u-blox/blueprints_sho_altium/Designs/B225_NINA-B112_carrier_small/BOM/B225 NINA-B112 CS_B_MFG_BOM.xlsx

Description | Designator | Footprint | Quantity | Manufacturer | Manufacturer P/N | Manufacturer Part Number
Chip Capacitor, 0.1 uF, +/- 5%, 16 V, 0402 (1005 Metric) | C1, C2 | CAPC1005X56X25ML10T15 | 2
Diode, ESD9B, 3.3V, ST5G, SOD-923 | D1, D2 | SOD-923 | 2 | ON Semiconductor | ESD9B3.3ST5G
LED, RGB Diffused SMT, PLCC4 4 Pin | D3 | 4-PLCC | 1 | Cree, Inc. | CLMVB-FKA-CFHEHLCBB7a363
Chip Inductor, 56 nH, +/-5%, 390 mA, -55 to 125 degC, 0603 (1608 Metric), RoHS, Tape and Reel | L1, L2 | INDC1608X100X30LL20T10 | 2 | Murata
1.5M screw mounting hole, plated | MH1, MH2 | MH_M1.5 | 2
THT Angled Pin Header WR-PHD, Pitch 2.54 mm, Single Row, 8 pins | P1 | 61300811021 | 1 | Wurth Elektronik |  | 61300811021
CON PADS FOR CBL PLUG-OF-NAILS 6-PIN NO LEGS | P2 | TC2030-IDC-NL | 1 | TAG Connect | TC2030-IDC-NL
Resistor, 499ohm, 1%, 1/16W, 0402 | R1 | RES 0402 HD | 1 | Rohm Semiconductor | MCR01MRTF4990
Resistor, 220ohm, 5%, 1/16W, 0402. | R2, R3, R4, R5, R6, R7, R8, R9, R10, R11, R15, R16, R17 | RES 0402 HD | 13 | Panasonic Electronic Components, [NoParam] | ERJ-2GEJ221X, [NoParam]
Button, Momentary SPST-NO, 0.05A, 12V, 3mm x 2.5mm | SW1, SW2 | B3U-1000P | 2 | Omron Electronics Inc-EMC Div | B3U-1000P
u-blox NINA-B112 Bluetooth 5 LE module | U1 | NINA_LGA42R_1400X1000X380_PIFA | 1 | u-blox
