u-blox/blueprints_sho_altium/Designs/B233_NORA-B106_carrier_small/BOM/B233 NORA-B106 CS_A_MFG_BOM.xlsx

Description | Designator | Footprint | Quantity | Manufacturer | Manufacturer P/N | Manufacturer Part Number
CAP CER X5R 0402 | C1 | Cap 0402 | 1 | Samsung Electro-Mechanics | CL05A104KP5NNN
Testpoint, Round 1.0mm Dia | CTS_NET1, RTS_NET1 | TP10R | 2
Diode, ESD9B, 3.3V, ST5G, SOD-923 | D1, D2 | SOD-923 | 2 | ON Semiconductor | ESD9B3.3ST5G
LED, RGB Diffused SMT, PLCC4 4 Pin | D3 | 4-PLCC | 1 | Cree, Inc. | CLMVB-FKA-CFHEHLCBB7a363
Chip Inductor, 22 nH, +/-5%, 640 mA, -55 to 125 degC, 0603 (1608 Metric), RoHS, Tape and Reel | L1, L2 | INDC1608X100X30LL20T10 | 2 | Murata
2M screw mounting hole, plated | MH1, MH2 | MH_M2 | 2
CON PADS FOR CBL PLUG-OF-NAILS 6-PIN NO LEGS | P1 | TC2030-IDC-NL | 1 | TAG Connect | TC2030-IDC-NL
THT Angled Pin Header WR-PHD, Pitch 2.54 mm, Single Row, 8 pins | P2 | 61300811021 | 1 | Wurth Electronics |  | 61300811021
Resistor, 220ohm, 5%, 1/16W, 0402. | R1, R2, R3, R4, R5, R6, R7, R8, R9, R10, R11, R12, R13, R15, R16 | RES 0402 HD | 15 | Panasonic Electronic Components | ERJ-2GEJ221X
Resistor, 499ohm, 1%, 1/16W, 0402 | R14 | RES 0402 HD | 1 | Rohm Semiconductor | MCR01MRTF4990
Button, Momentary SPST-NO, 0.05A, 12V, 3mm x 2.5mm | SW1, SW2 | B3U-1000P | 2 | Omron Electronics Inc-EMC Div | B3U-1000P
u-blox NORA-B106 Bluetooth 5.2 LE module - dual core | U1 | NORA_LGA82R_1430X1040X180_ANT | 1 | u-blox | NORA-B106-00B
XTAL, 2Pin, 32.768kHz, 7pF 20ppm | X1 | XTAL_3215 | 1 | Epson | FC-135 32.7680KA-AG3
