u-blox/blueprints_sho_altium/Designs/B228_NINA-B306_carrier_mid/Documentation/B228 B.PDF

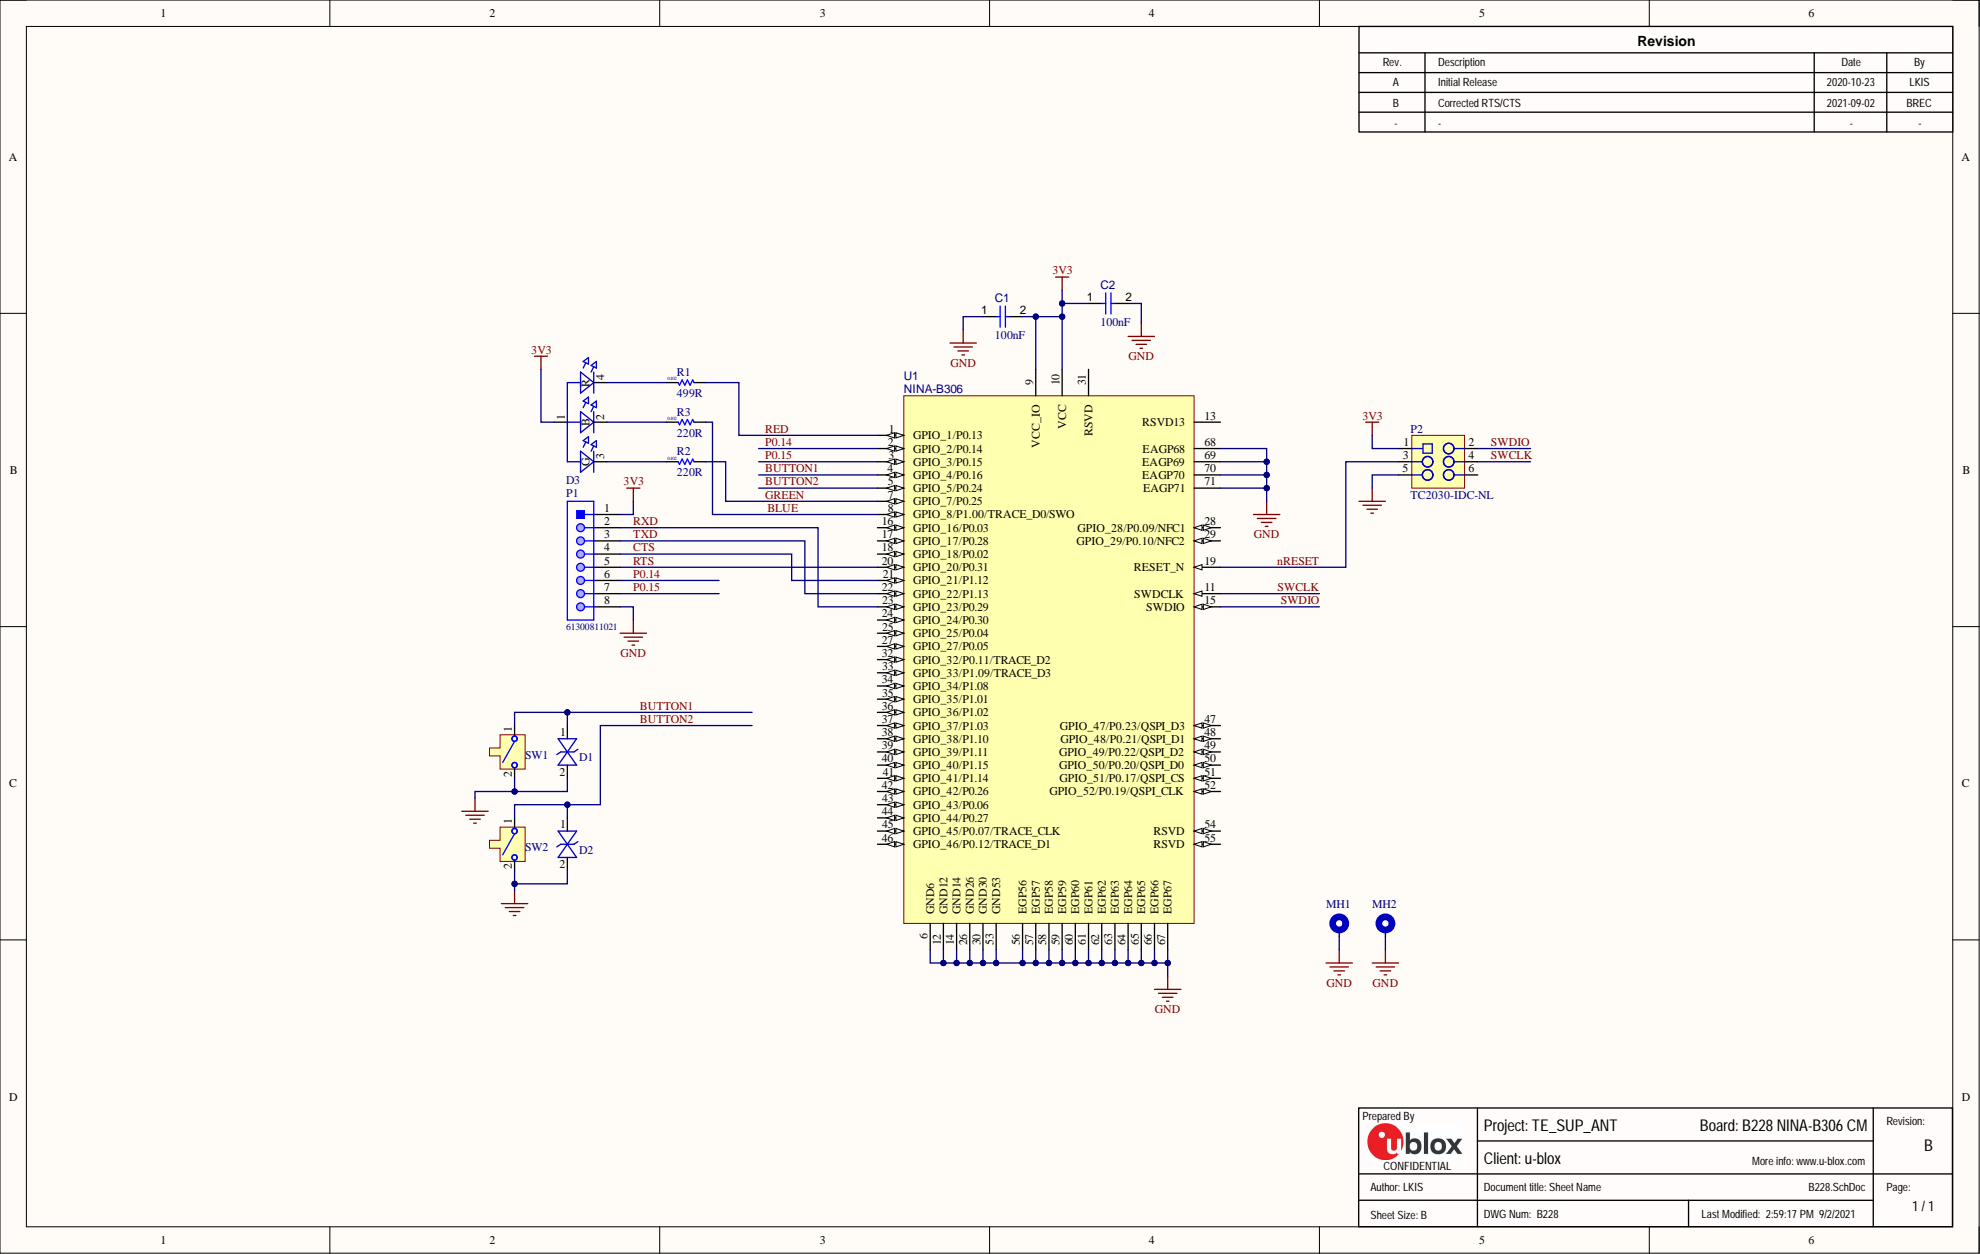
[picture p19: page 1]

Rev. | Description | Date | By
A | Initial Release | 2020-10-23 | LKIS

B | Corrected RTS/CTS | 2021-09-02 | BREC

P0.14 P0.15 BUTTON1 BUTTON2 GREEN | GPIO_2/P0.14 2 GPIO_4/P0.16 4 GPIO_3/P0.15 3 GPIO_5/P0.24 5 GPIO_7/P0.25 7

BLUE | GPIO_8/P1.00/TRACE_D0/SWO 8

3 | TXD | GPIO_17/P0.28 17
4 | CTS | GPIO_18/P0.02 18
5 | RTS | GPIO_20/P0.31 20
6 | P0.14 | GPIO_21/P1.12 21
7 | P0.15 | GPIO_23/P0.29 23 GPIO_22/P1.13 22

nRESET

GPIO_25/P0.04 25 GPIO_24/P0.30 24

More info: www.u-blox.com

Author: LKIS | Document title: Sheet Name B228.SchDoc | Page: 1 / 1

Sheet Size: B | DWG Num: B228 | Last Modified: 2:59:17 PM 9/2/2021

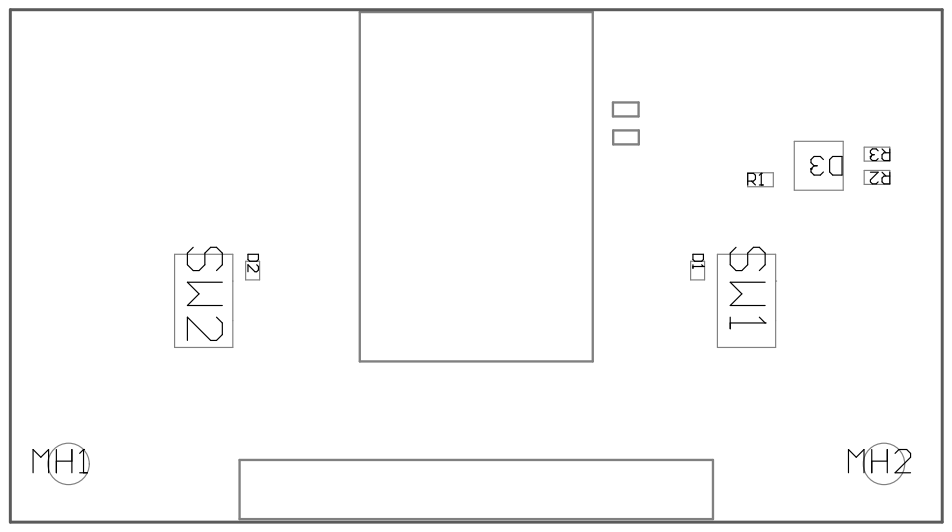
[picture p20: page 2]

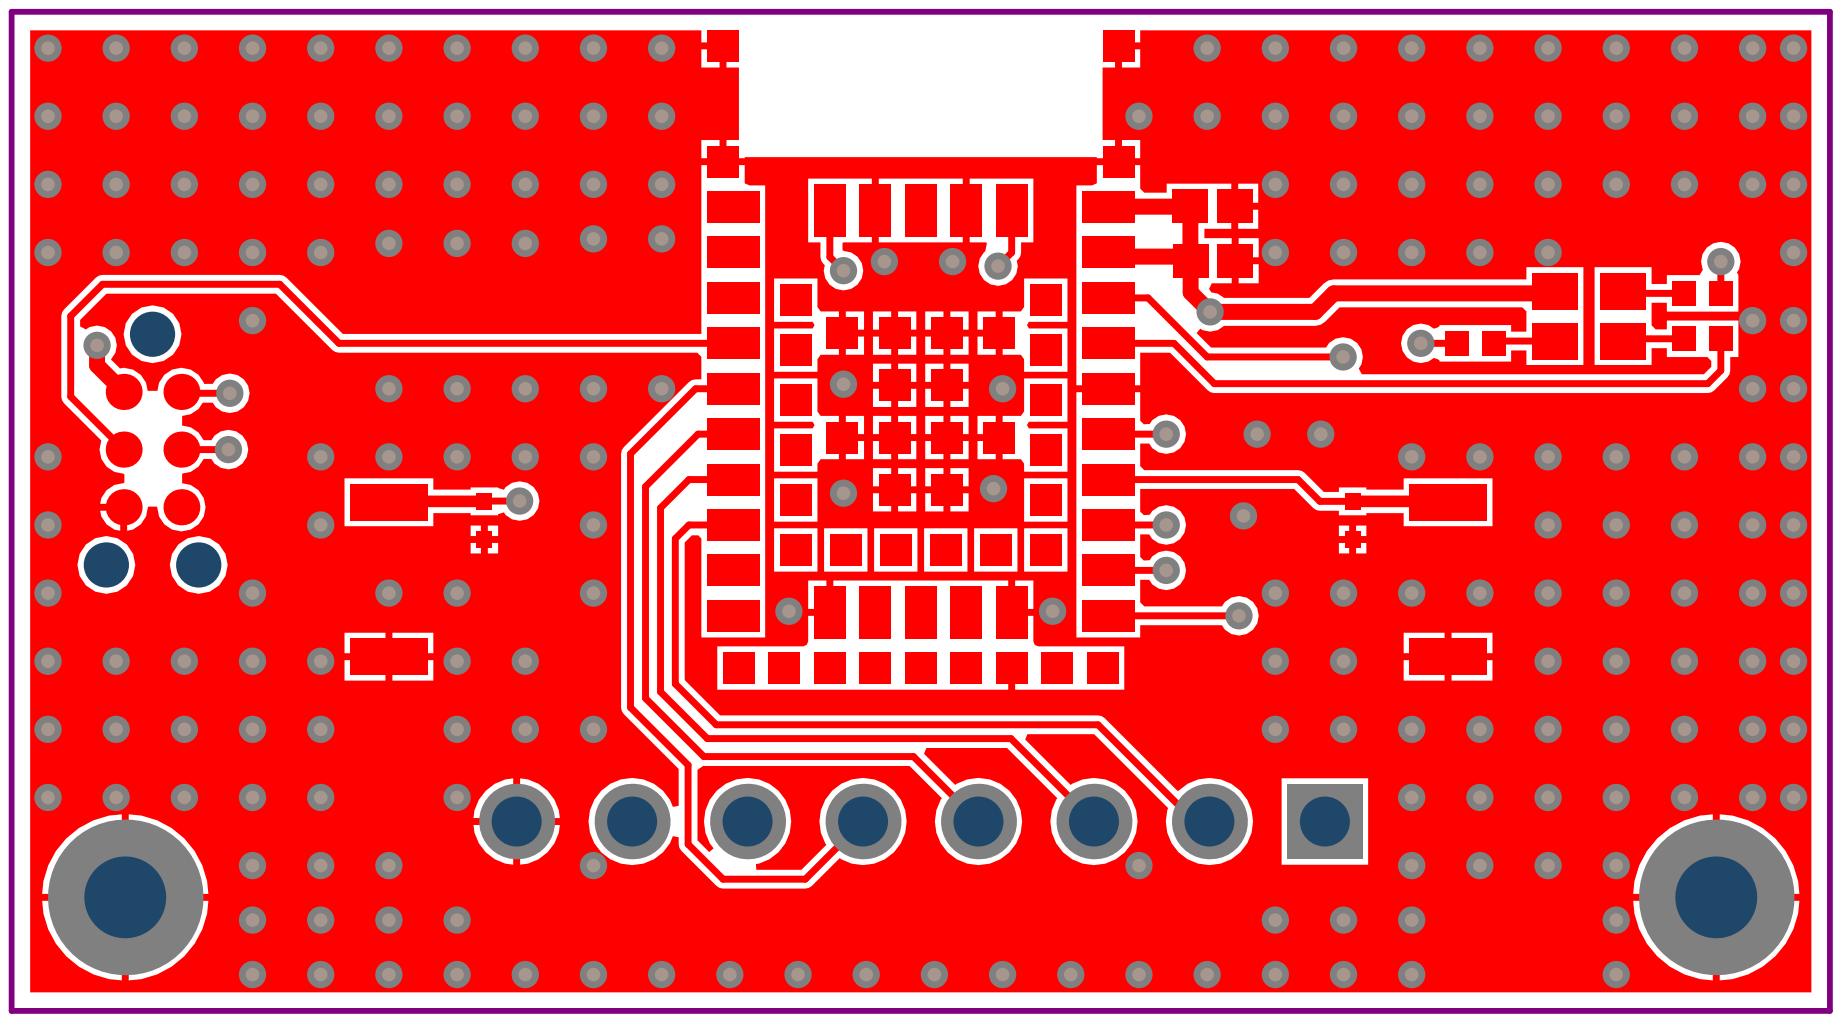
[picture p21: page 4]

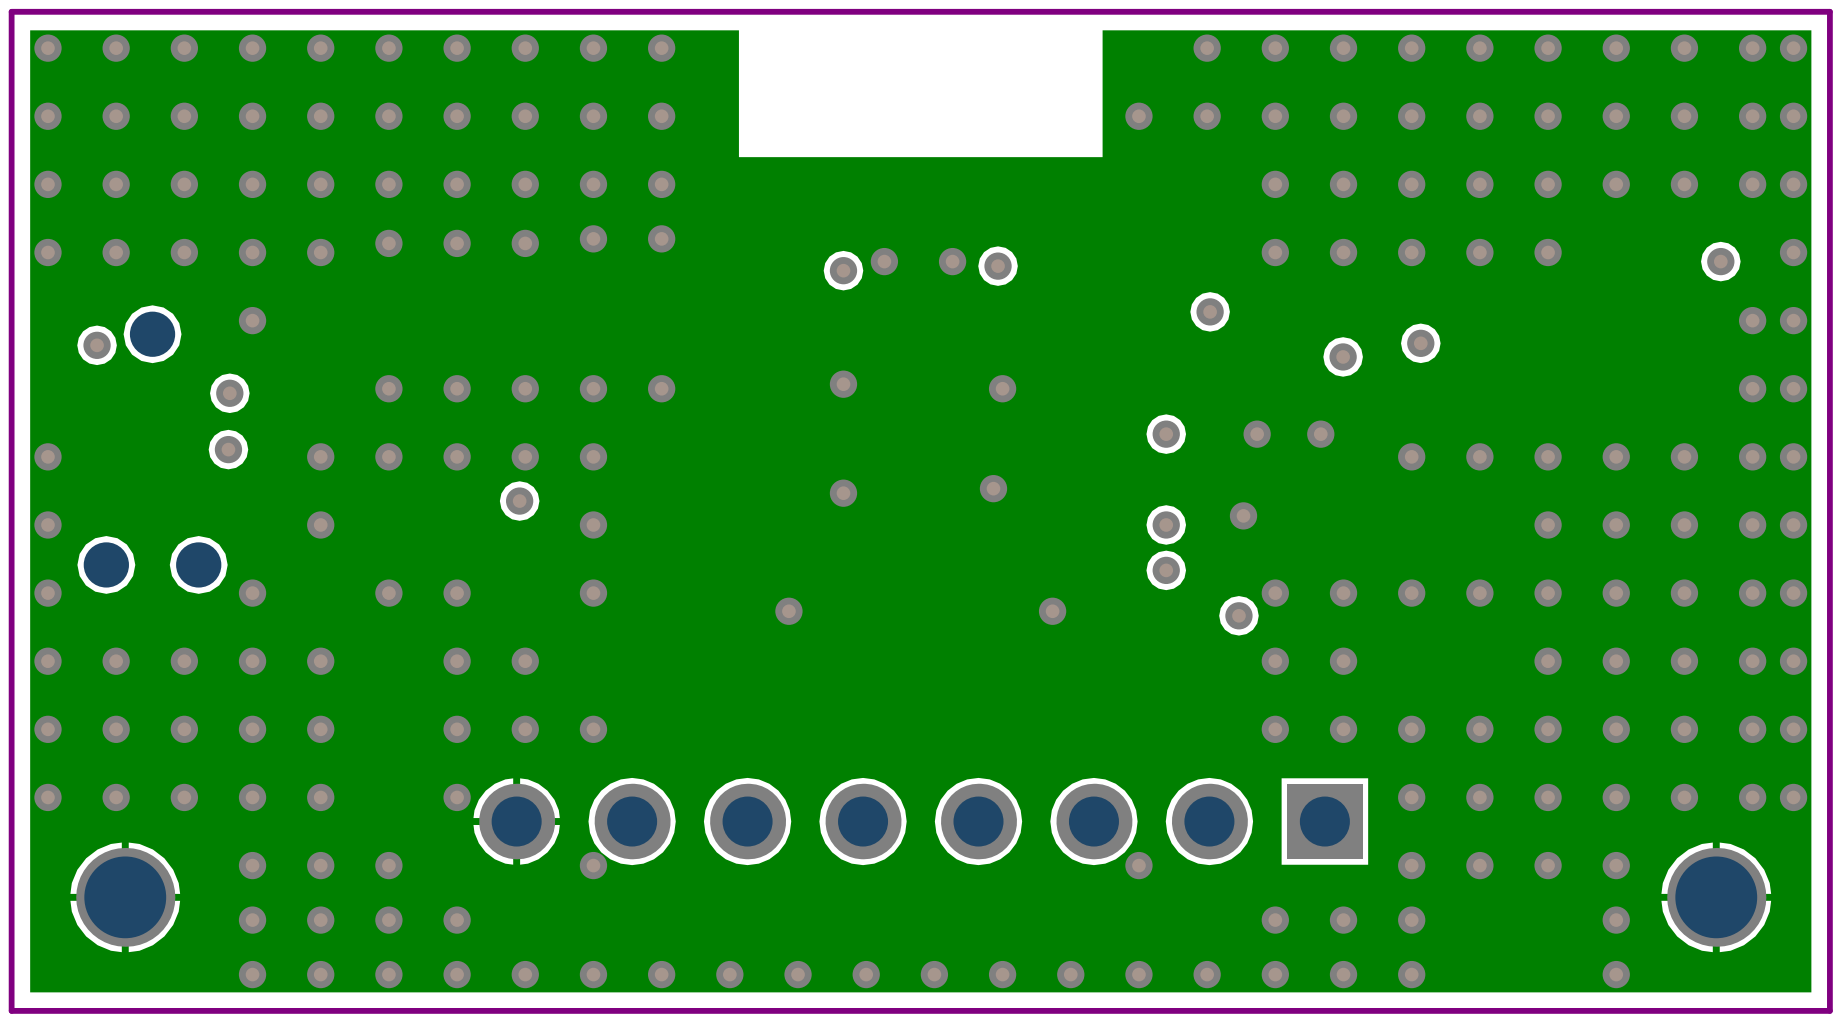
[picture p22: page 5]

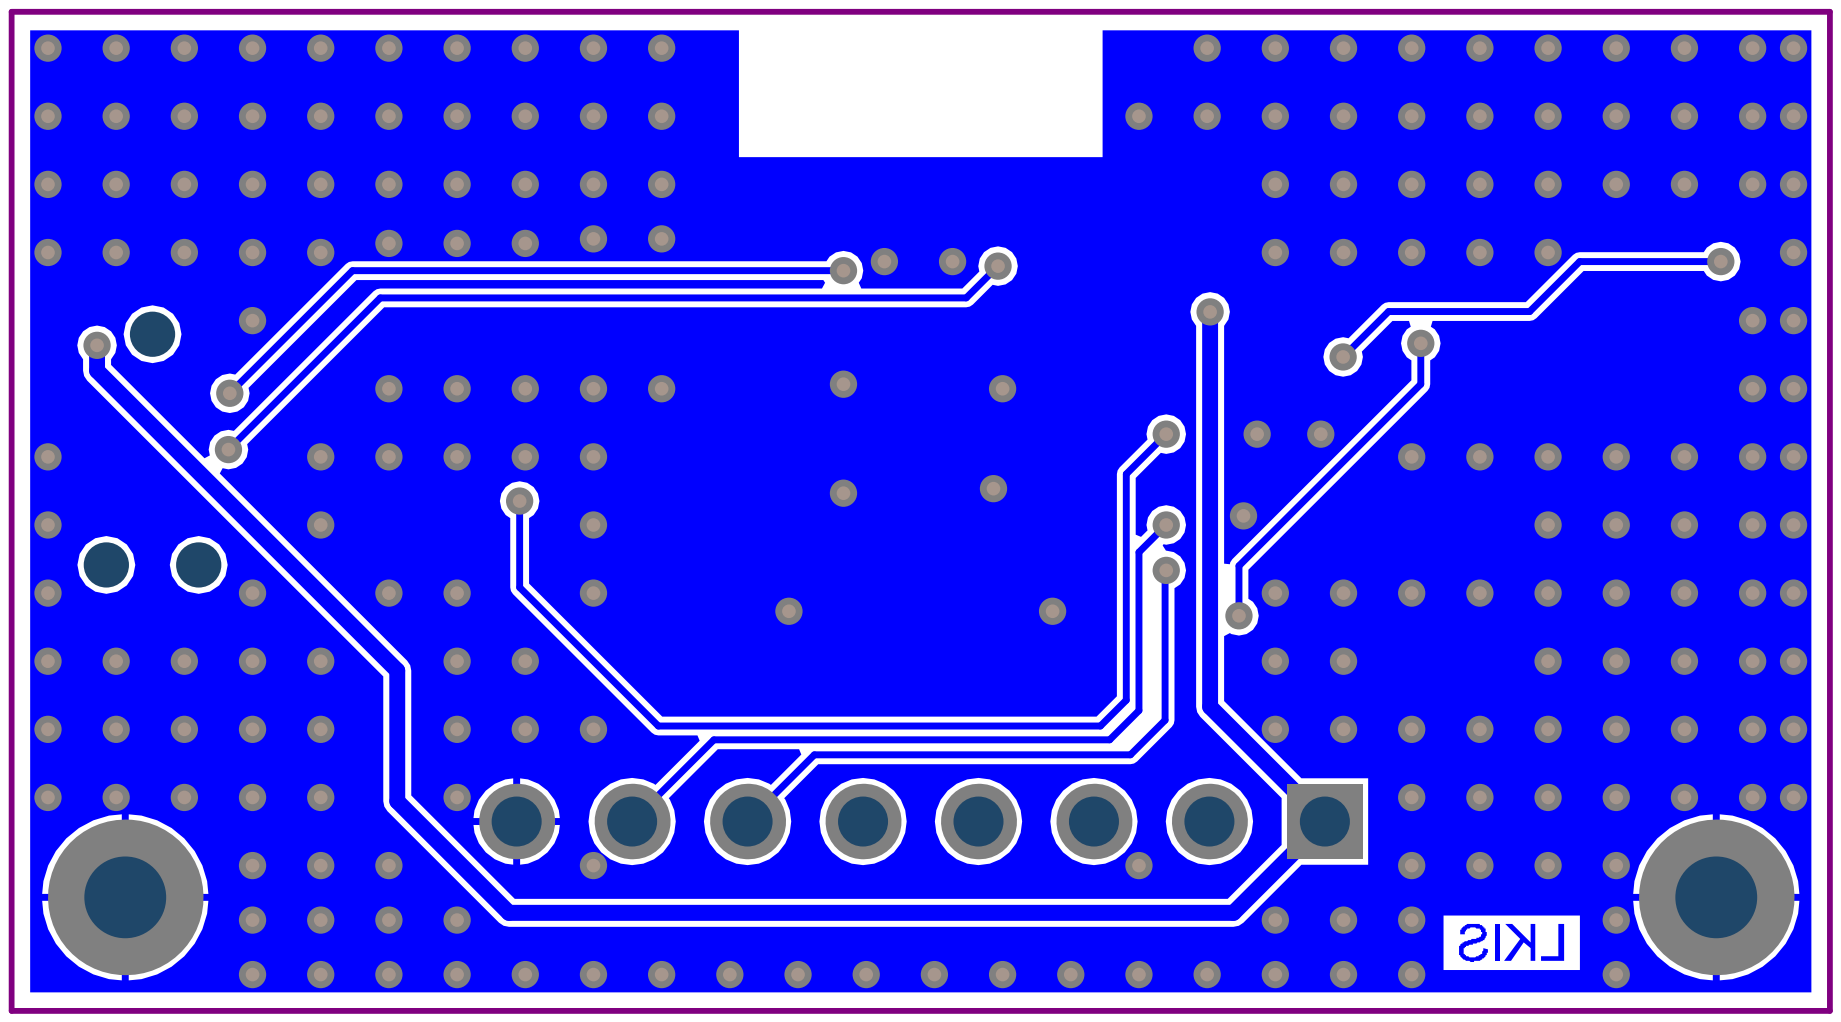
[picture p23: page 7]

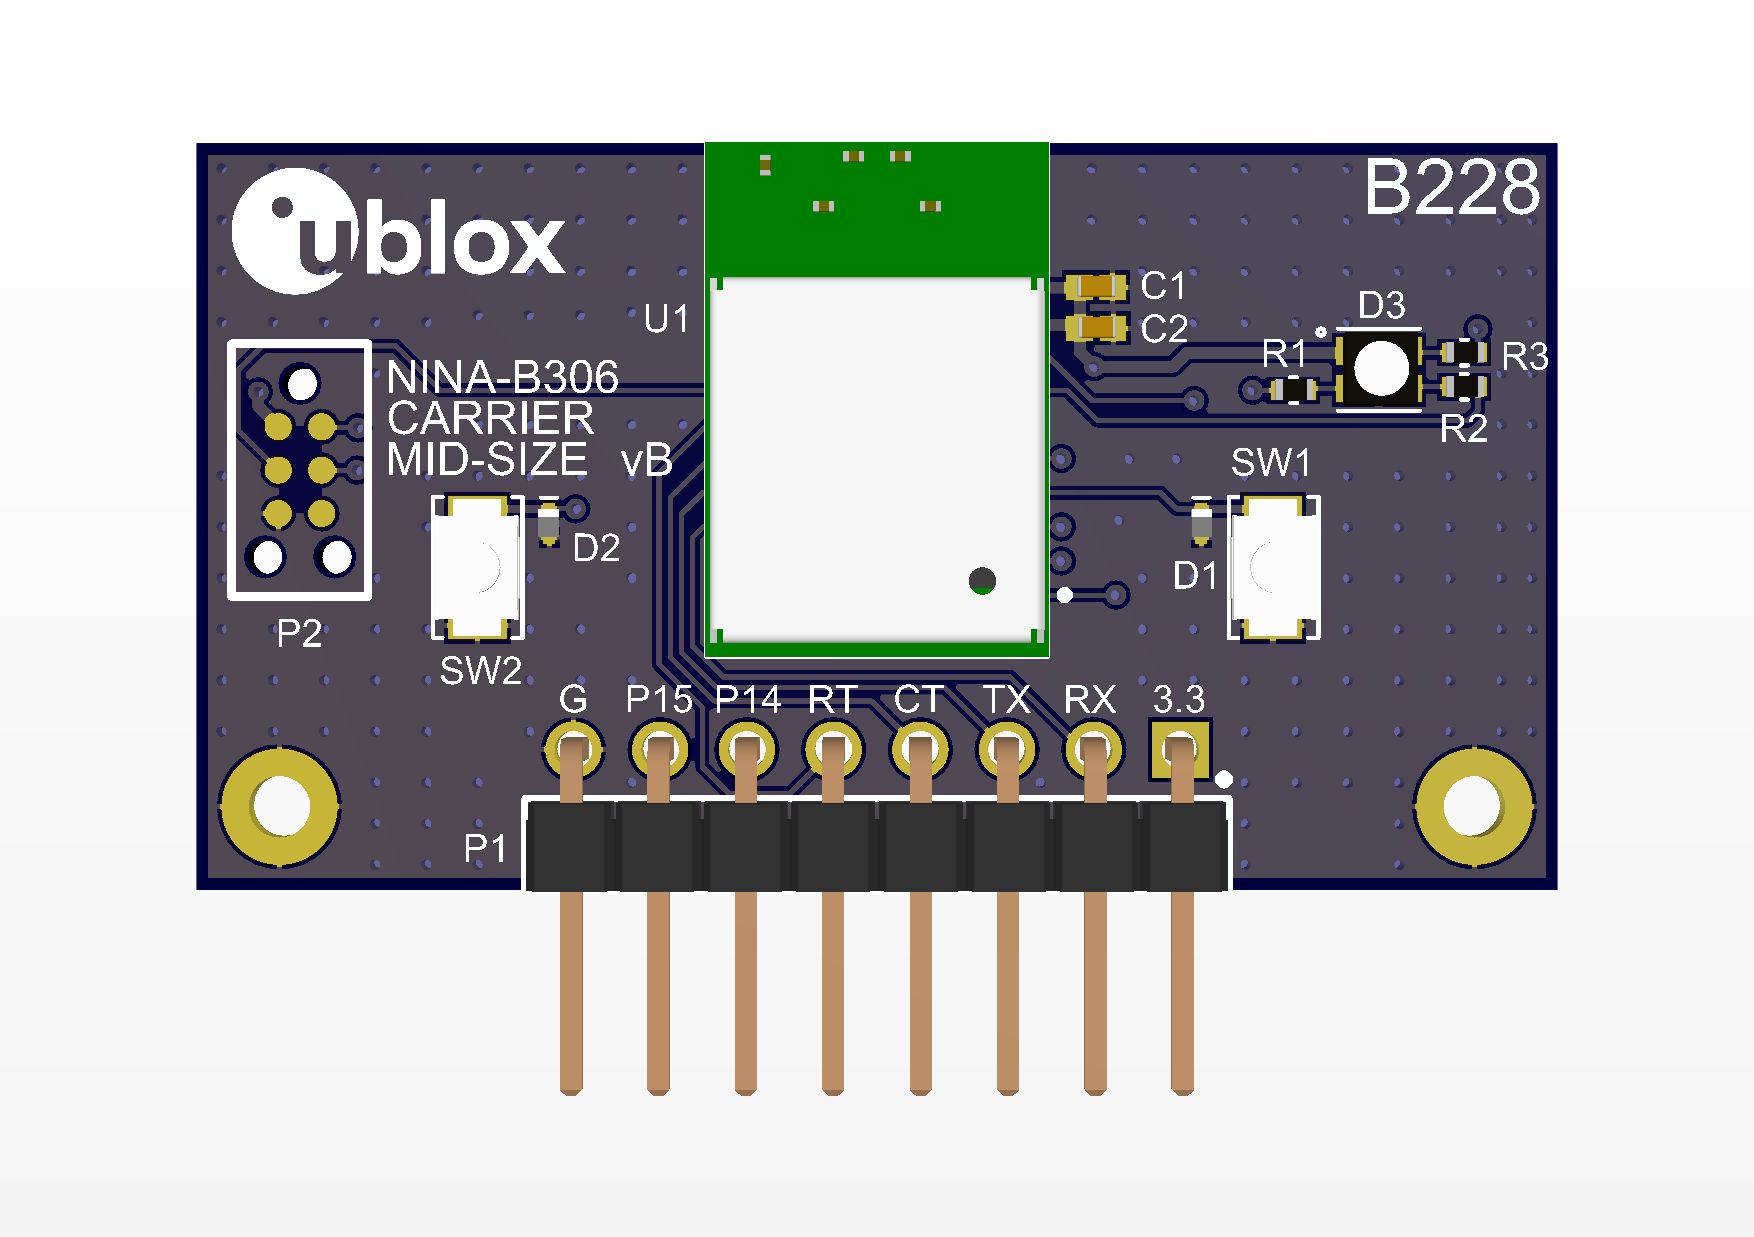
[picture p24: page 8]

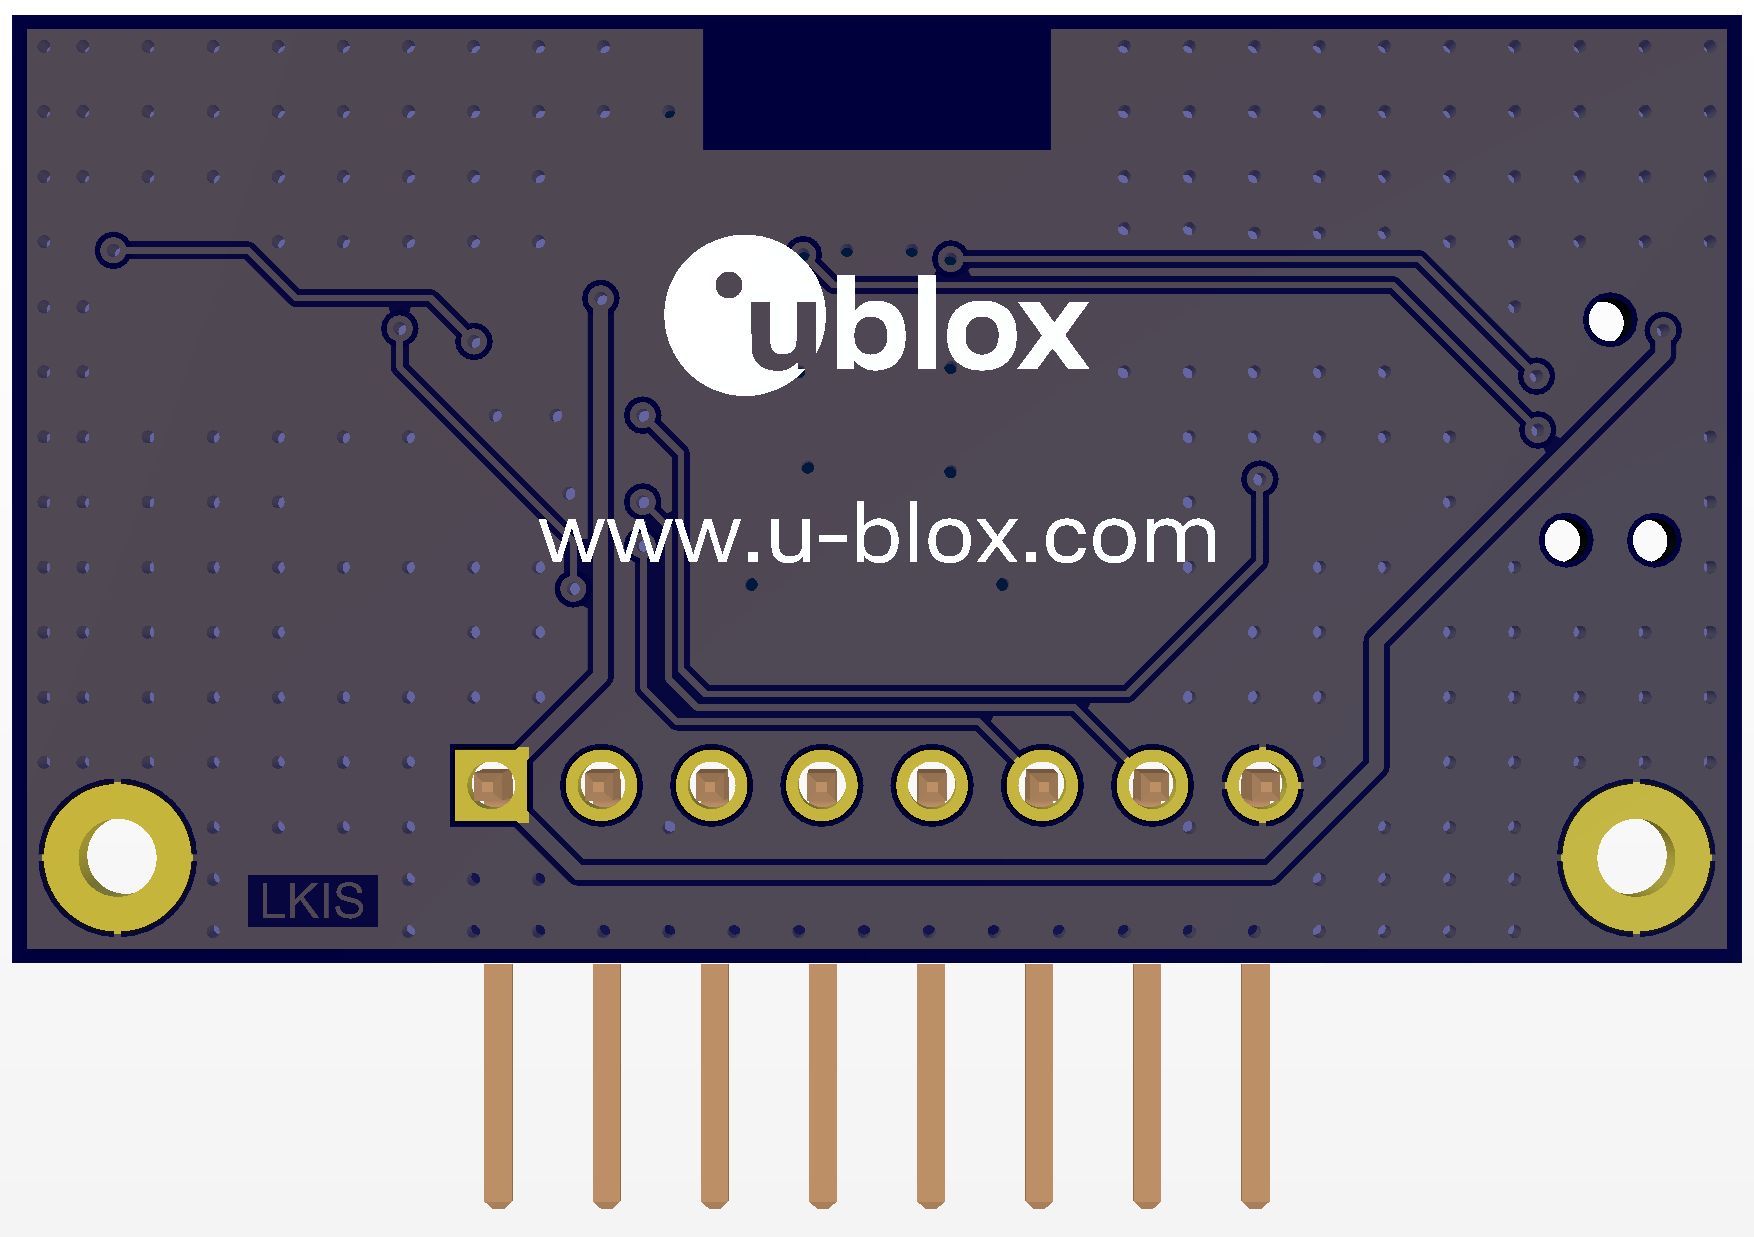
[picture p25: page 9]

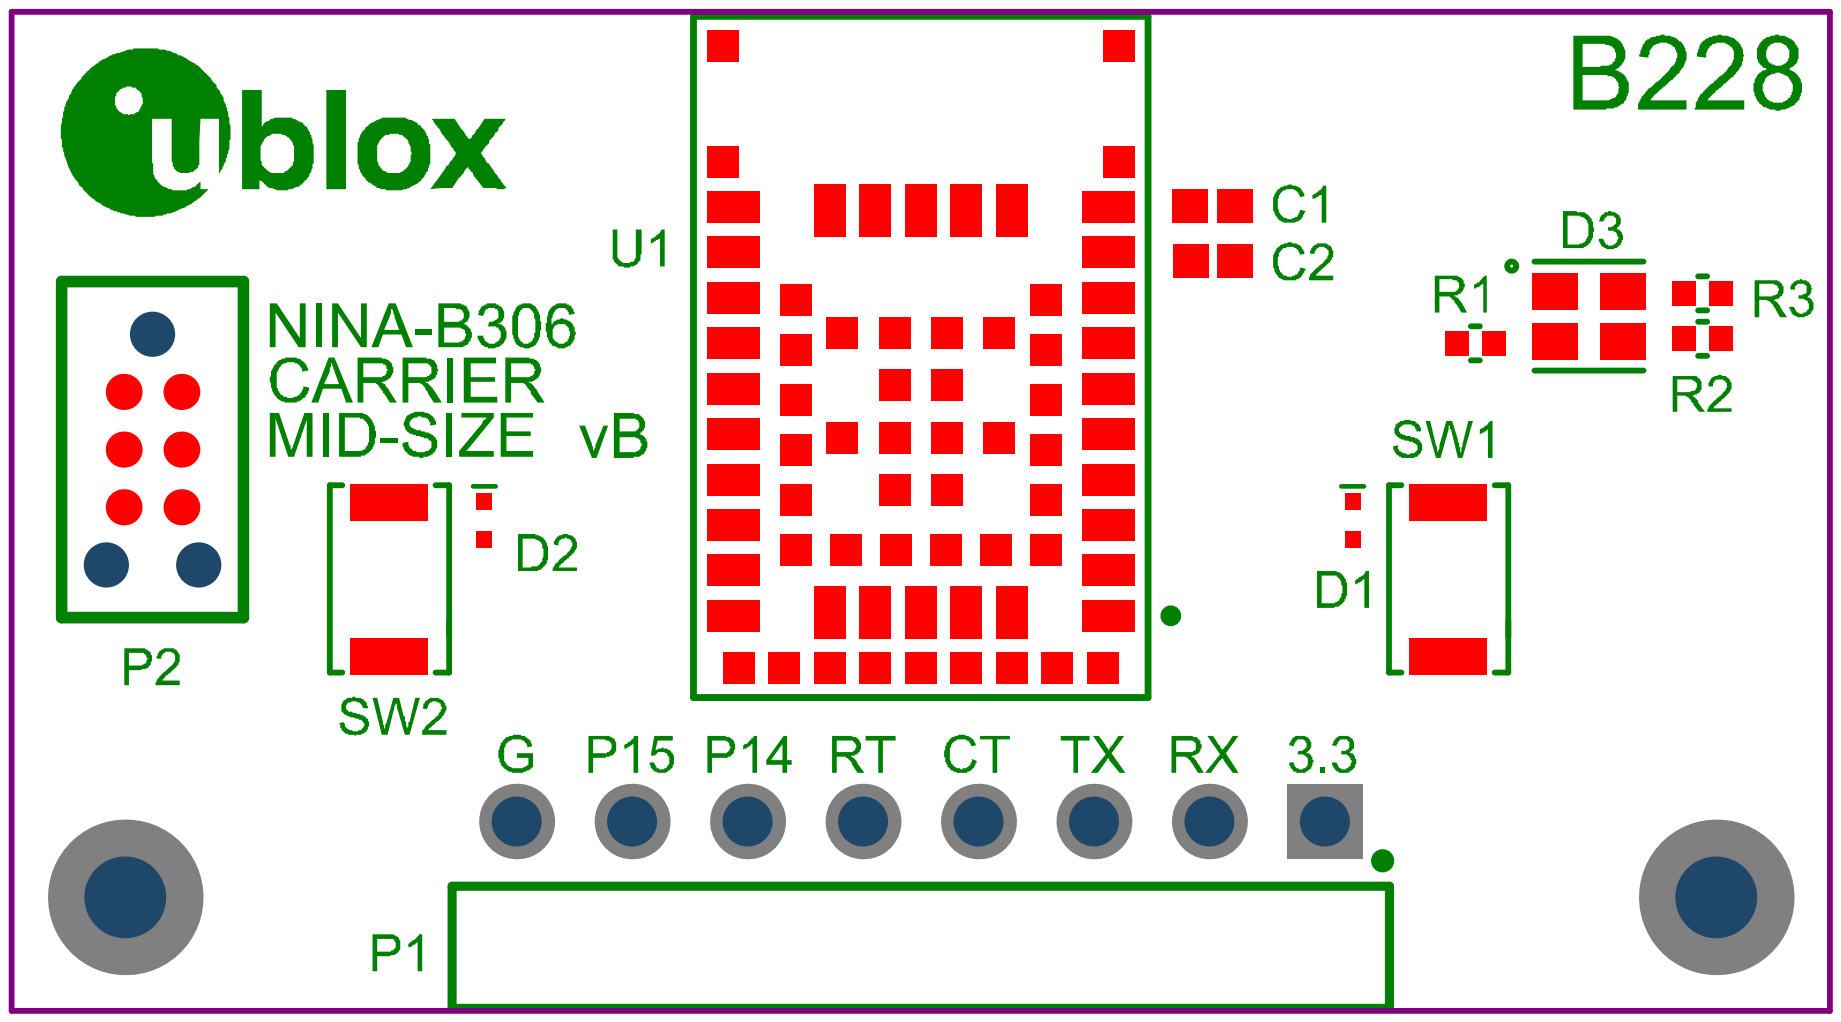
[picture p26: page 11]

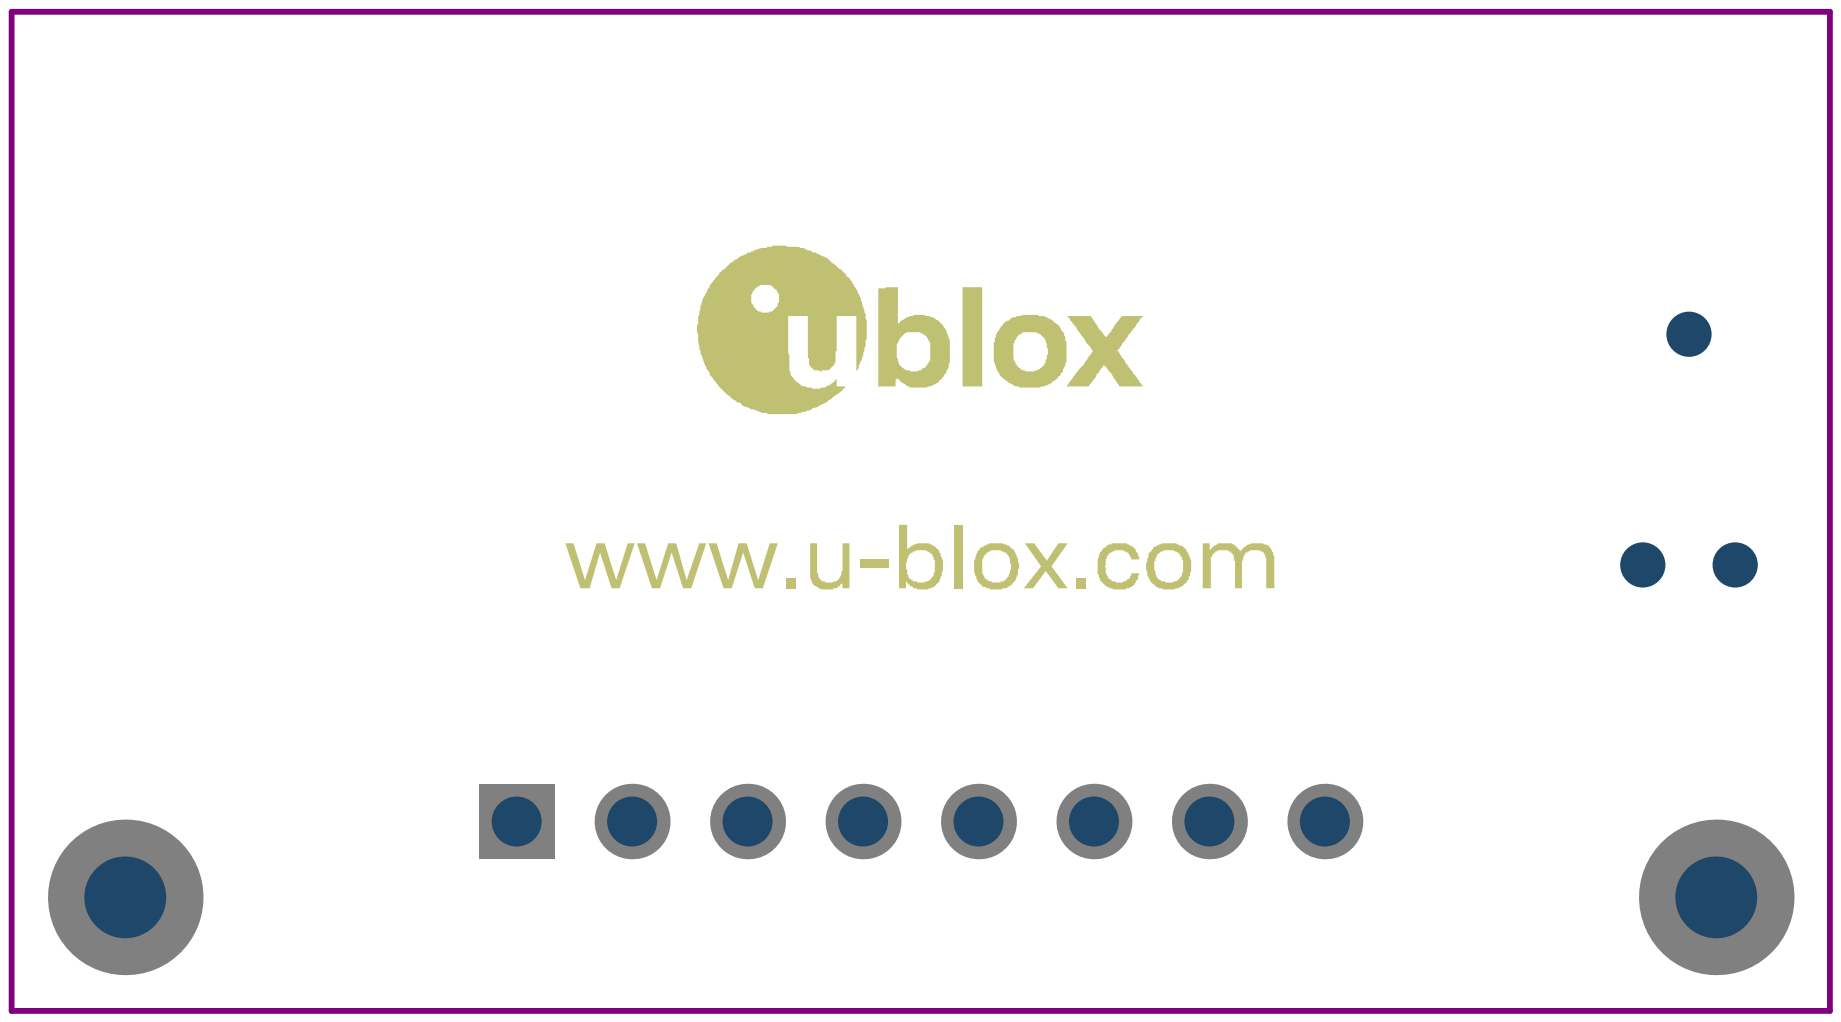
[picture p27: page 12]
