u-blox/blueprints_sho_altium/Designs/B232_NORA-B106_carrier_mid/Documentation/B232 A.PDF

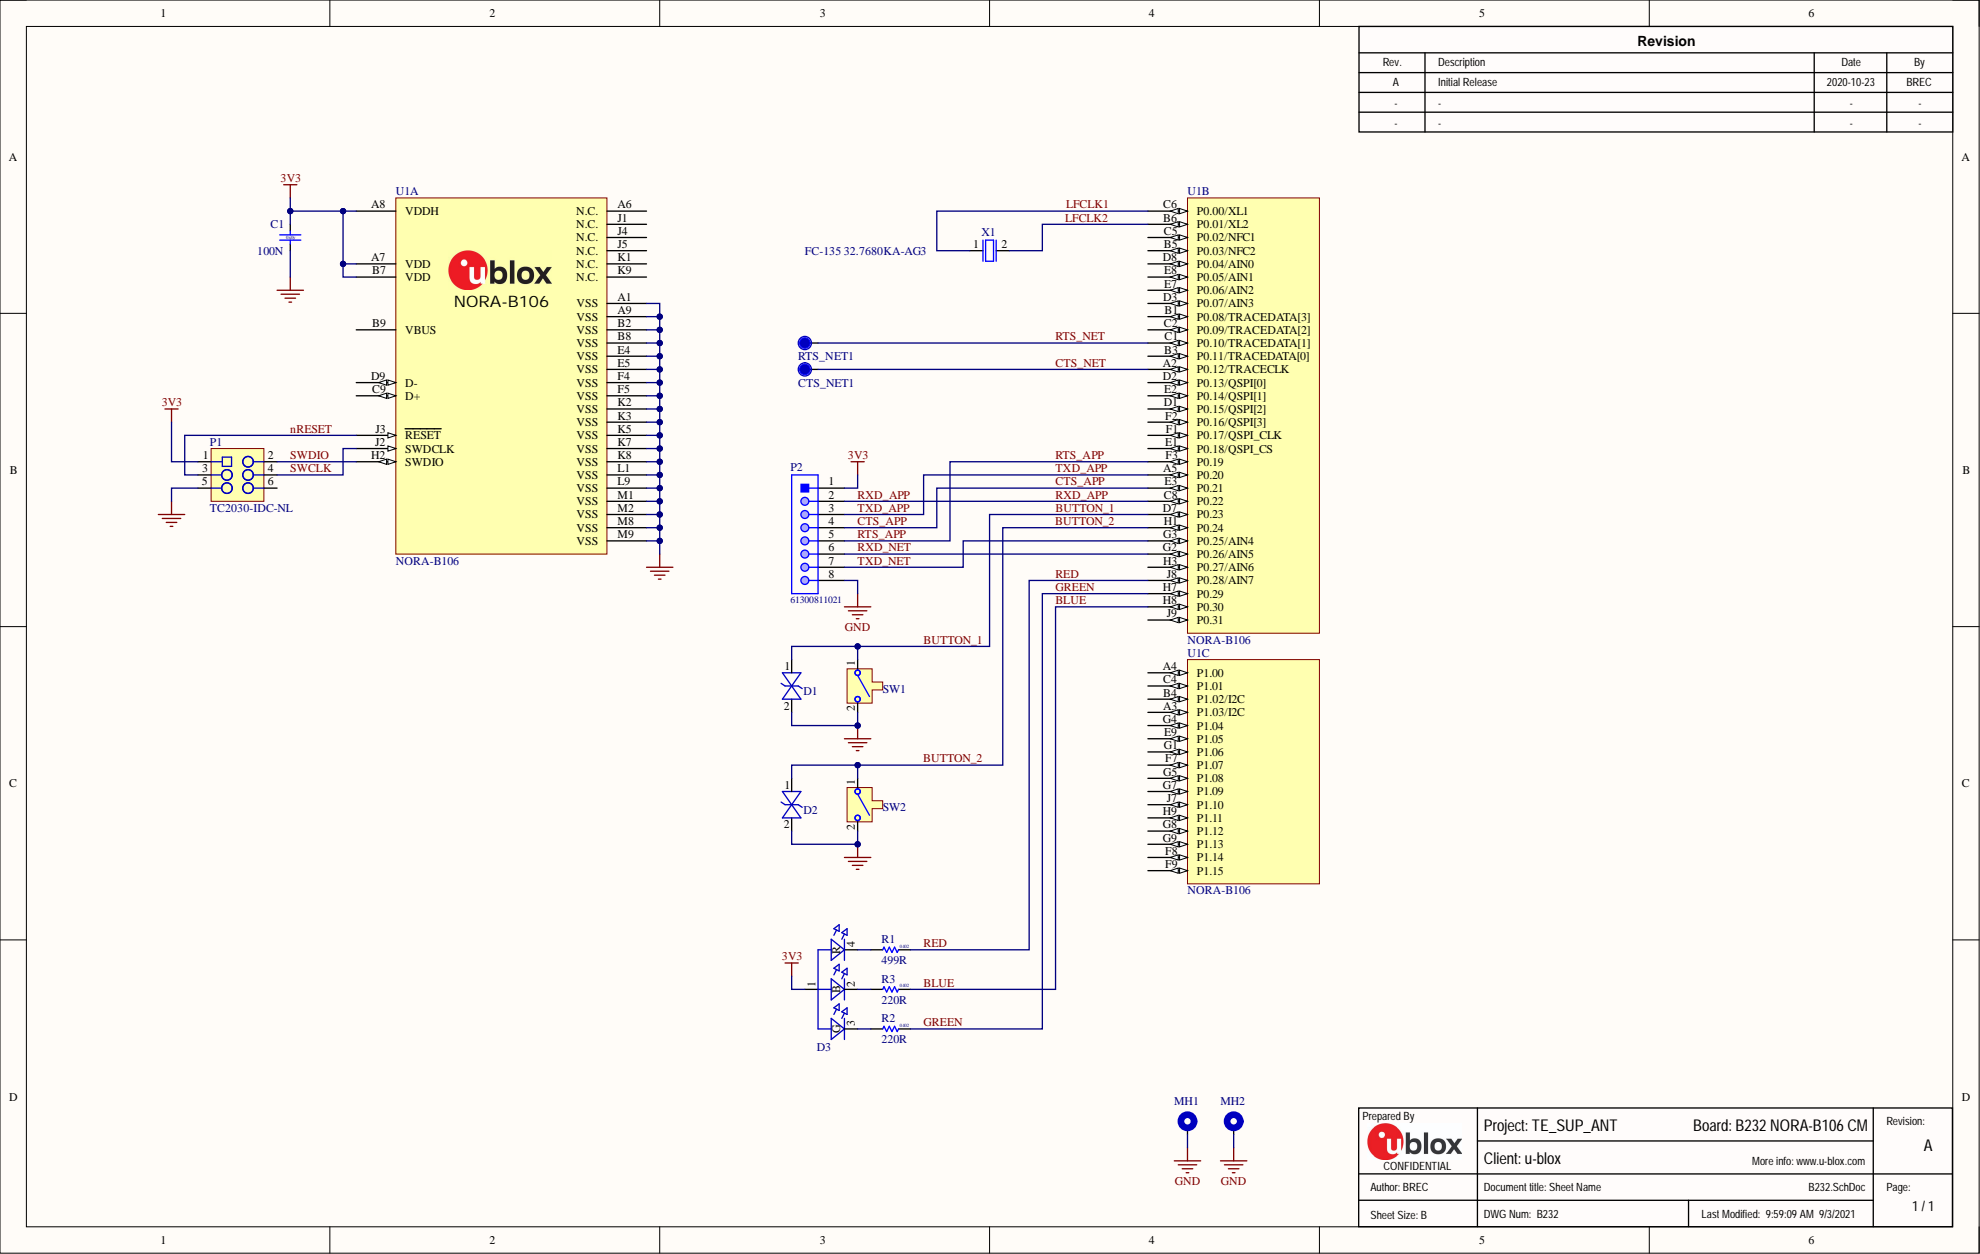
[picture p28: page 1]

Rev. | Description | Date | By
A | Initial Release | 2020-10-23 | BREC

2 | RXD_APP | P0.22 C8

CTS_APP | P0.21 E3

5 | | RTS_APP | | P0.25/AIN4 G3
6 | | RXD_NET | | P0.26/AIN5 G2
7 | | TXD_NET | | P0.27/AIN6 H3
8 | | | RED | P0.28/AIN7 J8

GREEN | | P0.29 H7
BLUE | | P0.30 H8

BUTTON_1 | | | P0.31 J9

BUTTON_2

More info: www.u-blox.com

Author: BREC | Document title: Sheet Name B232.SchDoc | Page: 1 / 1

Sheet Size: B | DWG Num: B232 | Last Modified: 9:59:09 AM 9/3/2021

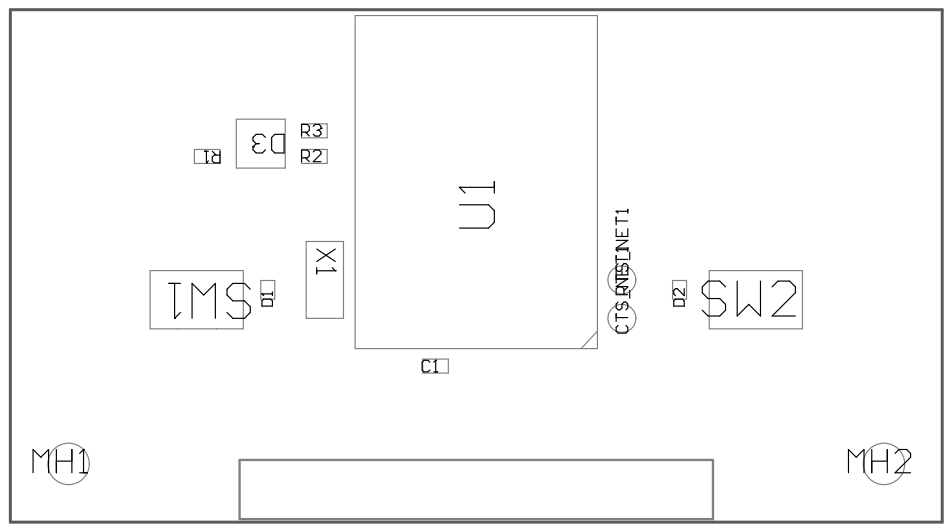
[picture p29: page 2]

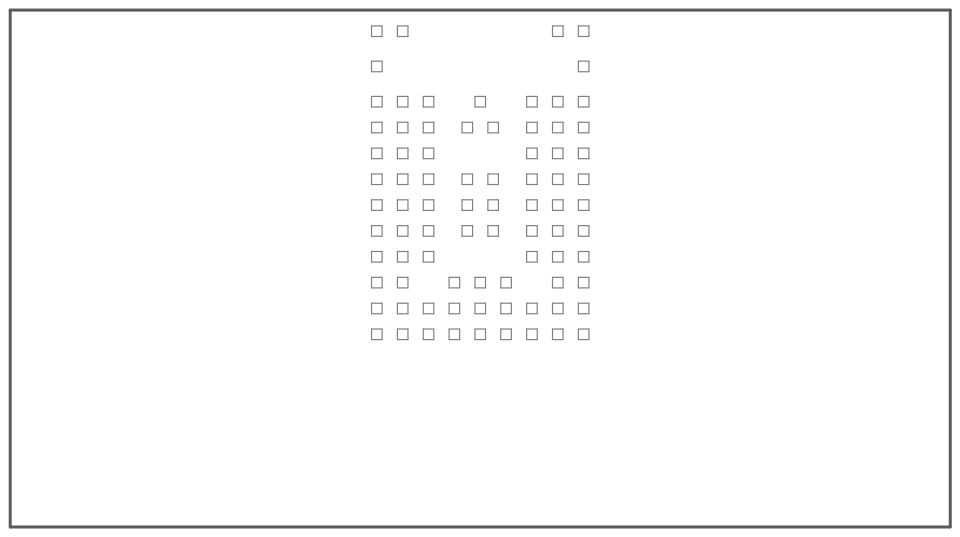
[picture p30: page 3]

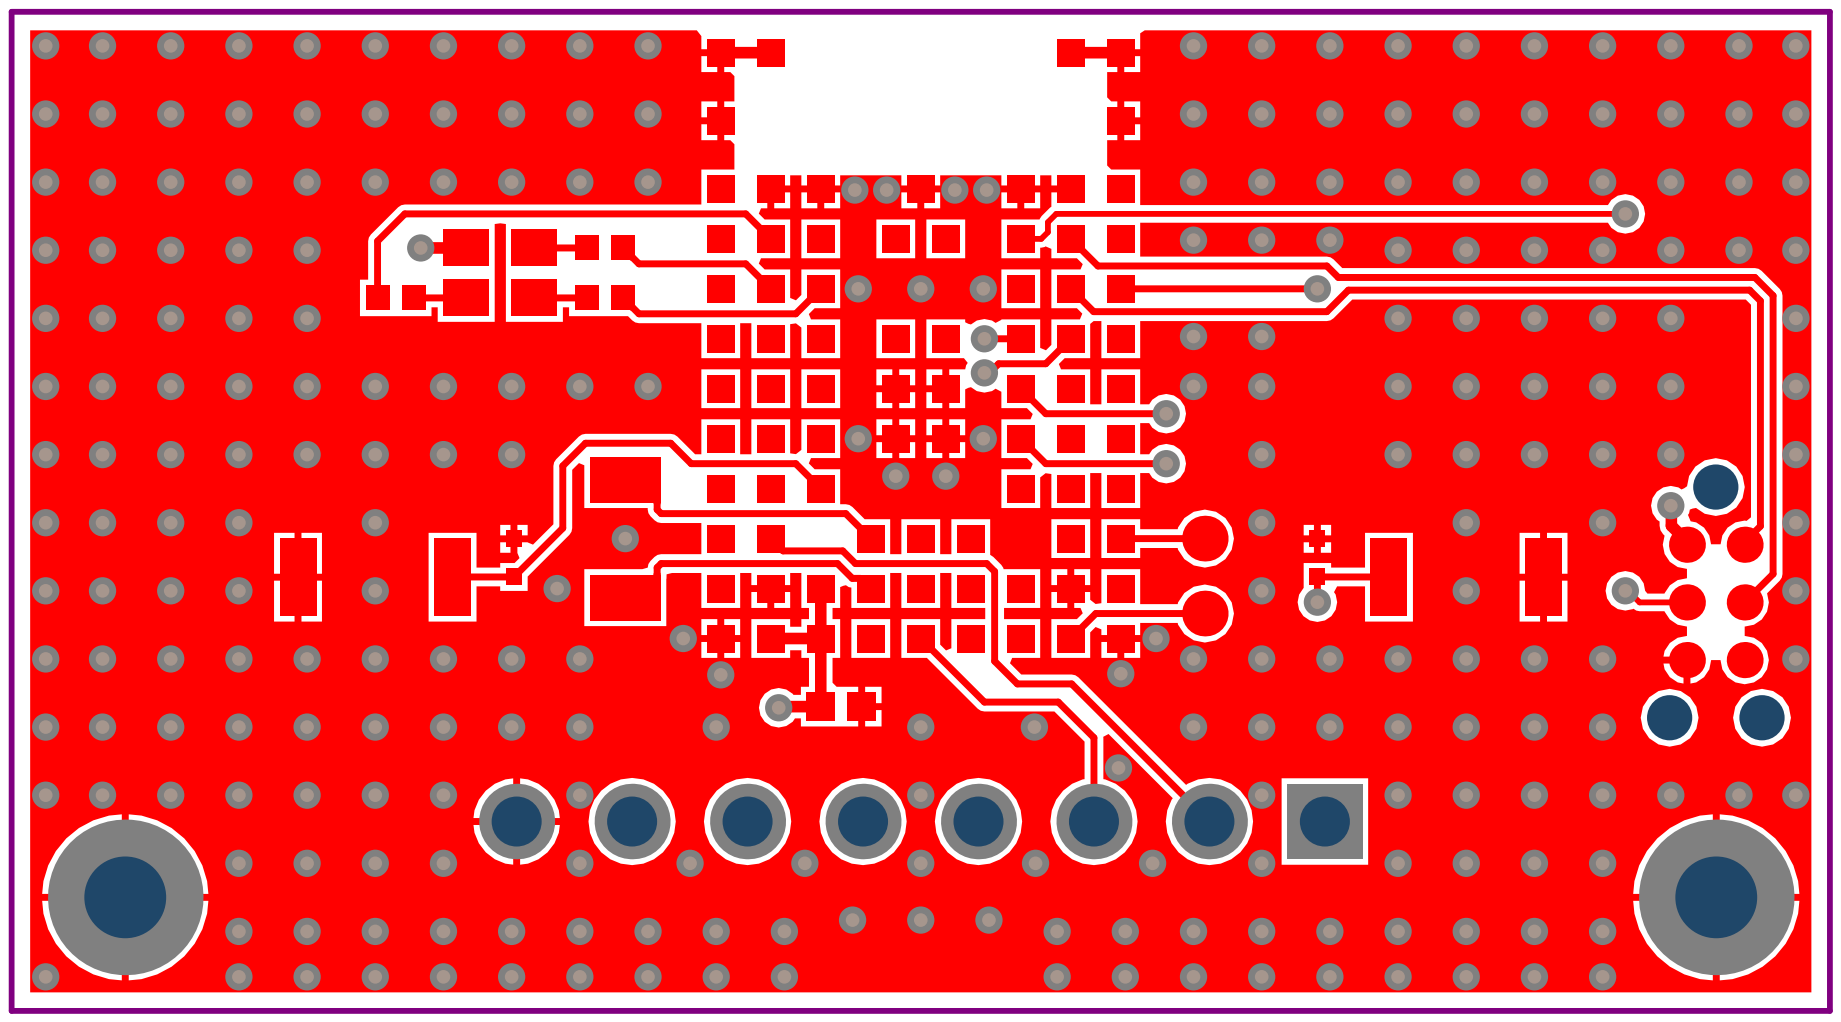
[picture p31: page 4]

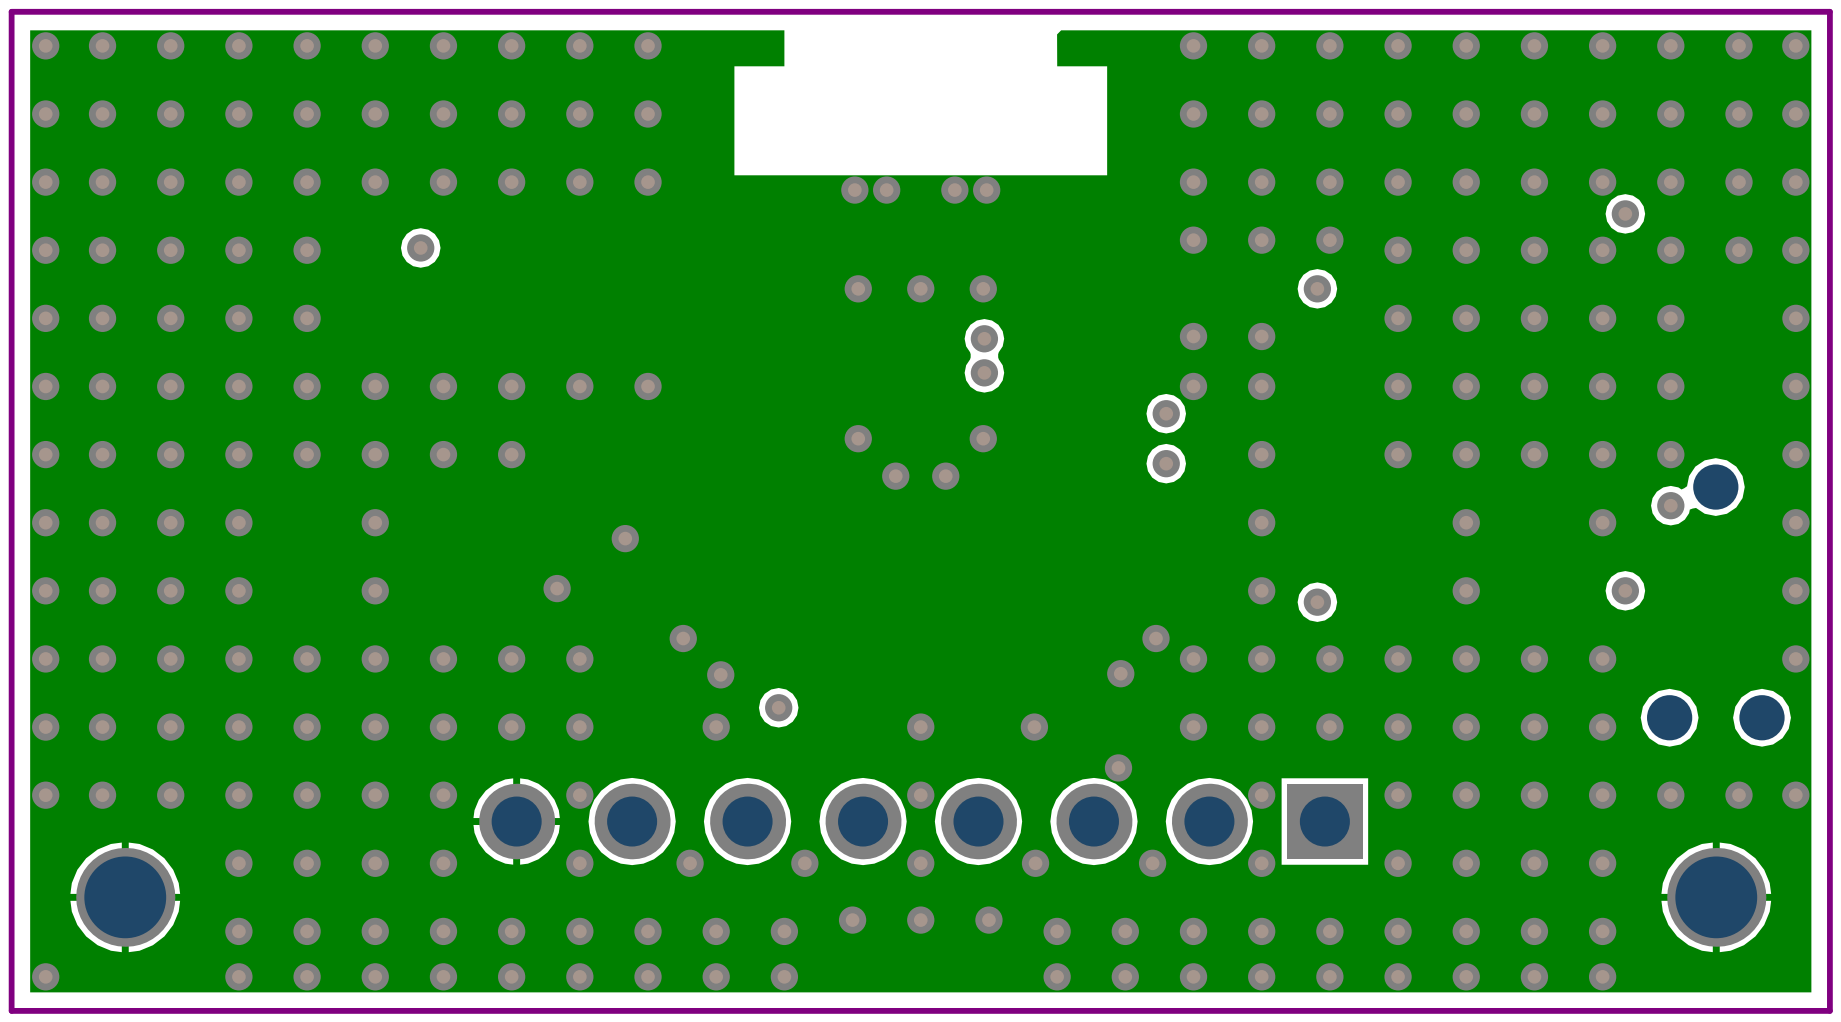
[picture p32: page 5]

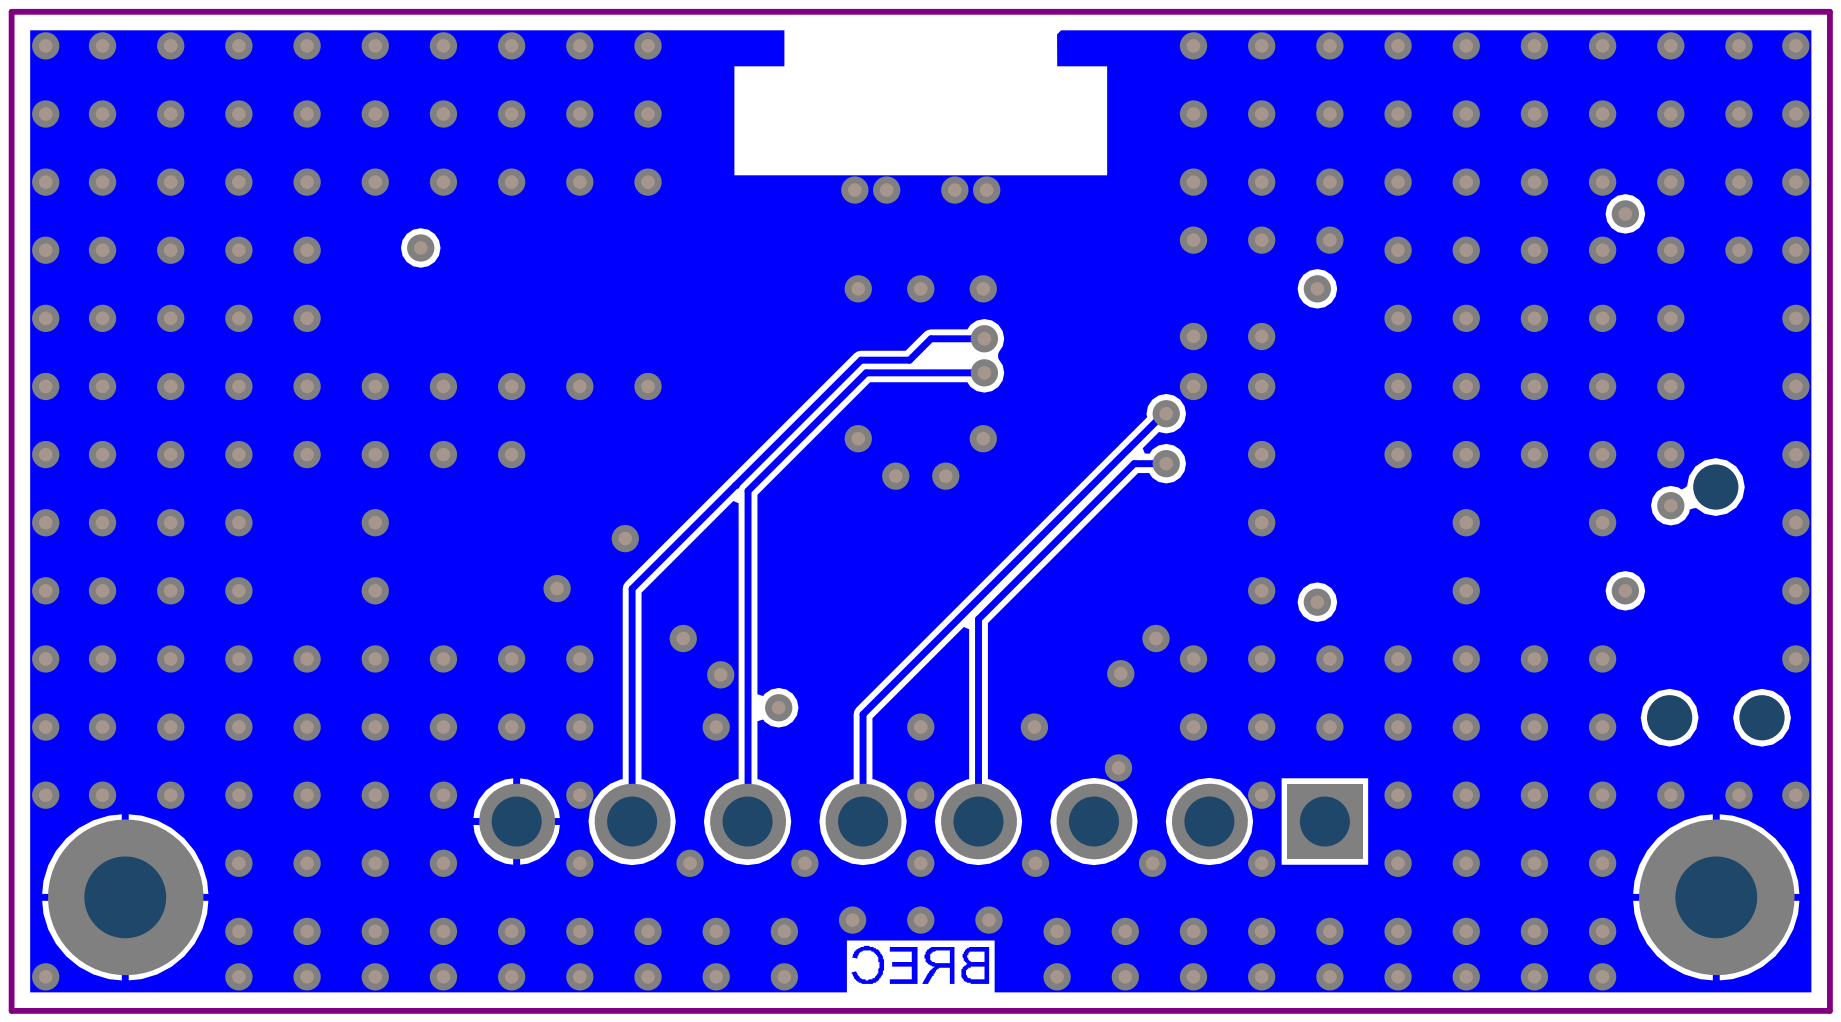
[picture p33: page 7]

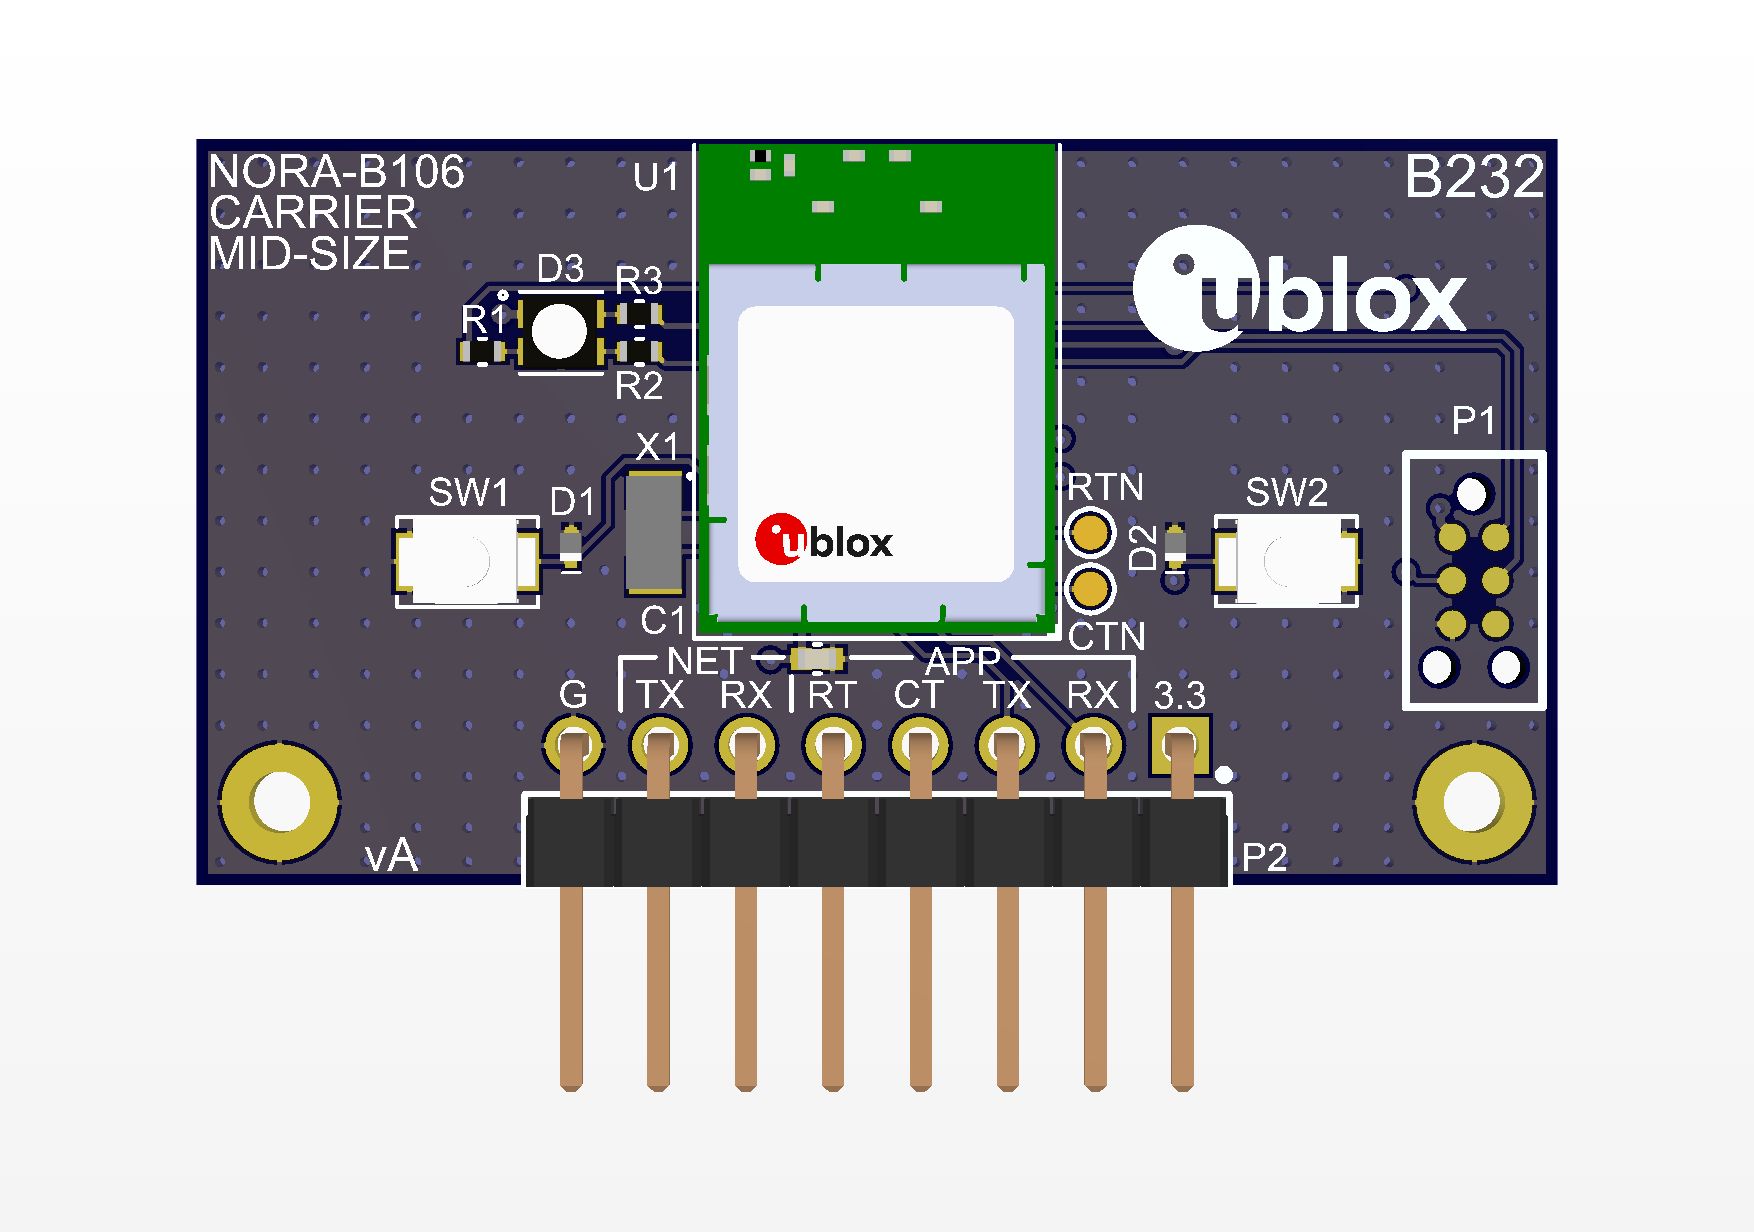
[picture p34: page 8]

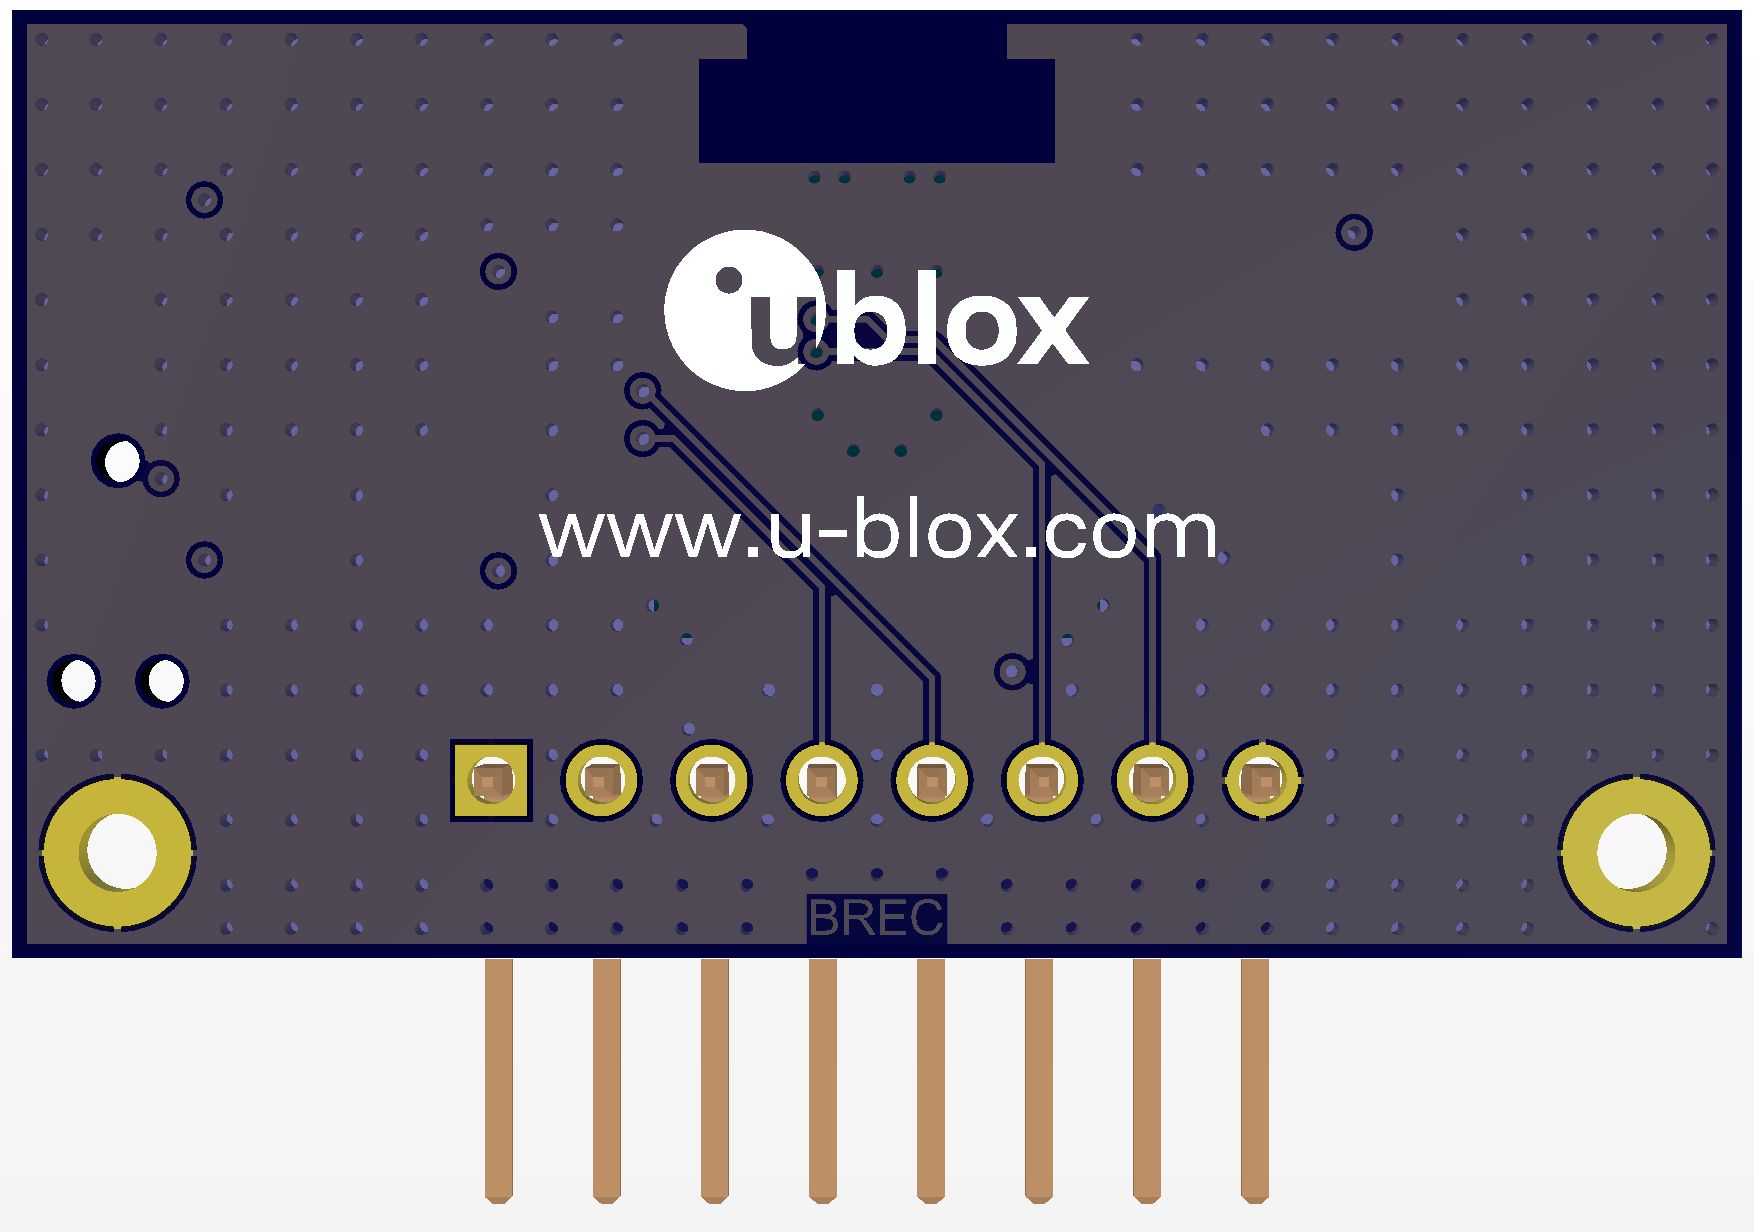
[picture p35: page 9]

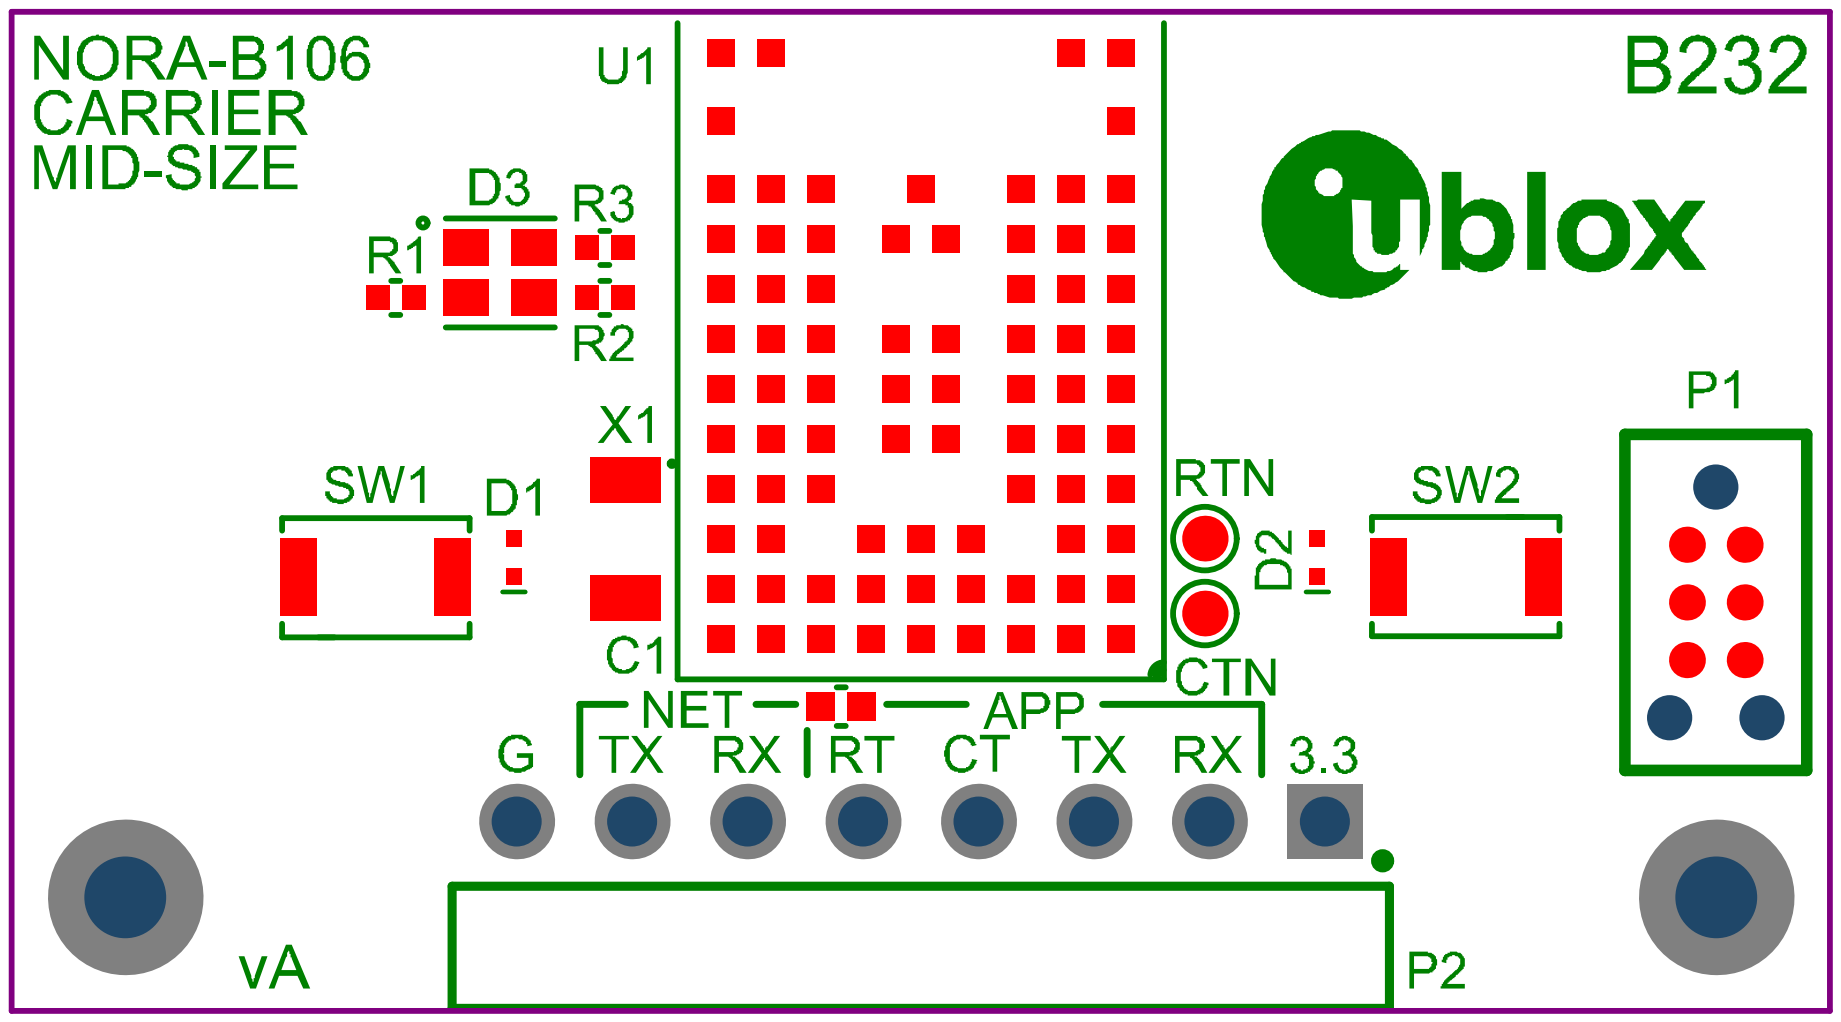
[picture p36: page 11]

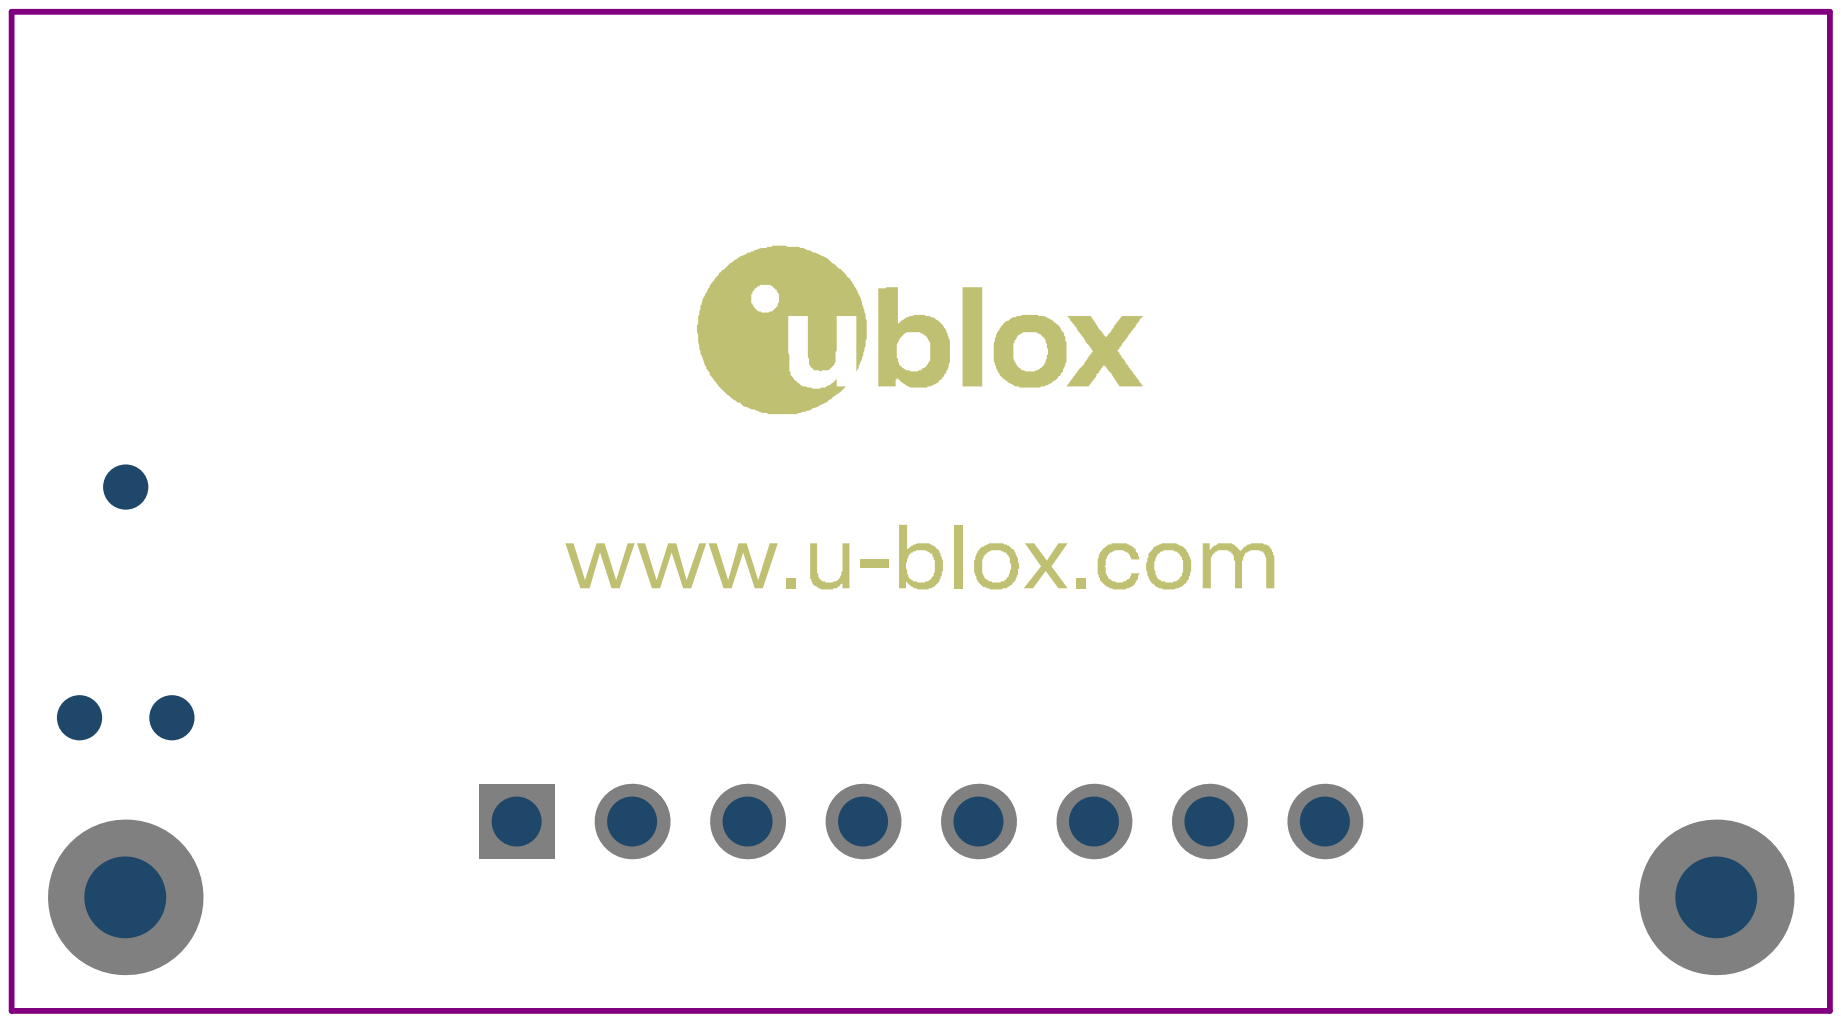
[picture p37: page 12]
