u-blox/blueprints_sho_altium/Designs/B223_BMD-380_carrier_small/Documentation/B223 A.PDF

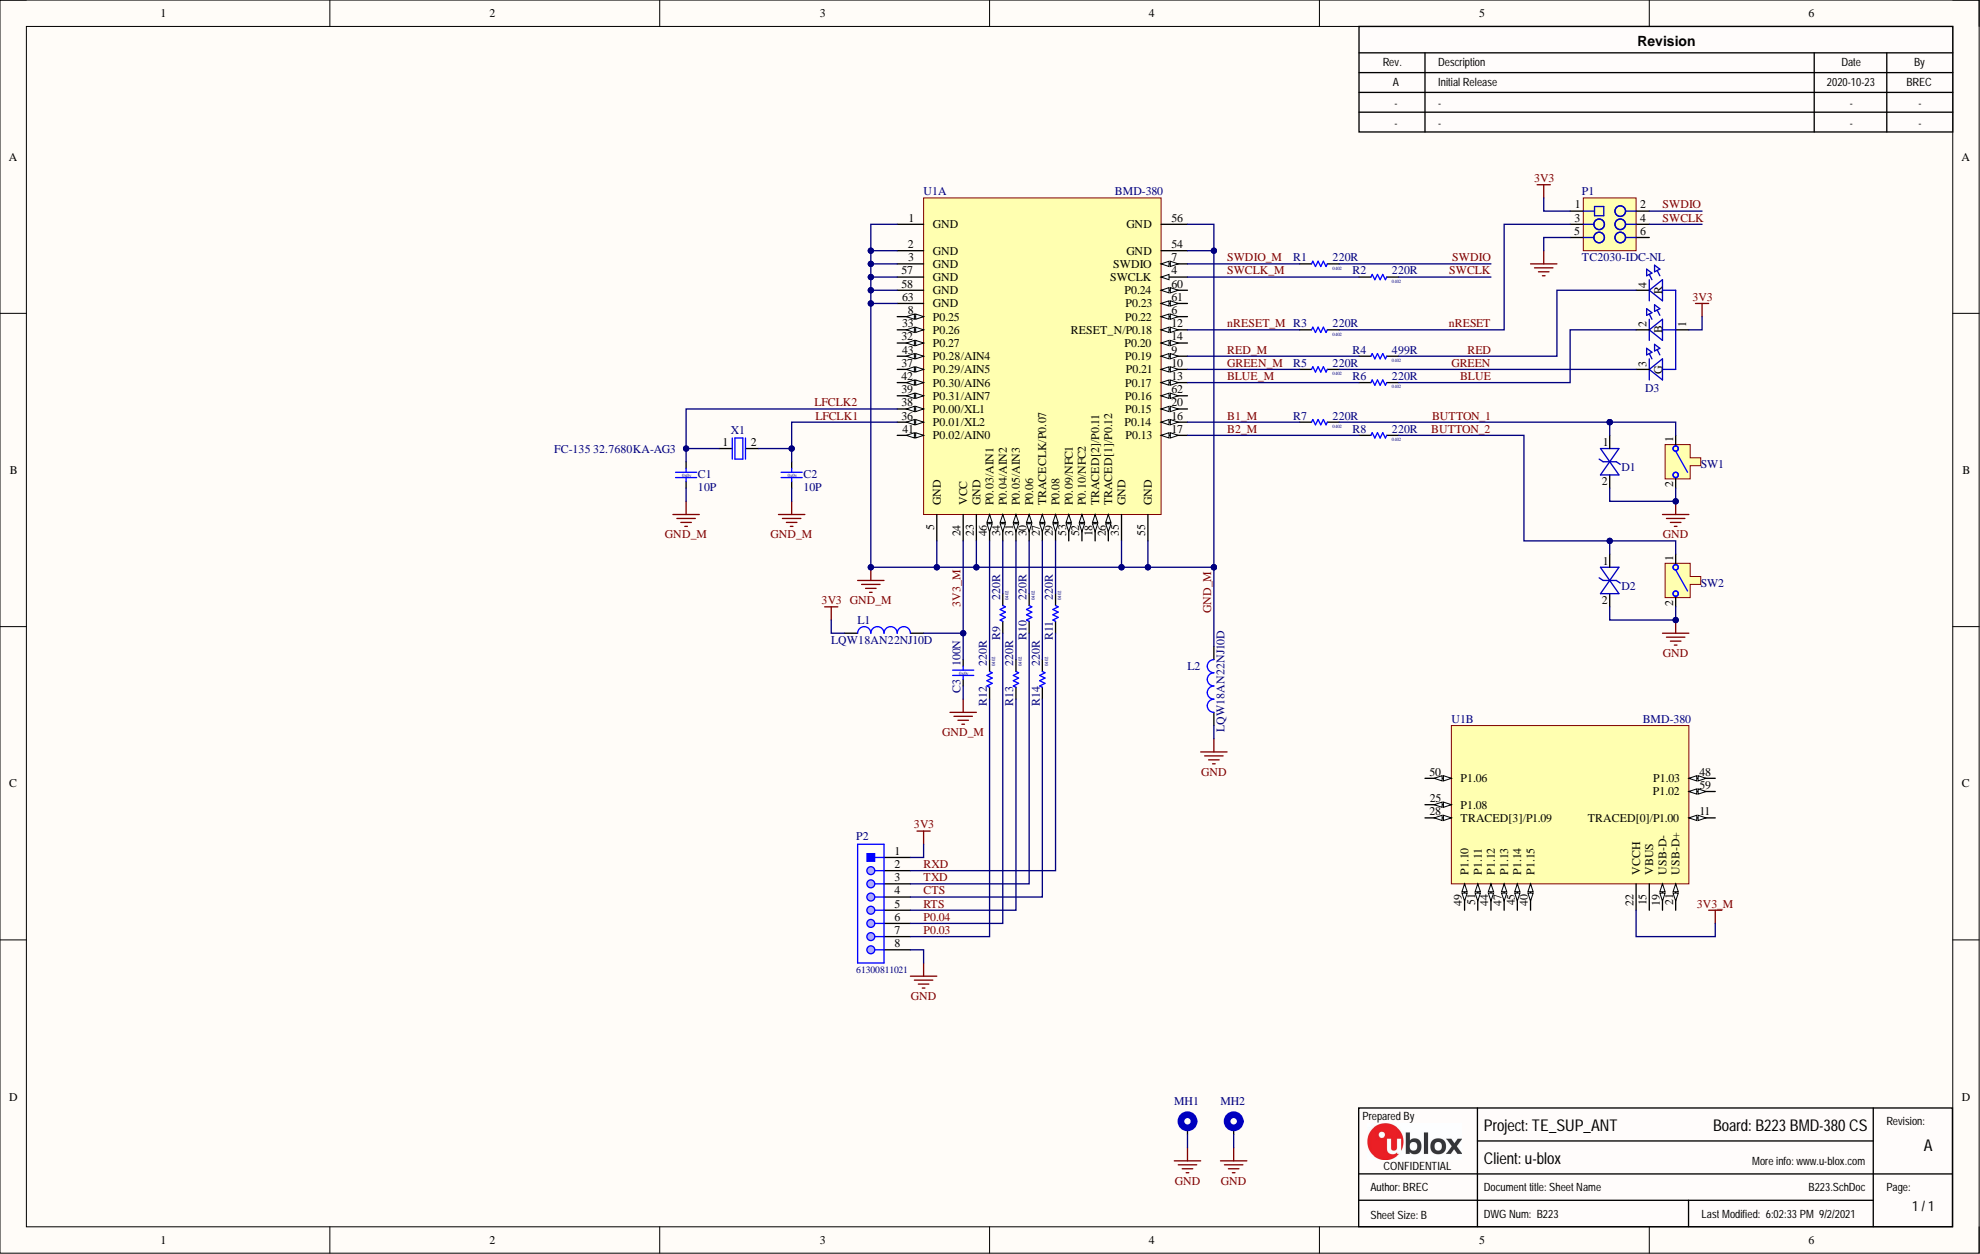
[picture p126: page 1]

Rev. | Description | Date | By
A | Initial Release | 2020-10-23 | BREC

GND_M 3V3 RXD

3 | TXD
4 | CTS
5 | RTS
6 | P0.04
7 | P0.03

More info: www.u-blox.com

Author: BREC | Document title: Sheet Name B223.SchDoc | Page: 1 / 1

Sheet Size: B | DWG Num: B223 | Last Modified: 6:02:33 PM 9/2/2021

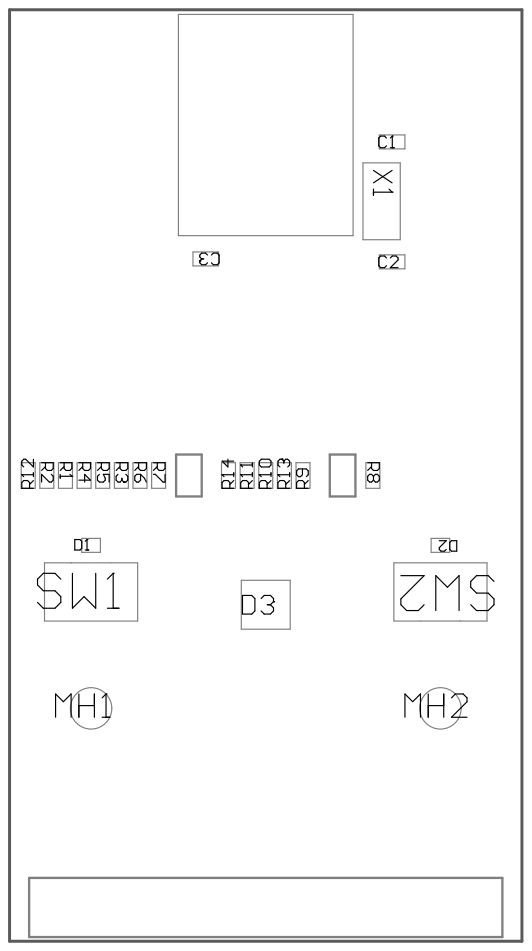
[picture p127: page 2]

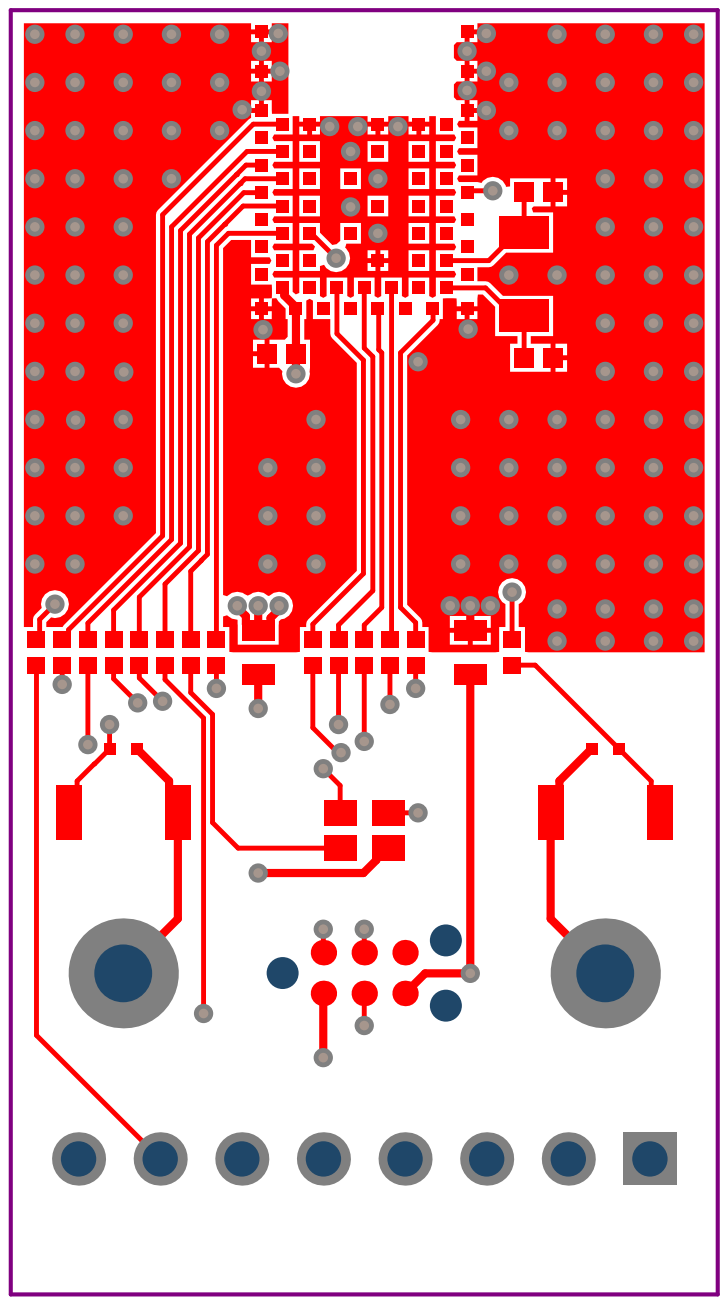
[picture p128: page 4]

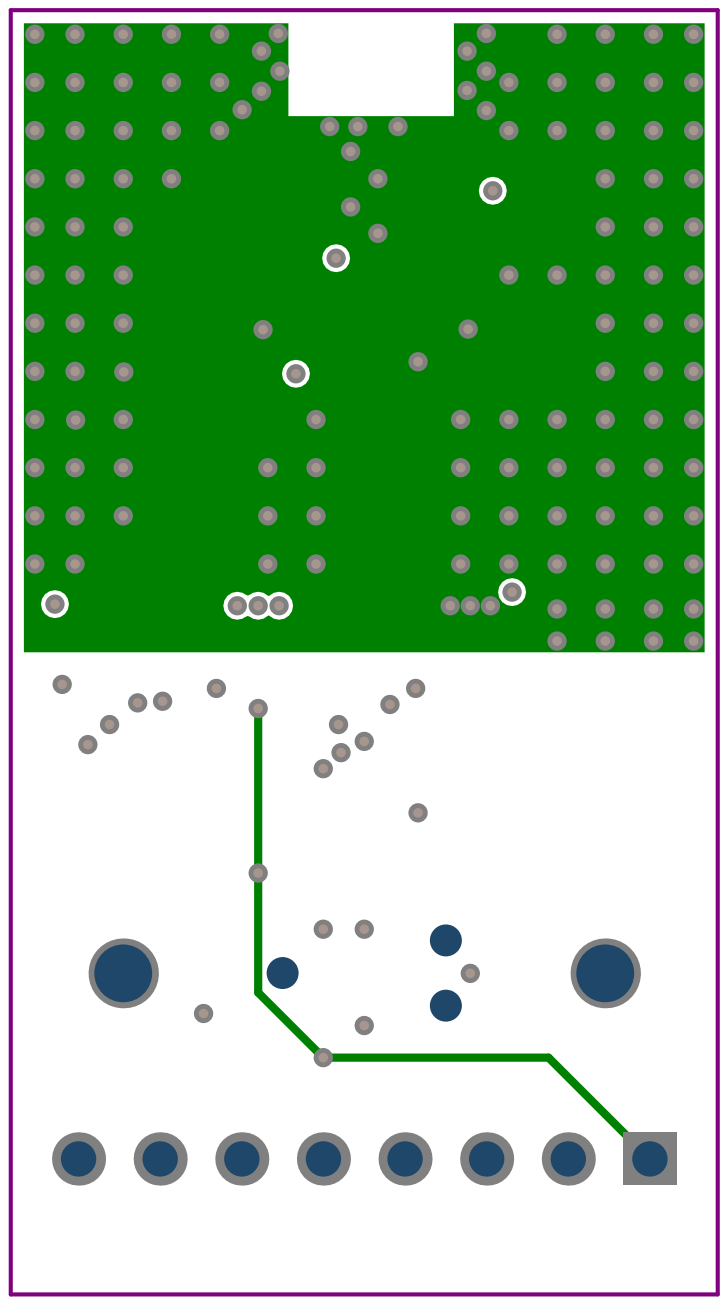
[picture p129: page 5]

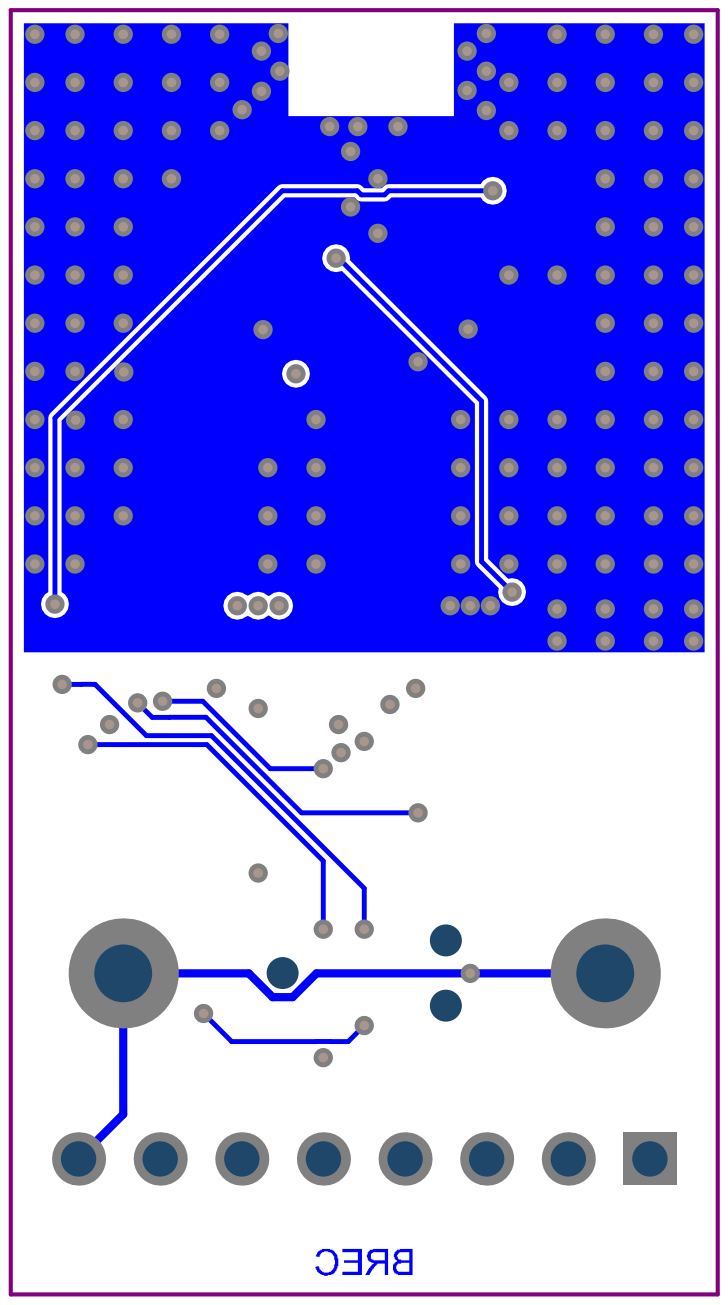
[picture p130: page 7]

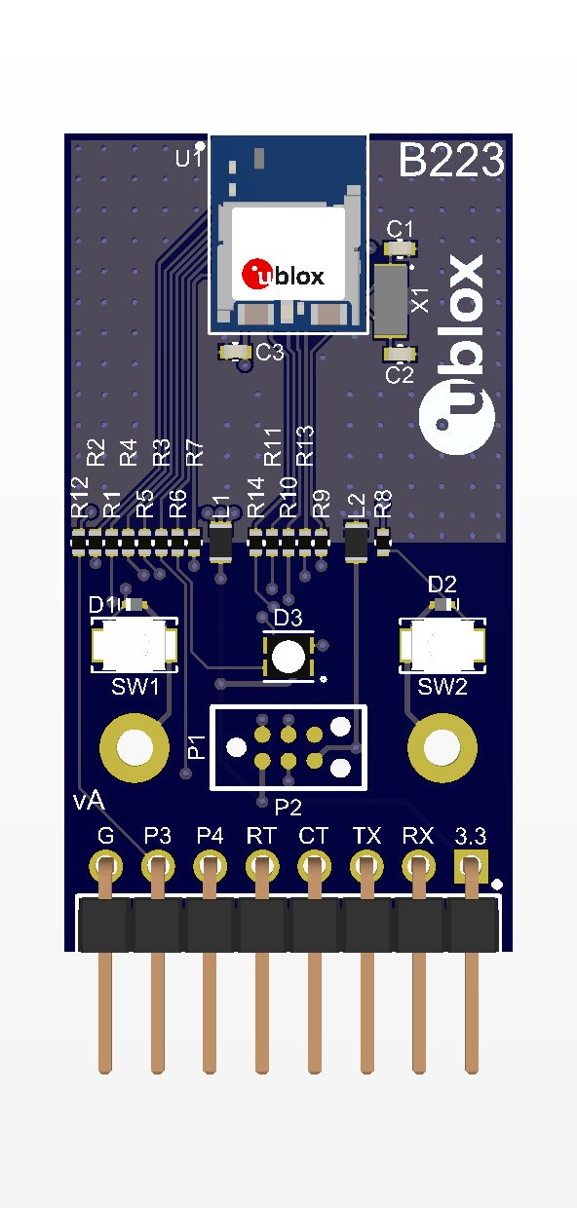
[picture p131: page 8]

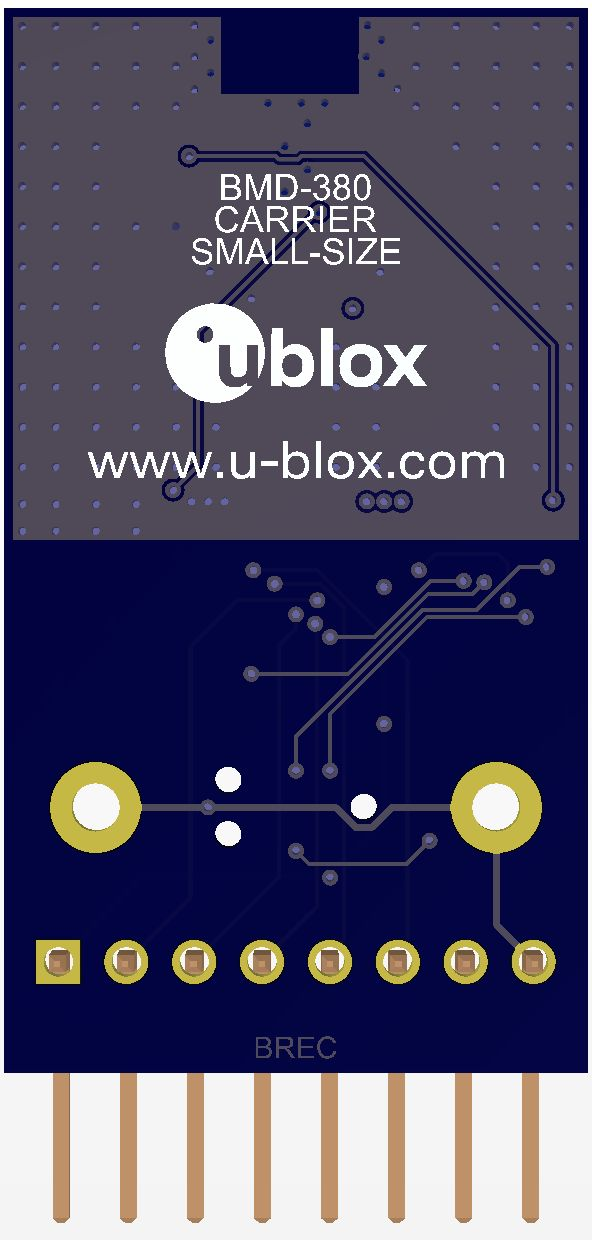
[picture p132: page 9]

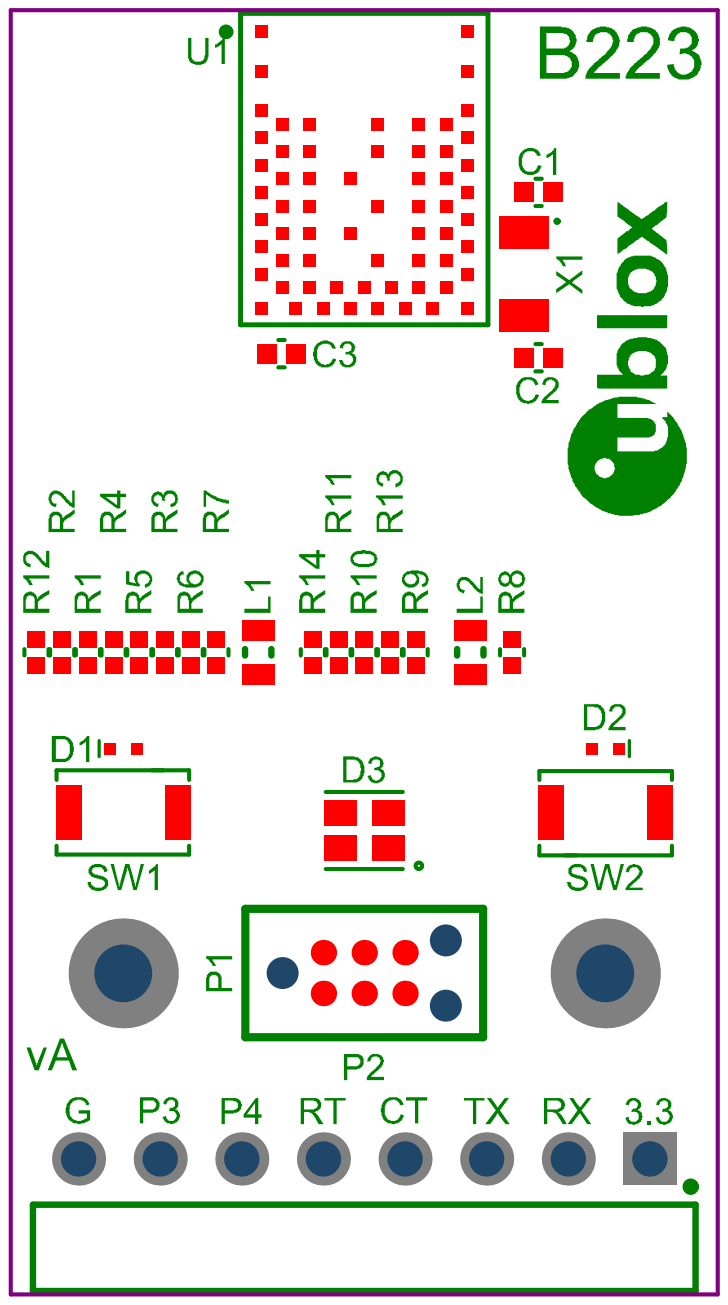
[picture p133: page 11]

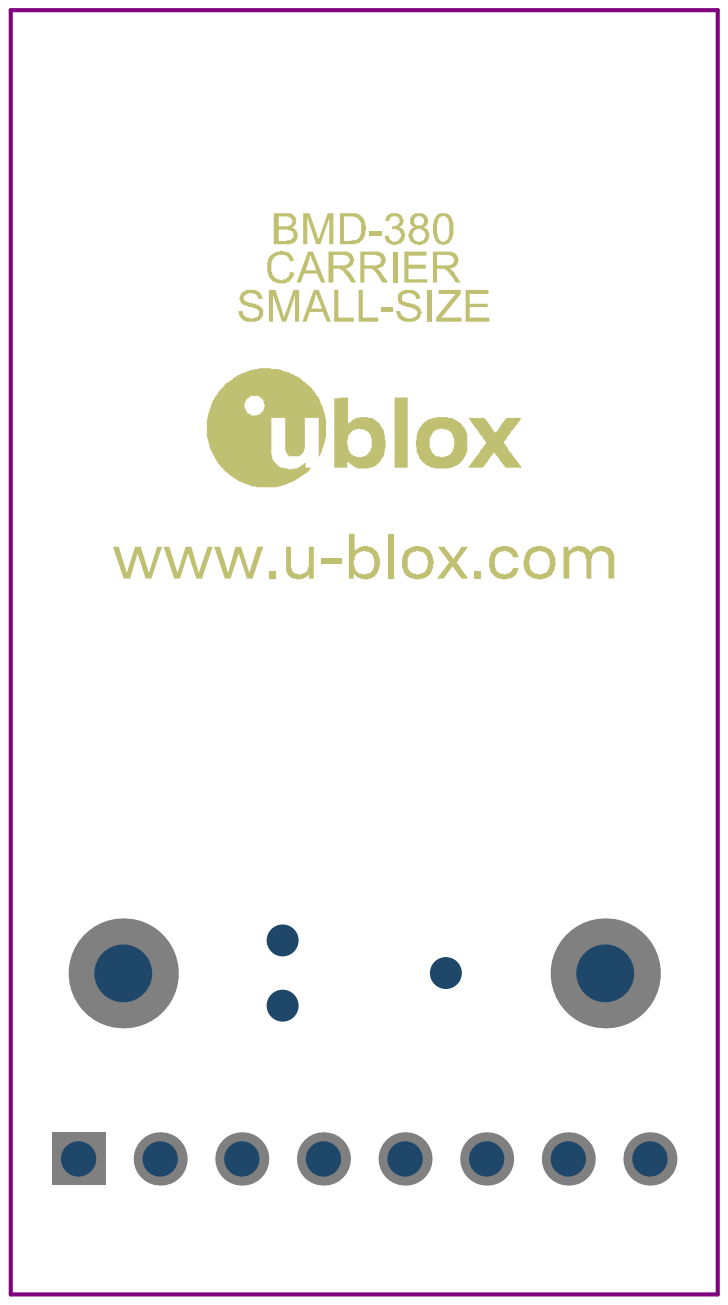
[picture p134: page 12]
