u-blox/blueprints_sho_altium/Designs/B224_NINA-B112_carrier_mid/Documentation/B224 B.PDF

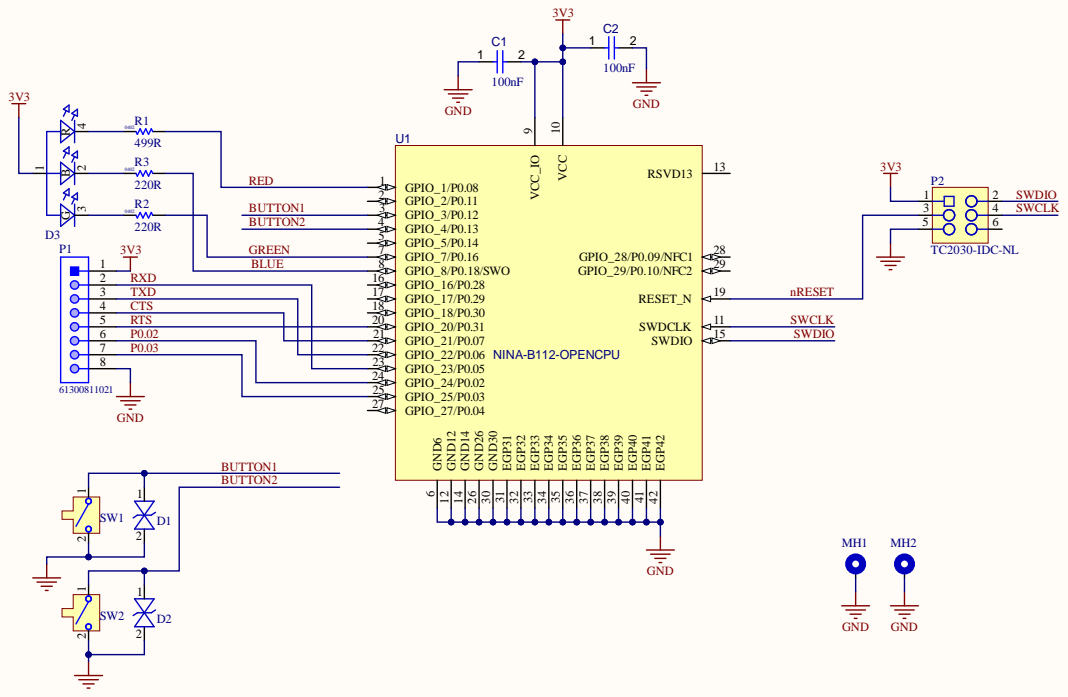
[picture p135: page 1]

Rev. | Description | Date | By
A | Initial Release | 2020-10-23 | LKIS

B | Corrected RTS/CTS | 2021-09-02 | BREC

3 | TXD | GPIO_17/P0.29 17
4 | CTS | GPIO_18/P0.30 18
5 | RTS | GPIO_20/P0.31 20
6 | P0.02 | GPIO_21/P0.07 21
7 | P0.03 | GPIO_23/P0.05 23 GPIO_22/P0.06 22

GPIO_25/P0.03 25 GPIO_24/P0.02 24

More info: www.u-blox.com

Author: LKIS | Document title: Sheet Name B224.SchDoc | Page: 1 / 1

Sheet Size: B | DWG Num: B224 | Last Modified: 1:59:05 PM 9/2/2021

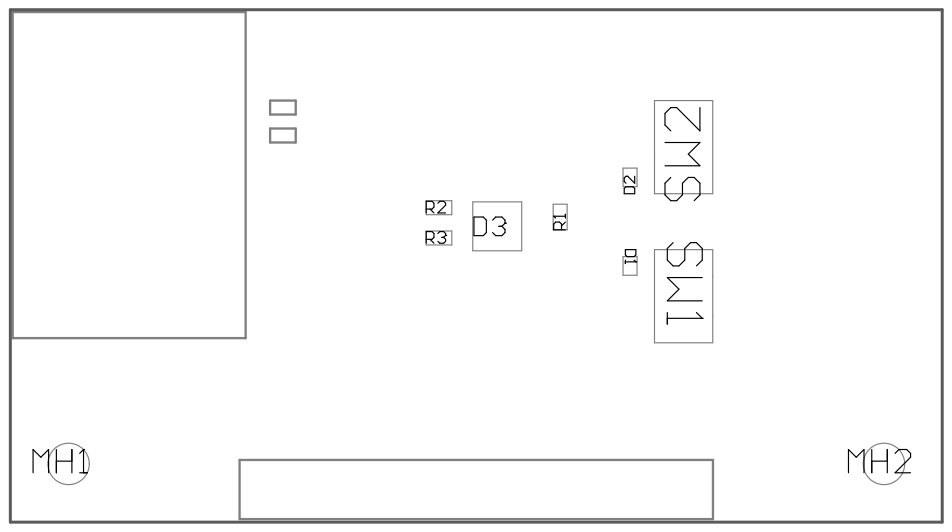
[picture p136: page 2]

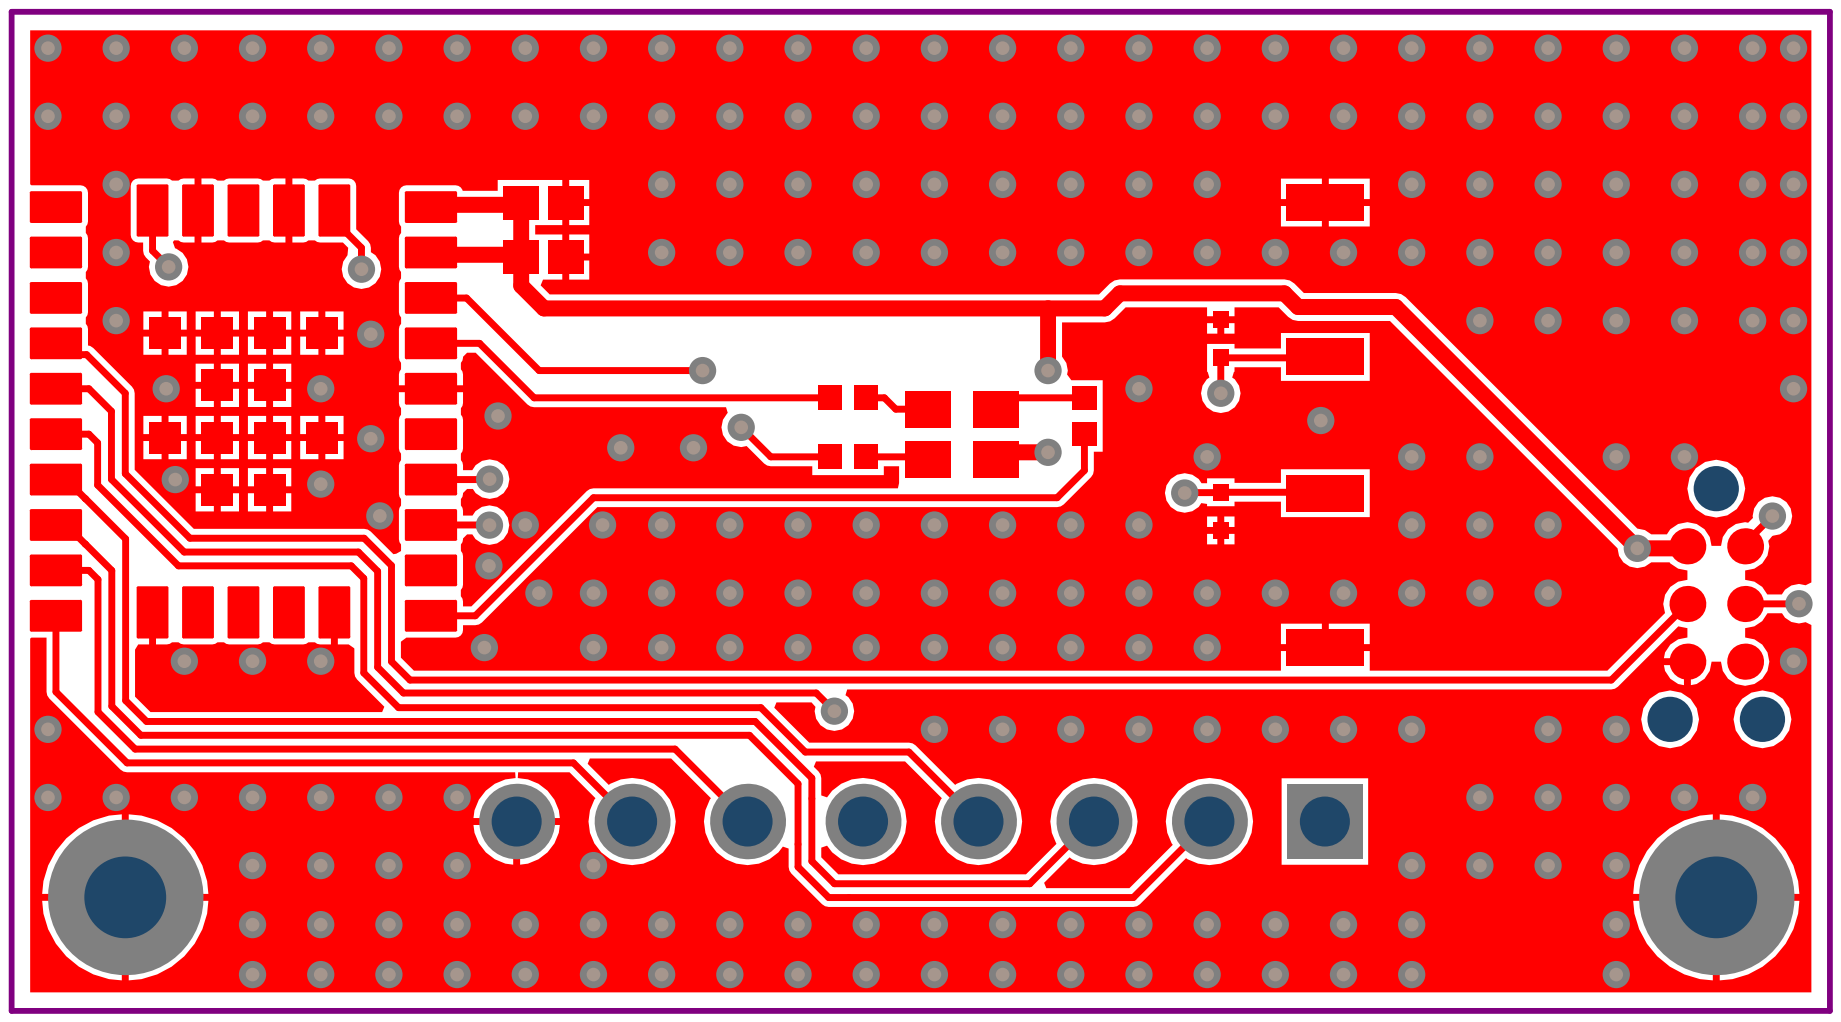
[picture p137: page 4]

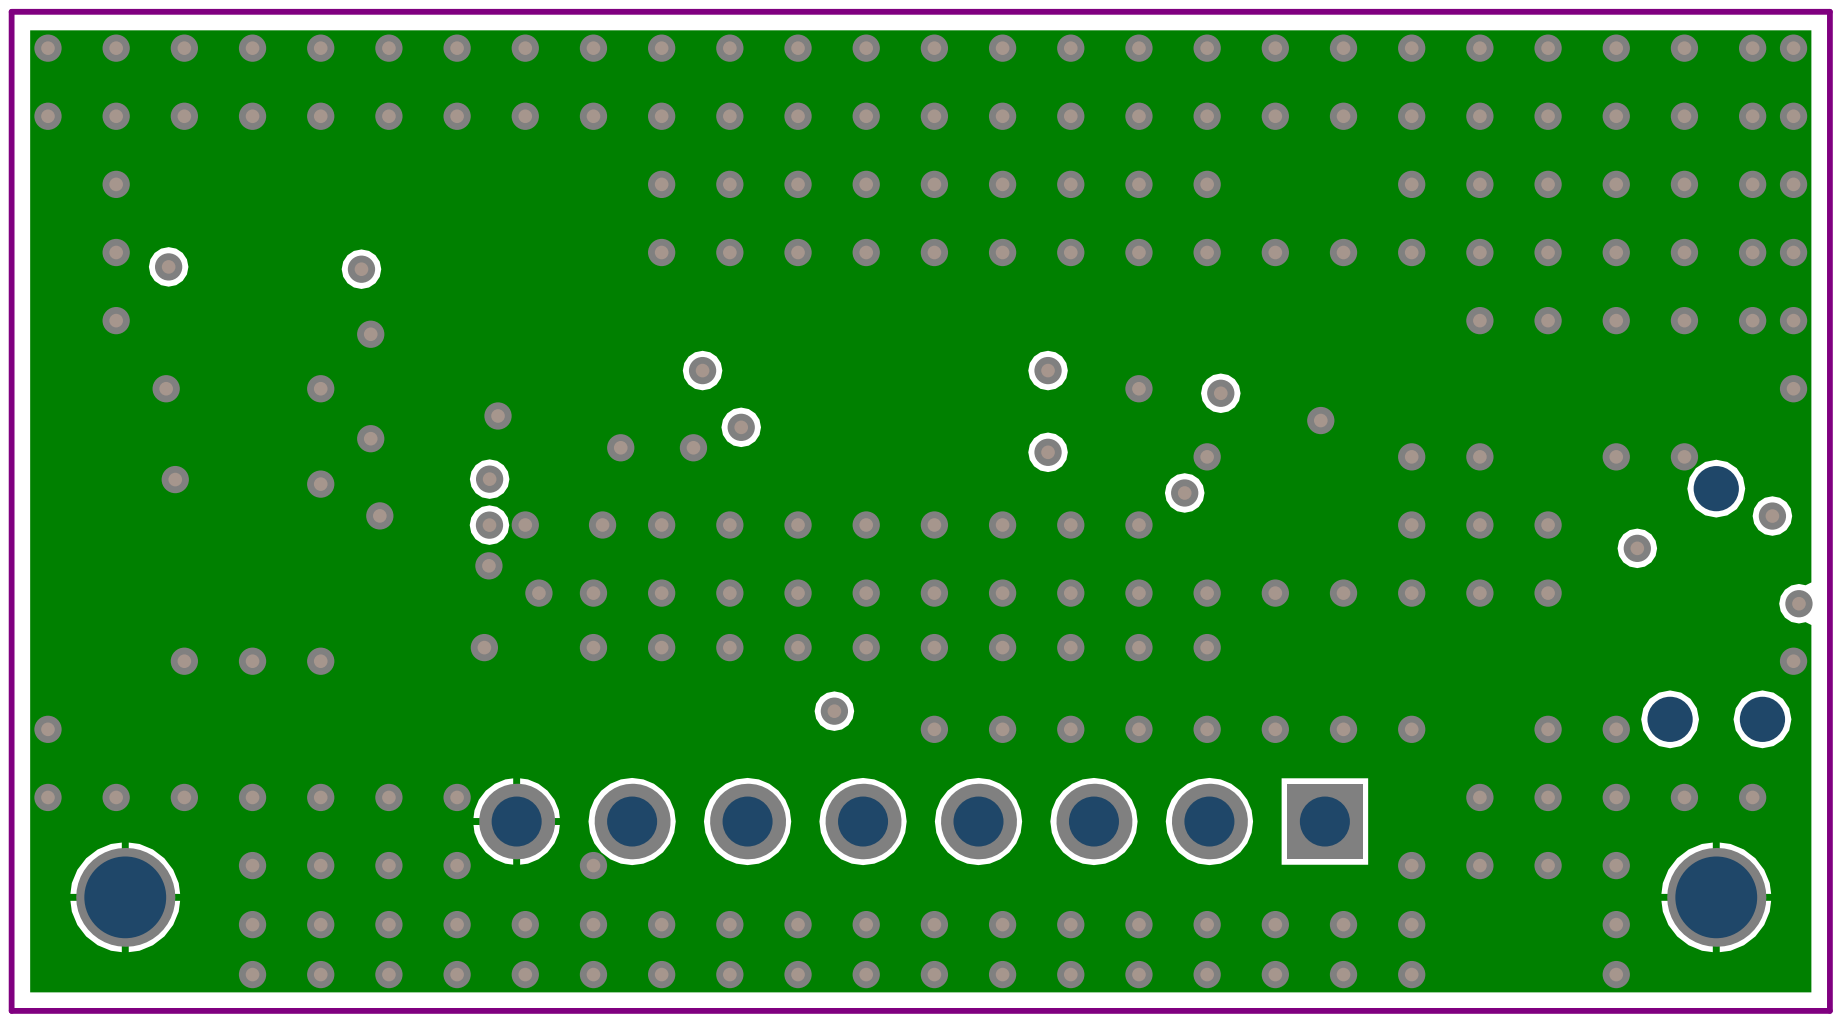
[picture p138: page 5]

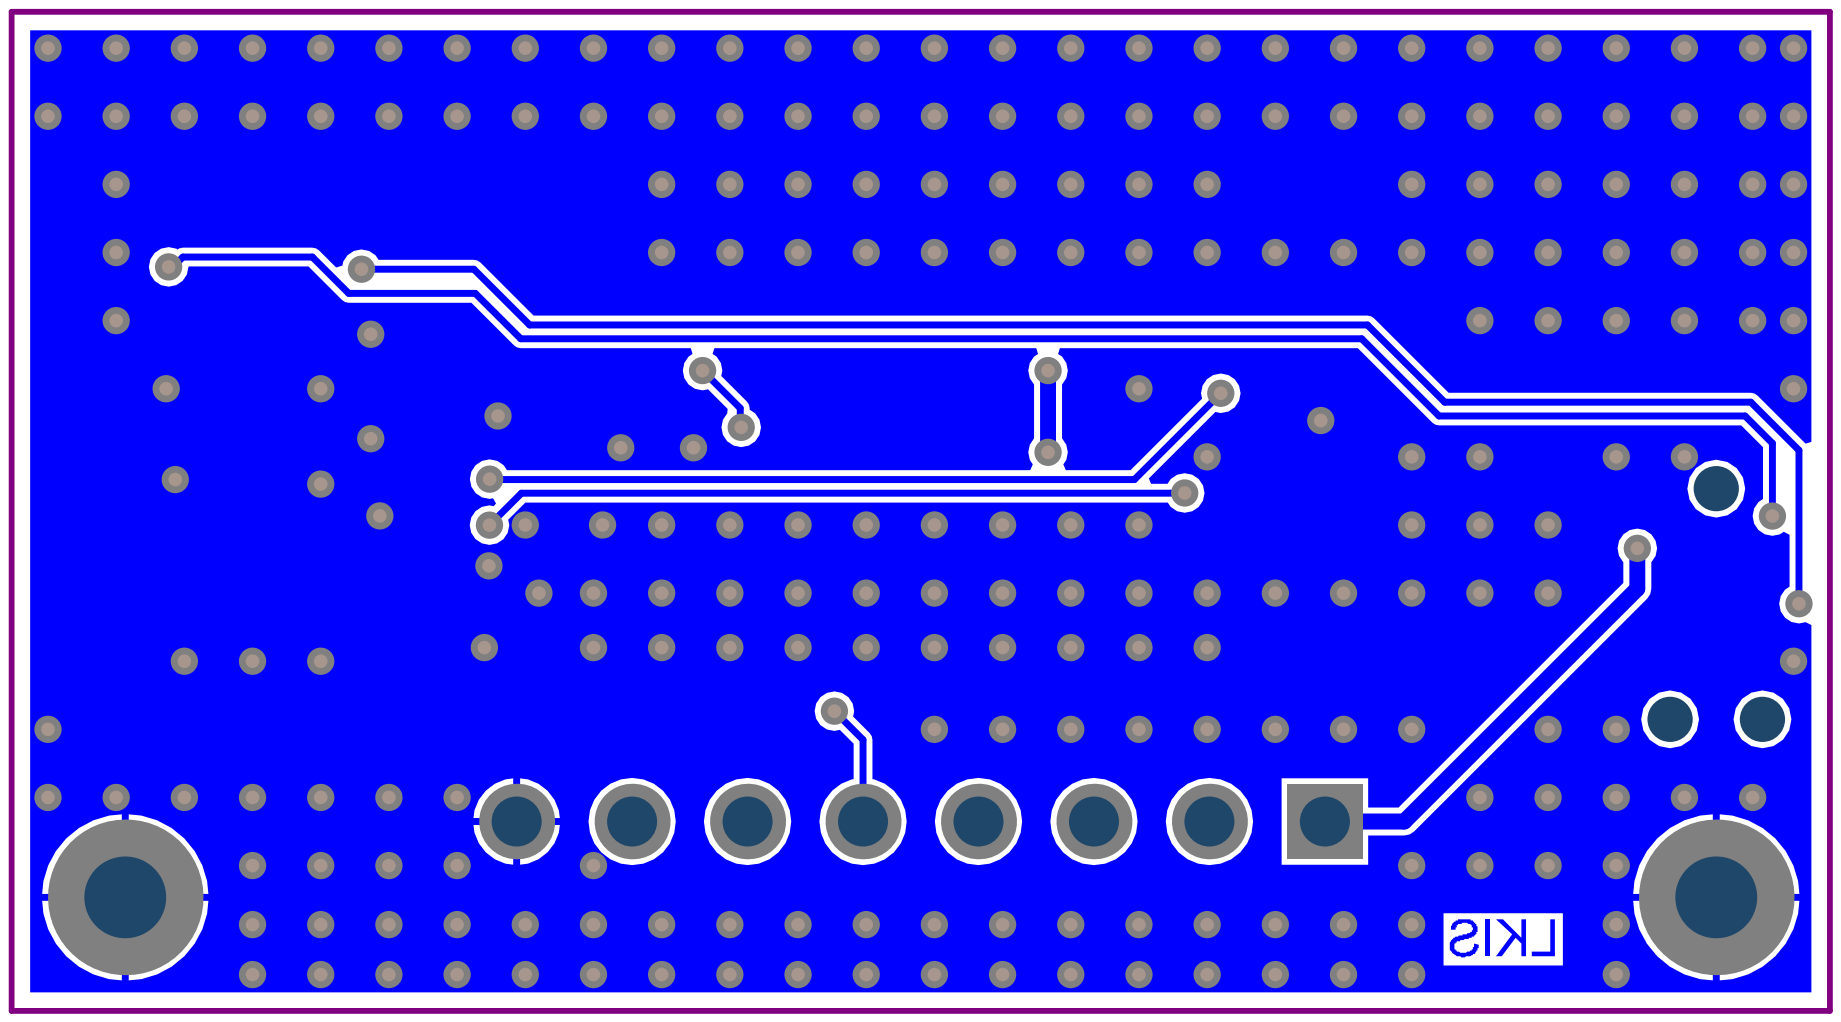
[picture p139: page 7]

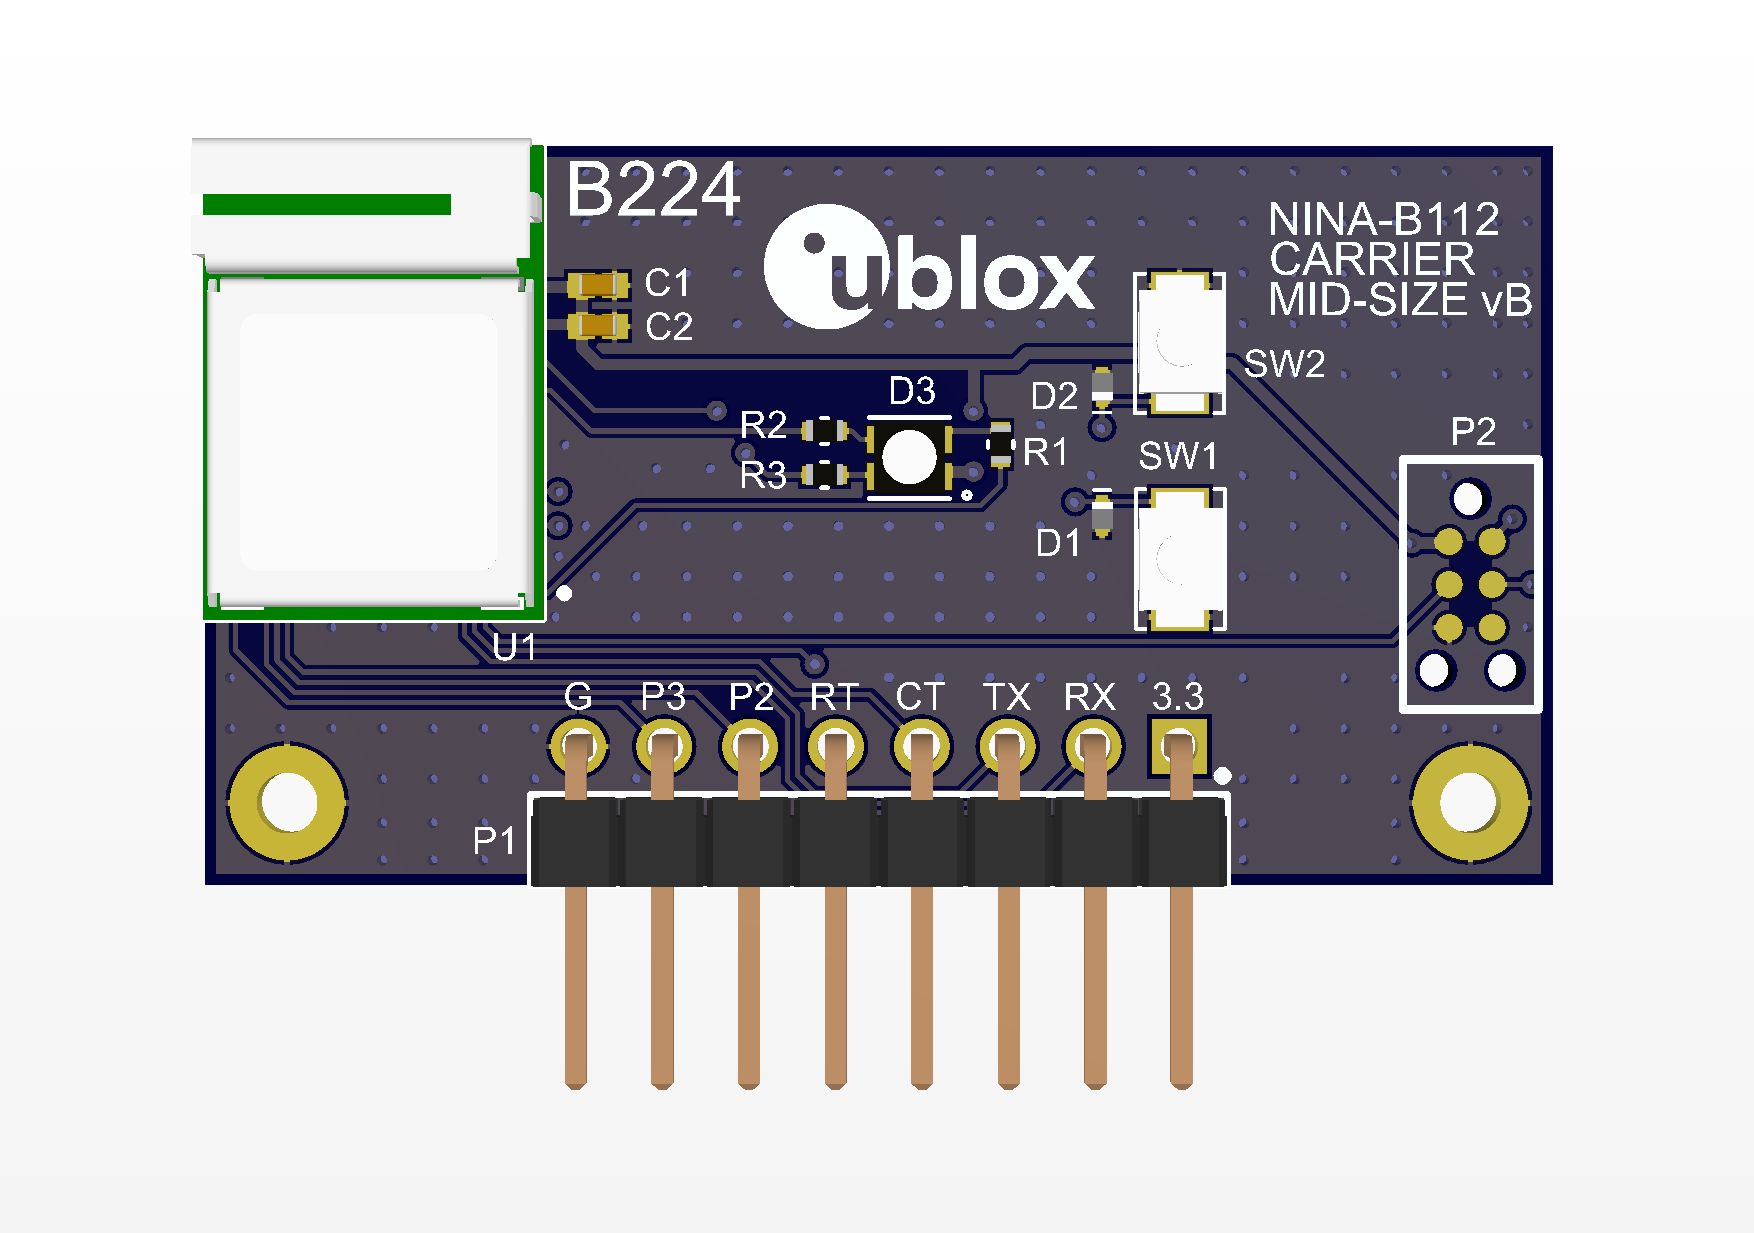
[picture p140: page 8]

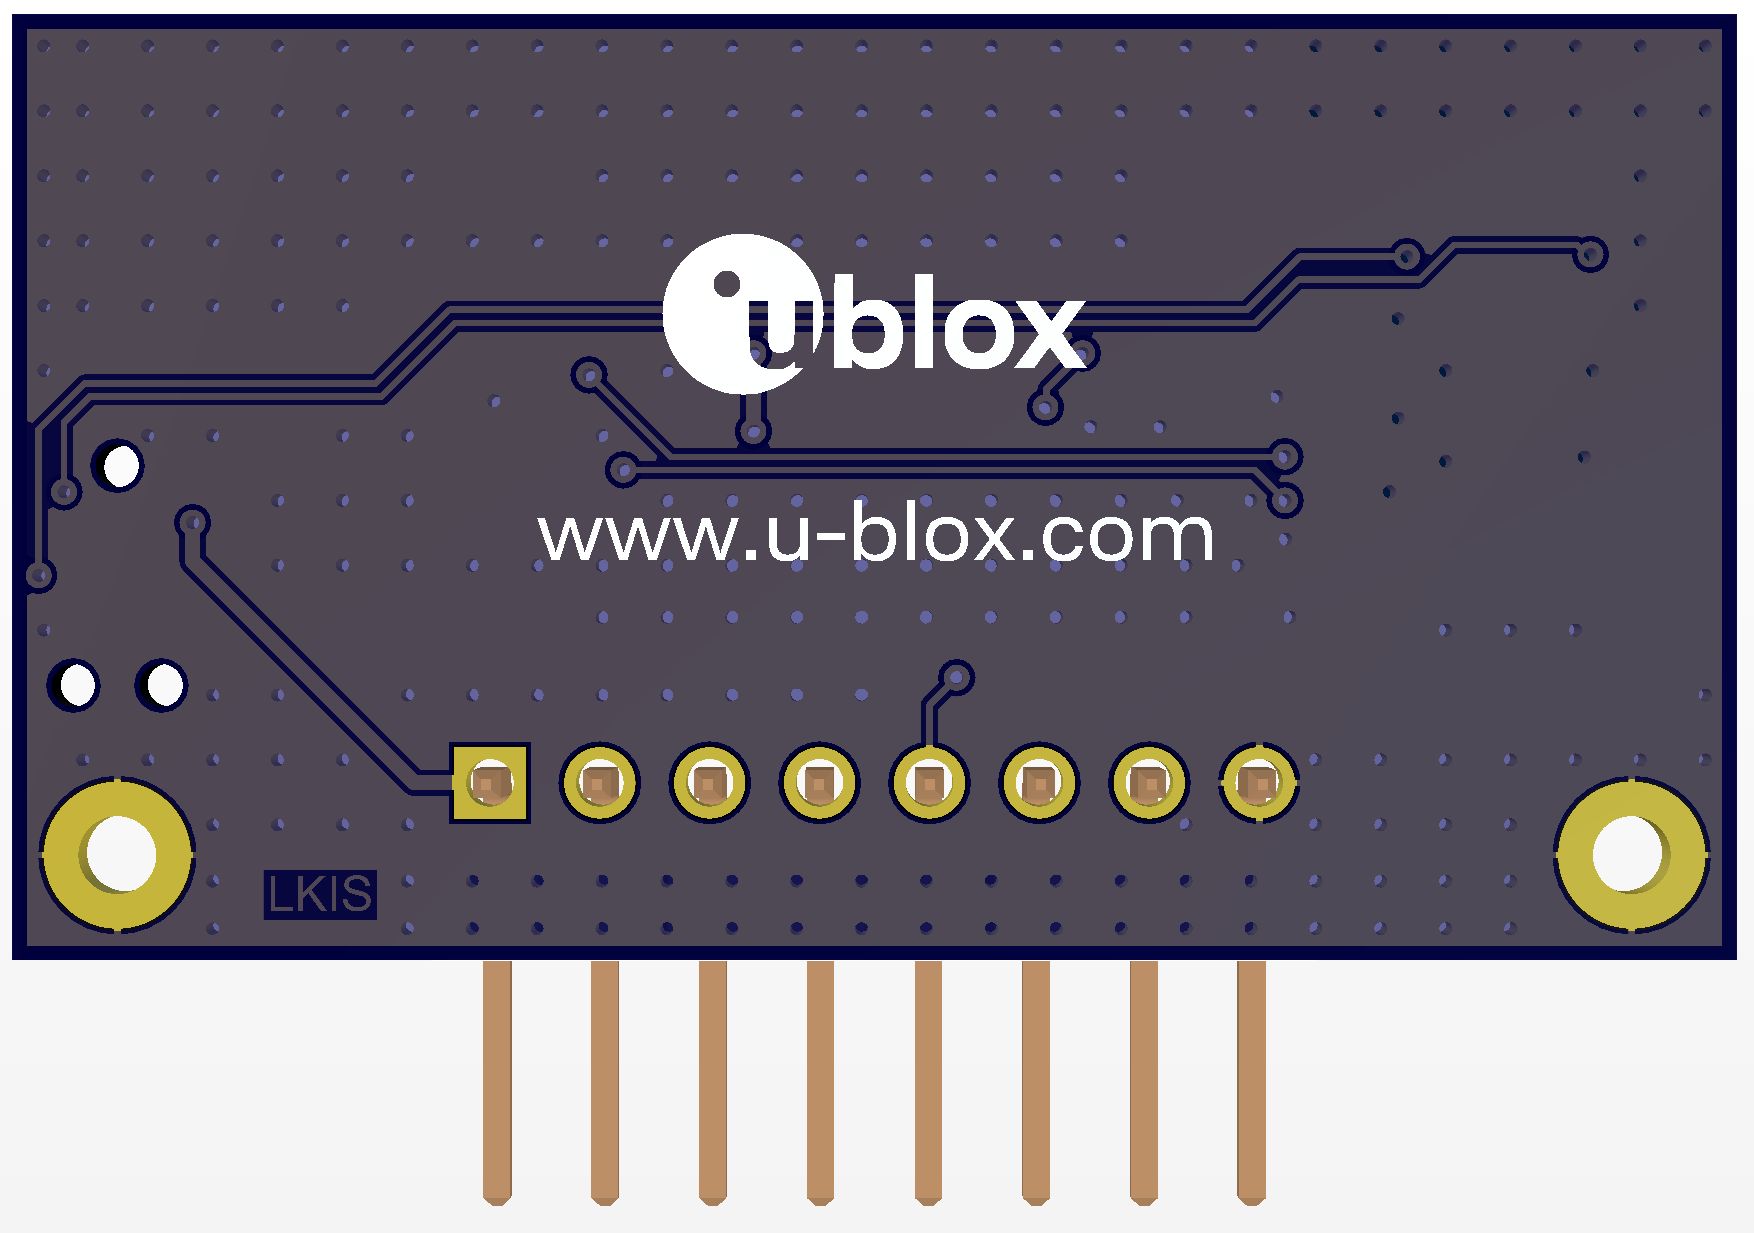
[picture p141: page 9]

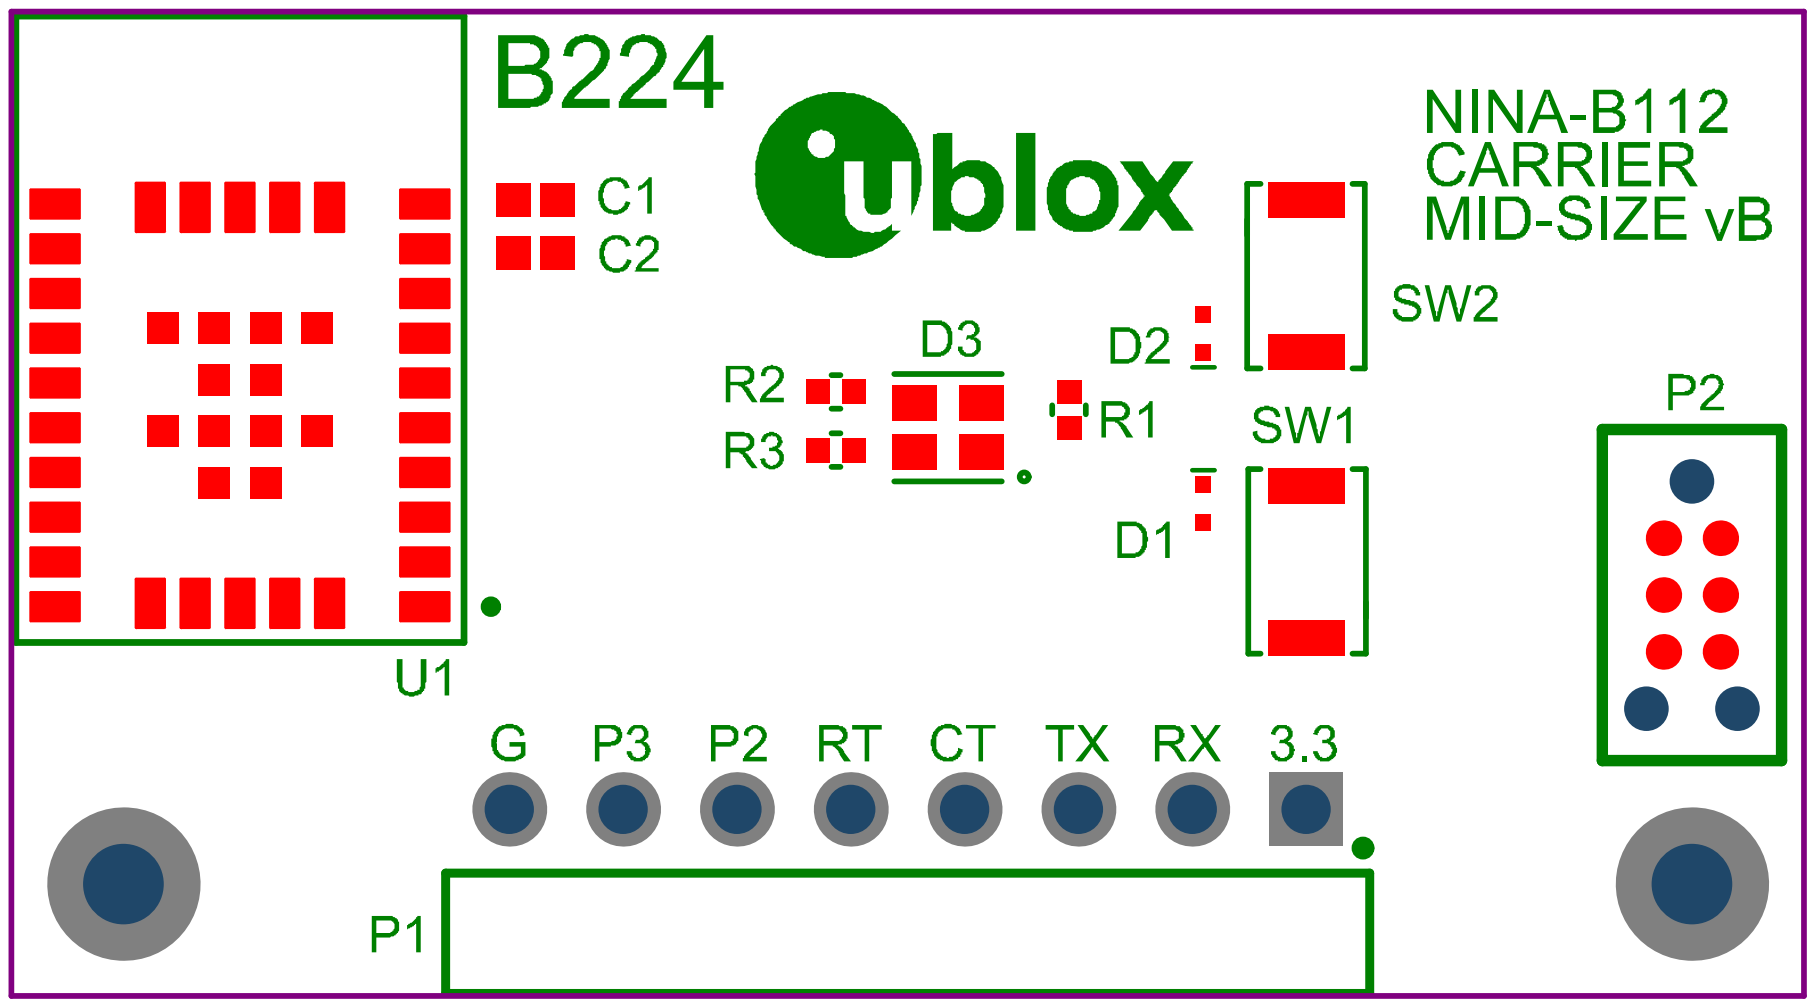
[picture p142: page 11]

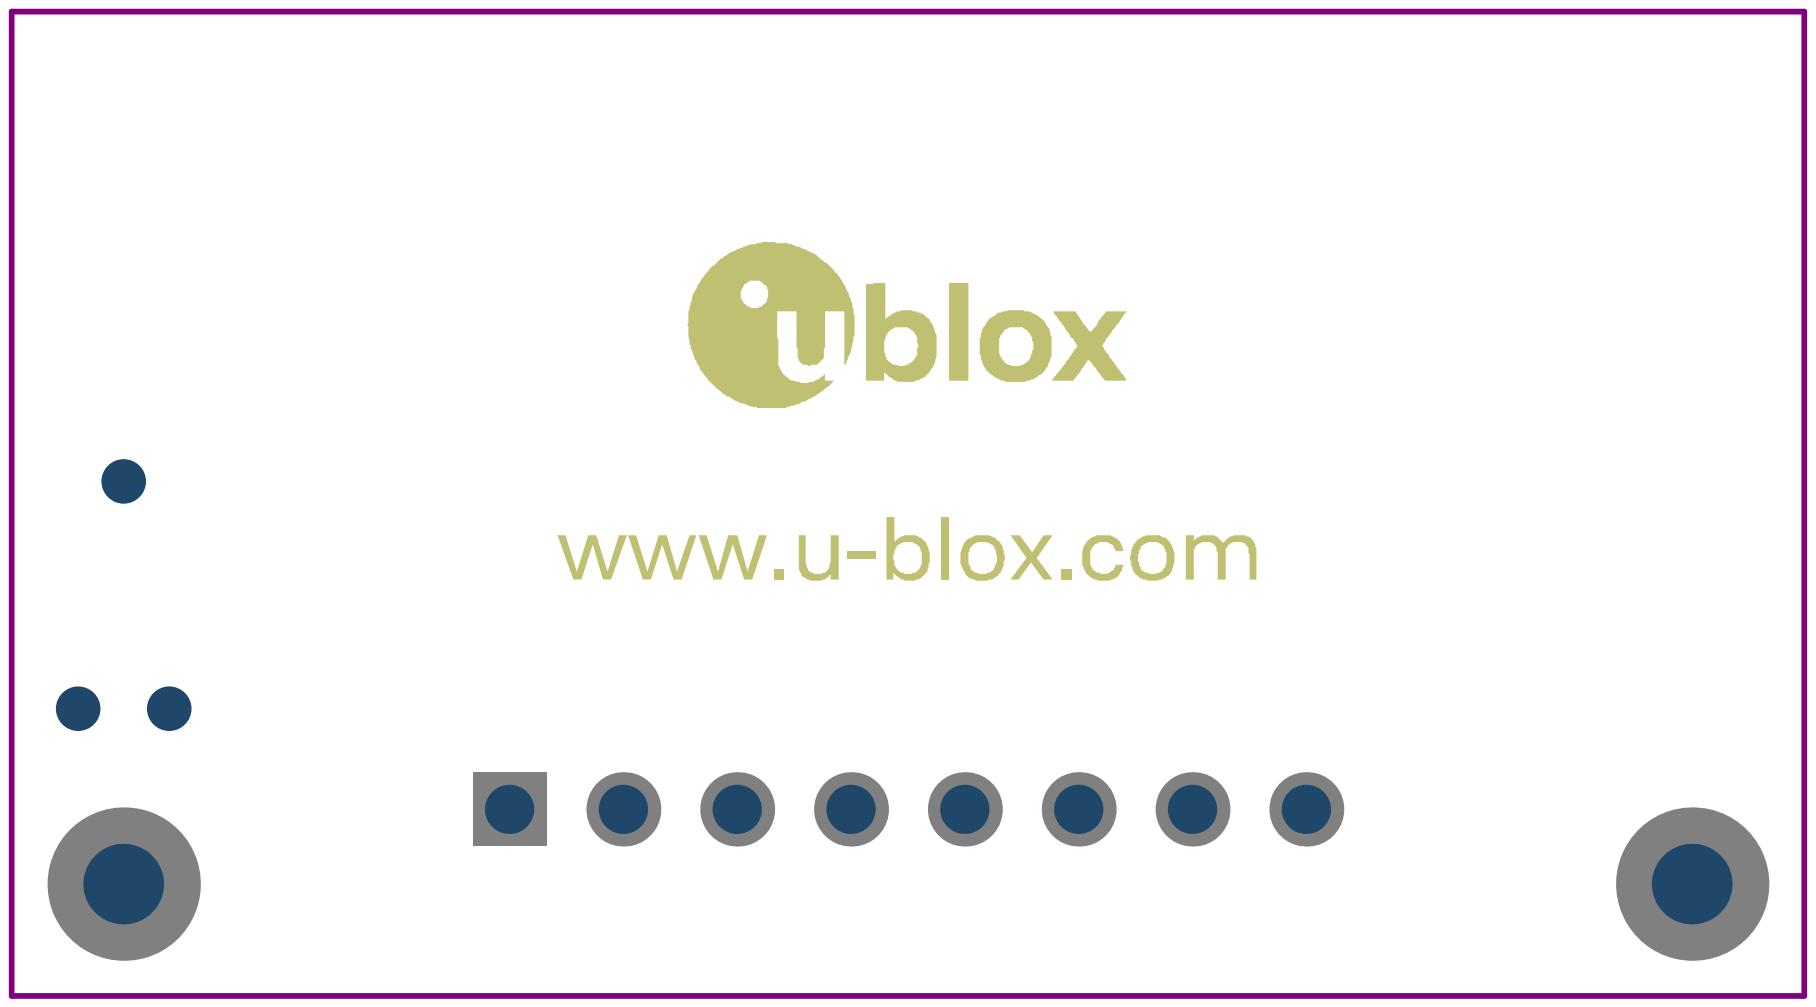
[picture p143: page 12]
