u-blox/blueprints_sho_altium/Designs/B225_NINA-B112_carrier_small/Documentation/B225 B.PDF

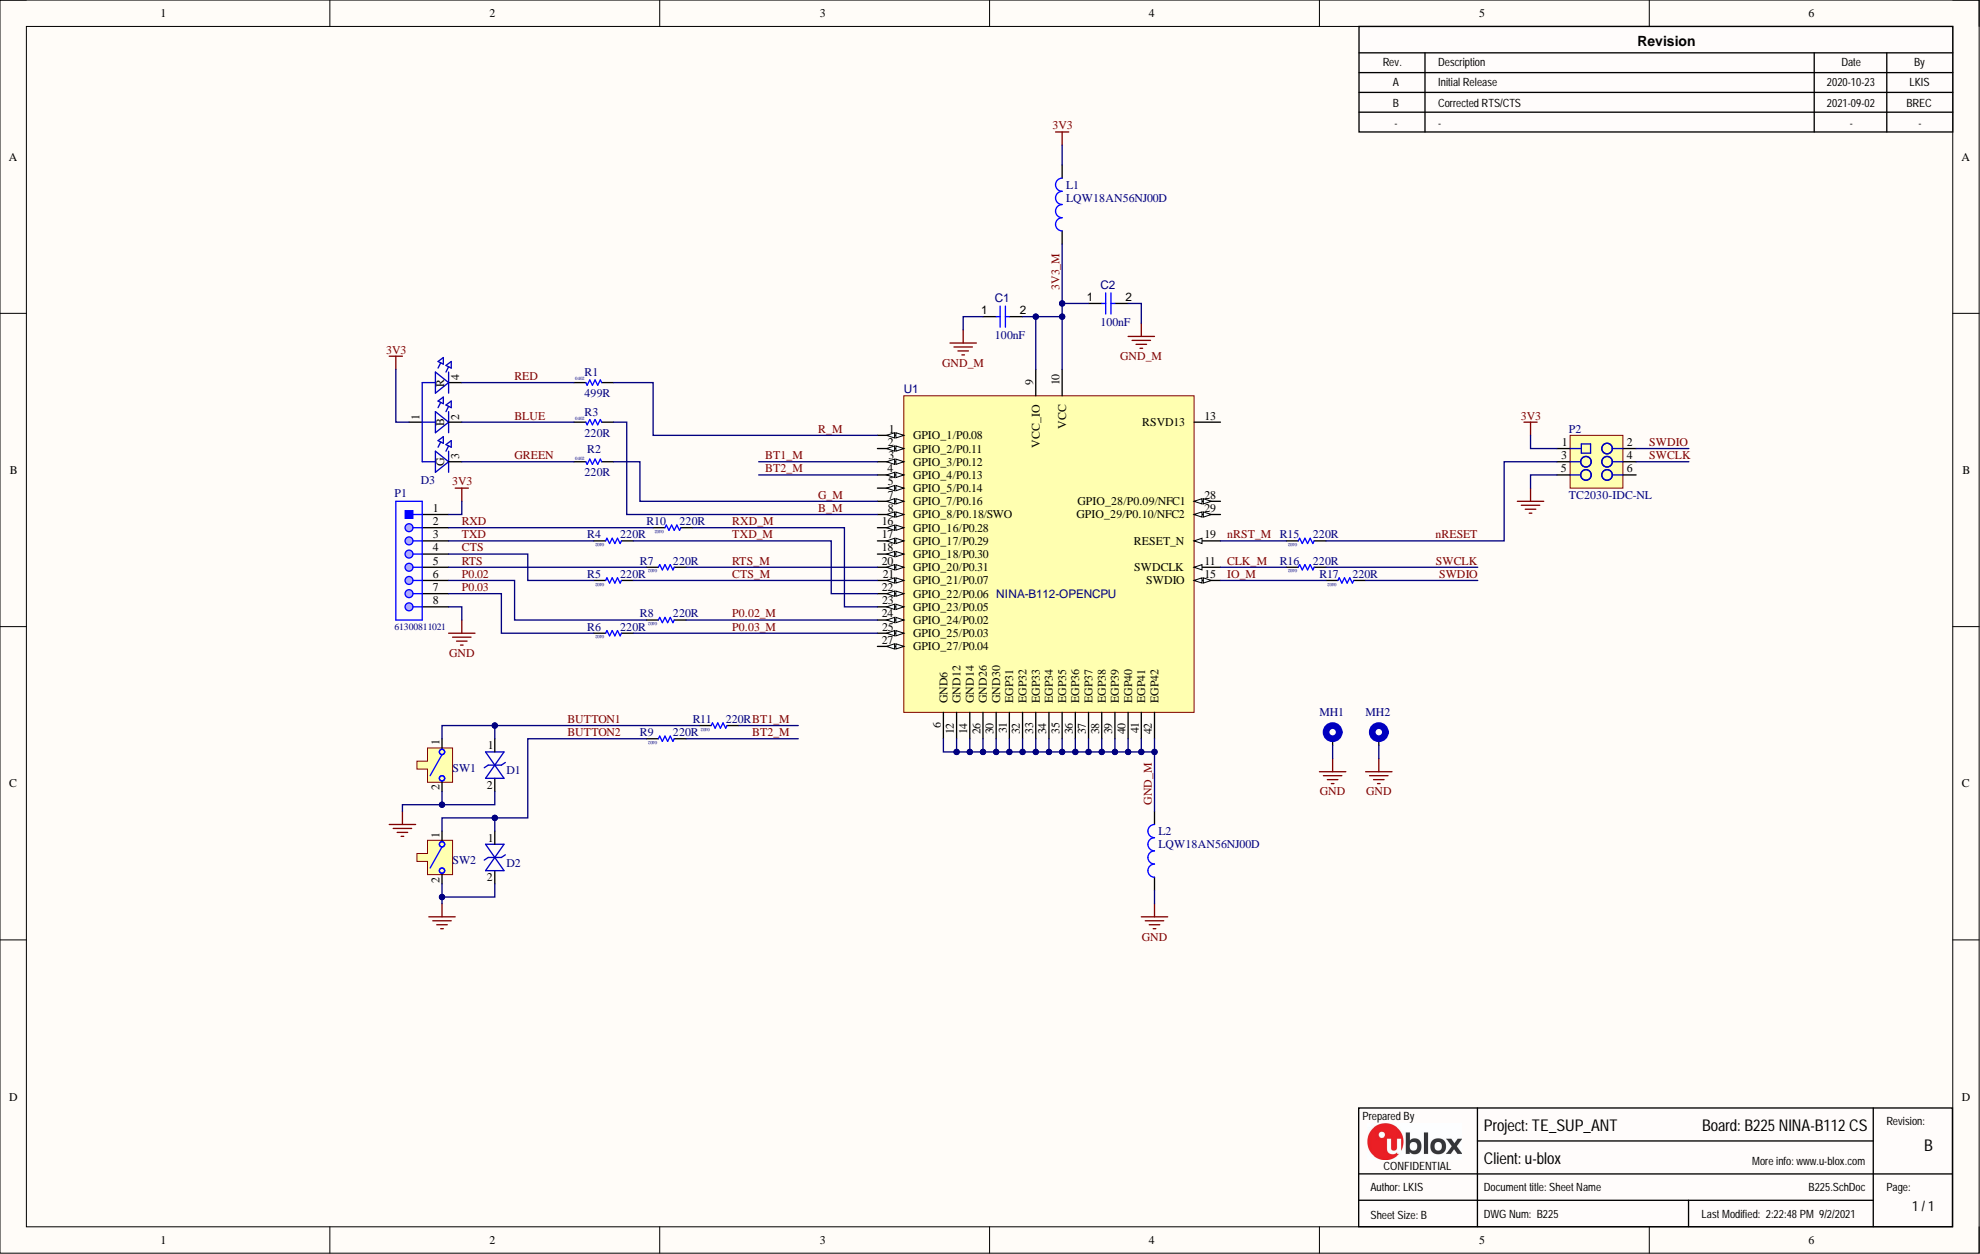
[picture p144: page 1]

Rev. | Description | Date | By
A | Initial Release | 2020-10-23 | LKIS

B | Corrected RTS/CTS | 2021-09-02 | BREC

6 | P0.02 R5 | 220R 2040
7 | P0.03 | | GPIO_23/P0.05 23 GPIO_22/P0.06 22

More info: www.u-blox.com

Author: LKIS | Document title: Sheet Name B225.SchDoc | Page: 1 / 1

Sheet Size: B | DWG Num: B225 | Last Modified: 2:22:48 PM 9/2/2021

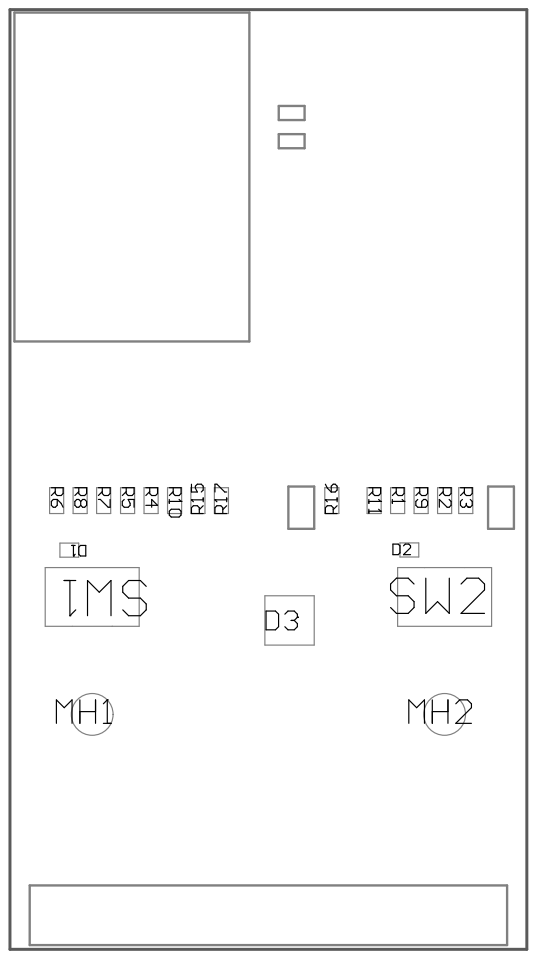
[picture p145: page 2]

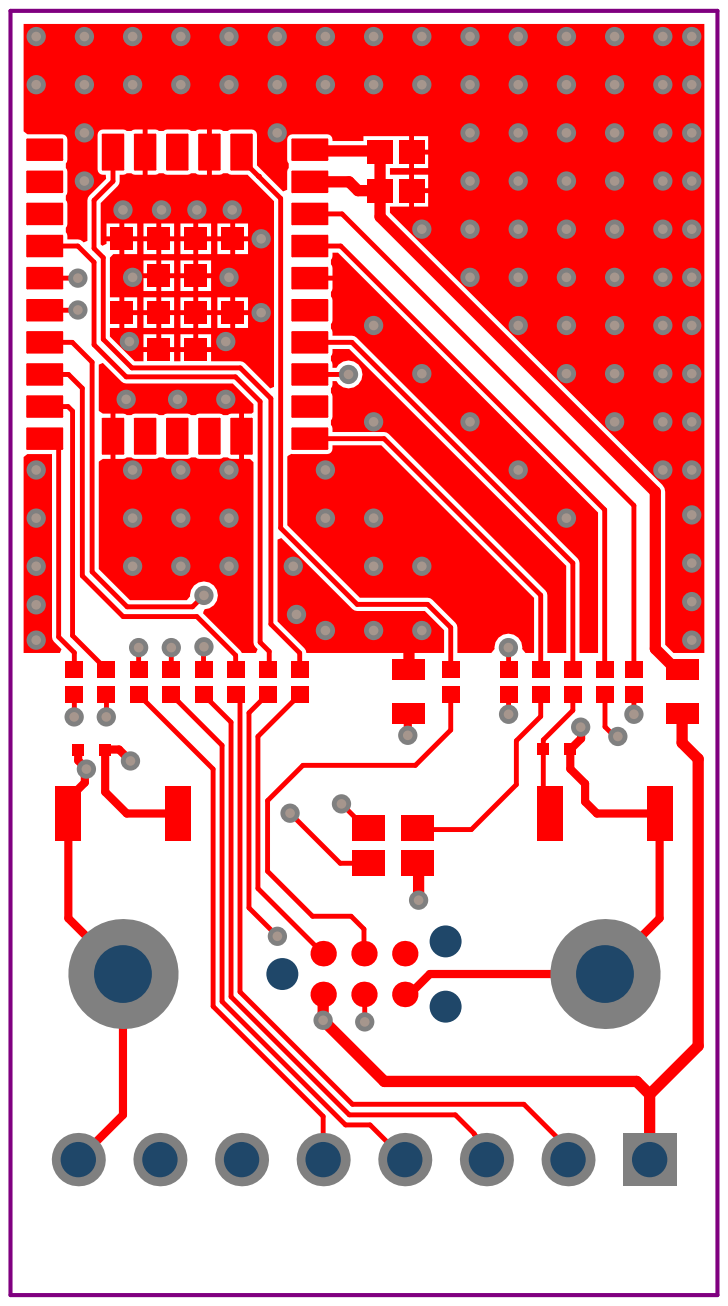
[picture p146: page 4]

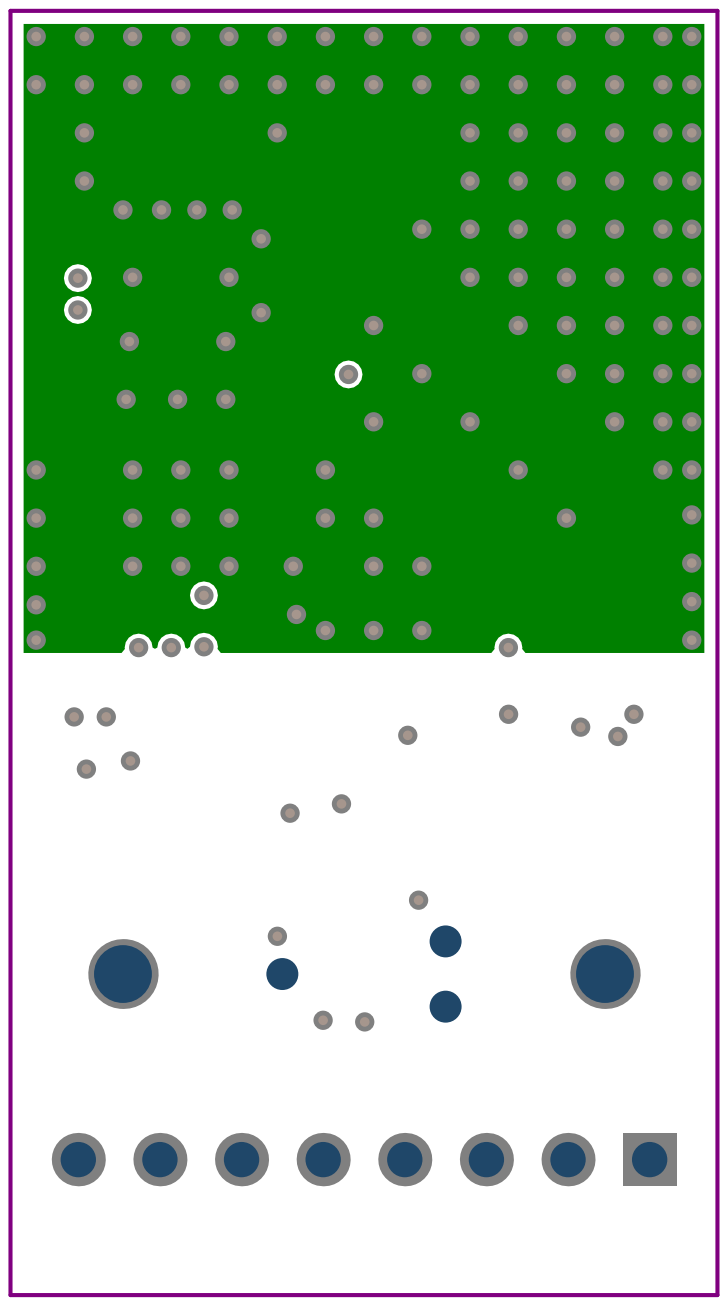
[picture p147: page 5]

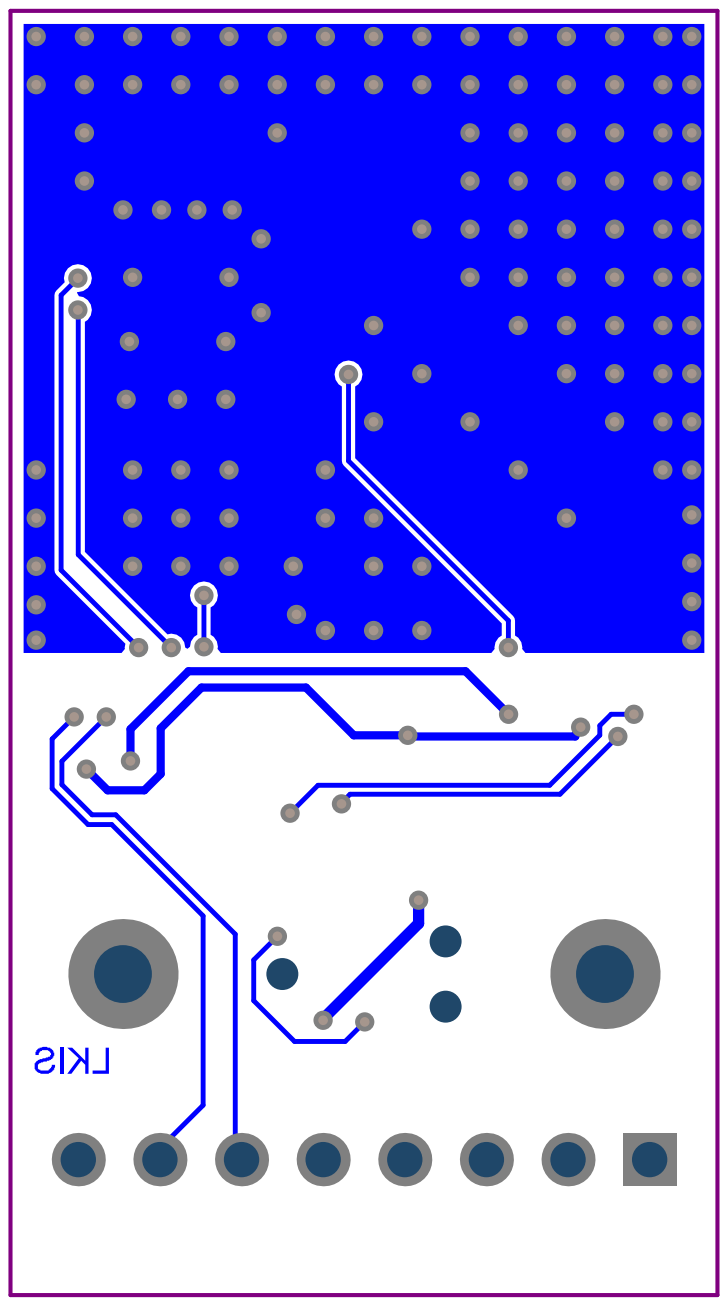
[picture p148: page 7]

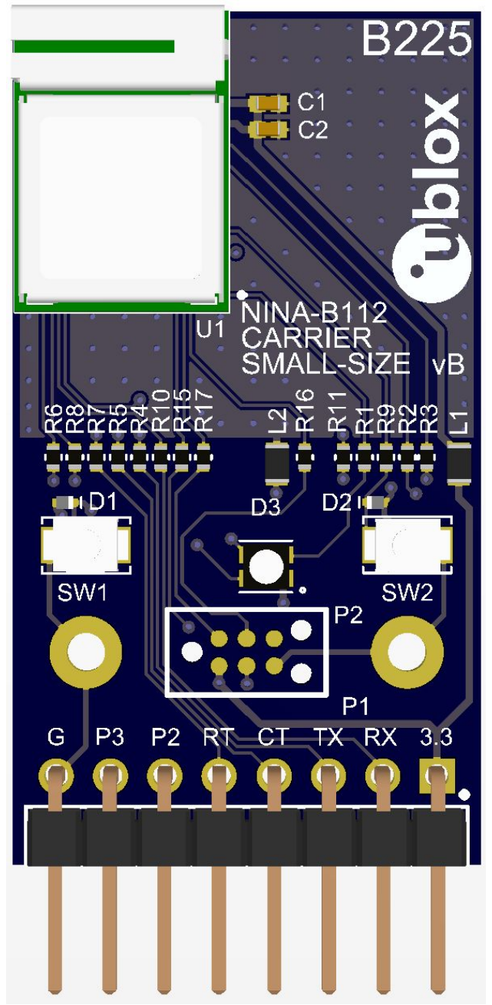
[picture p149: page 8]

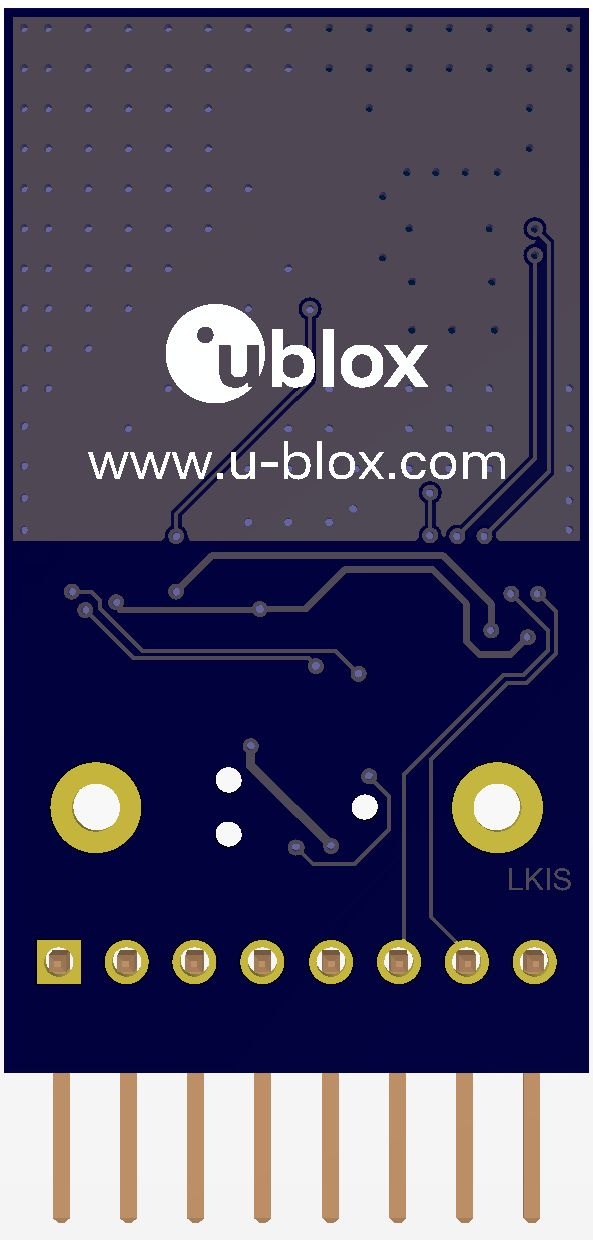
[picture p150: page 9]

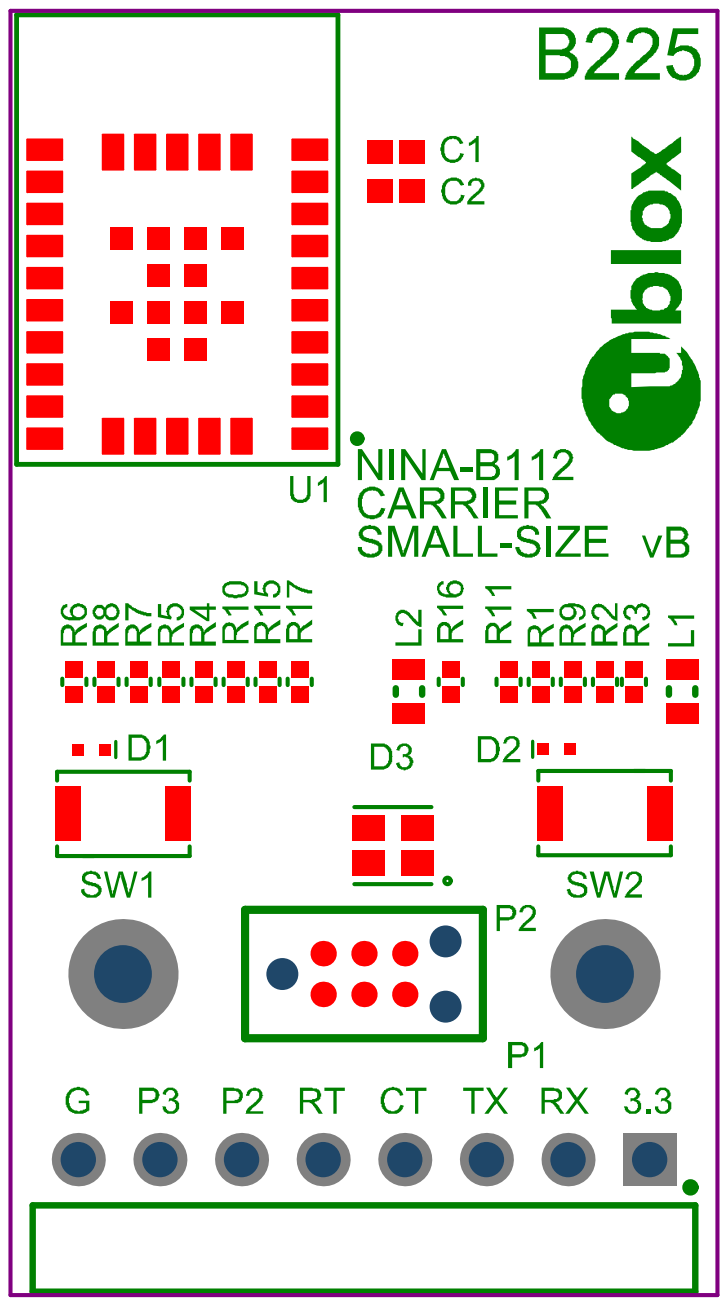
[picture p151: page 11]
