u-blox/blueprints_sho_altium/Designs/B227_NINA-B302_carrier_small/Documentation/B227 B.PDF

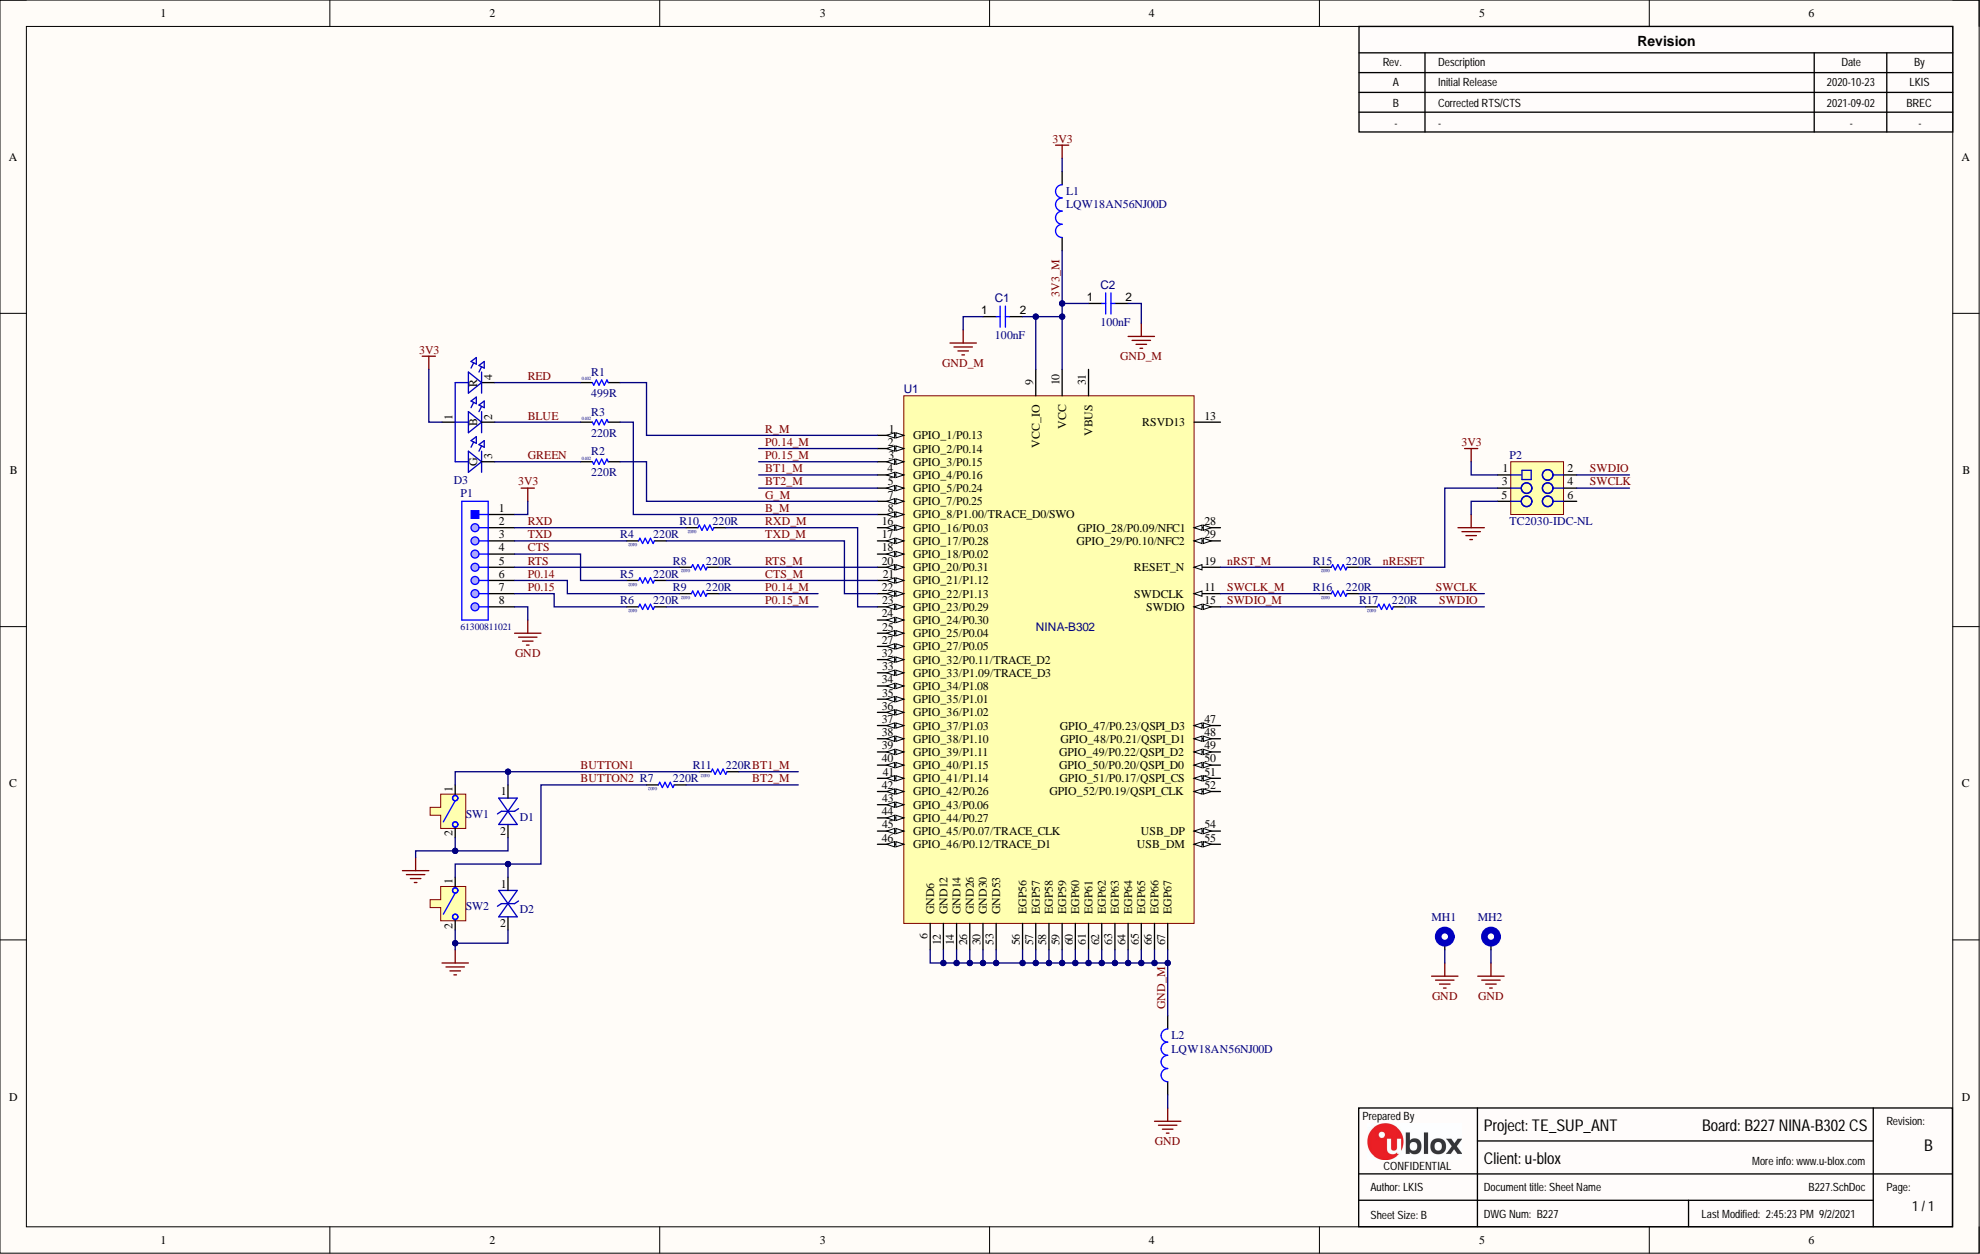
[picture p152: page 1]

Rev. | Description | Date | By
A | Initial Release | 2020-10-23 | LKIS

B | Corrected RTS/CTS | 2021-09-02 | BREC

P0.14_M P0.15_M BT1_M BT2_M G_M | GPIO_2/P0.14 2 GPIO_4/P0.16 4 GPIO_3/P0.15 3 GPIO_5/P0.24 5 GPIO_7/P0.25 7

B_M | GPIO_8/P1.00/TRACE_D0/SWO 8

7 | P0.15 | R9 | 220R 2040 | P0.14_M | GPIO_23/P0.29 23 GPIO_22/P1.13 22

GPIO_25/P0.04 25 GPIO_24/P0.30 24

More info: www.u-blox.com

Author: LKIS | Document title: Sheet Name B227.SchDoc | Page: 1 / 1

Sheet Size: B | DWG Num: B227 | Last Modified: 2:45:23 PM 9/2/2021

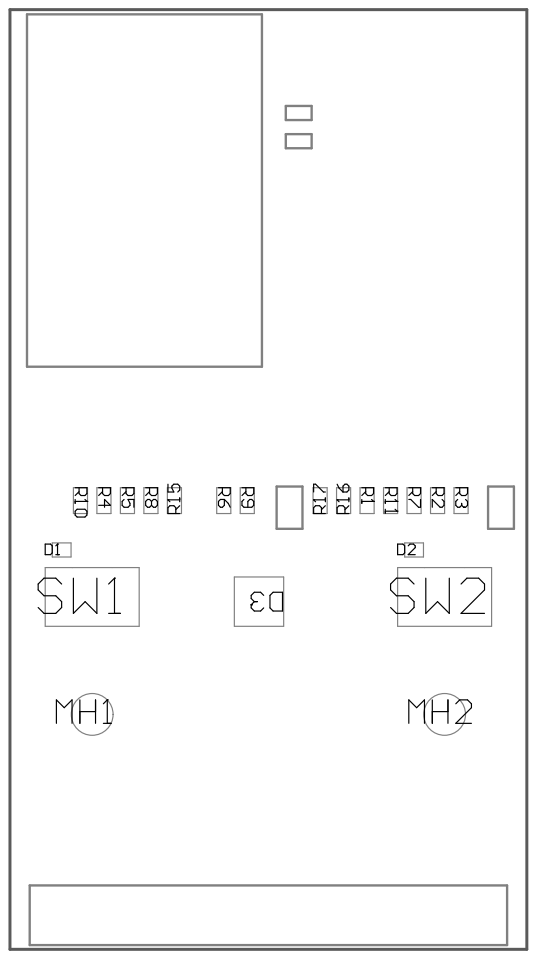
[picture p153: page 2]

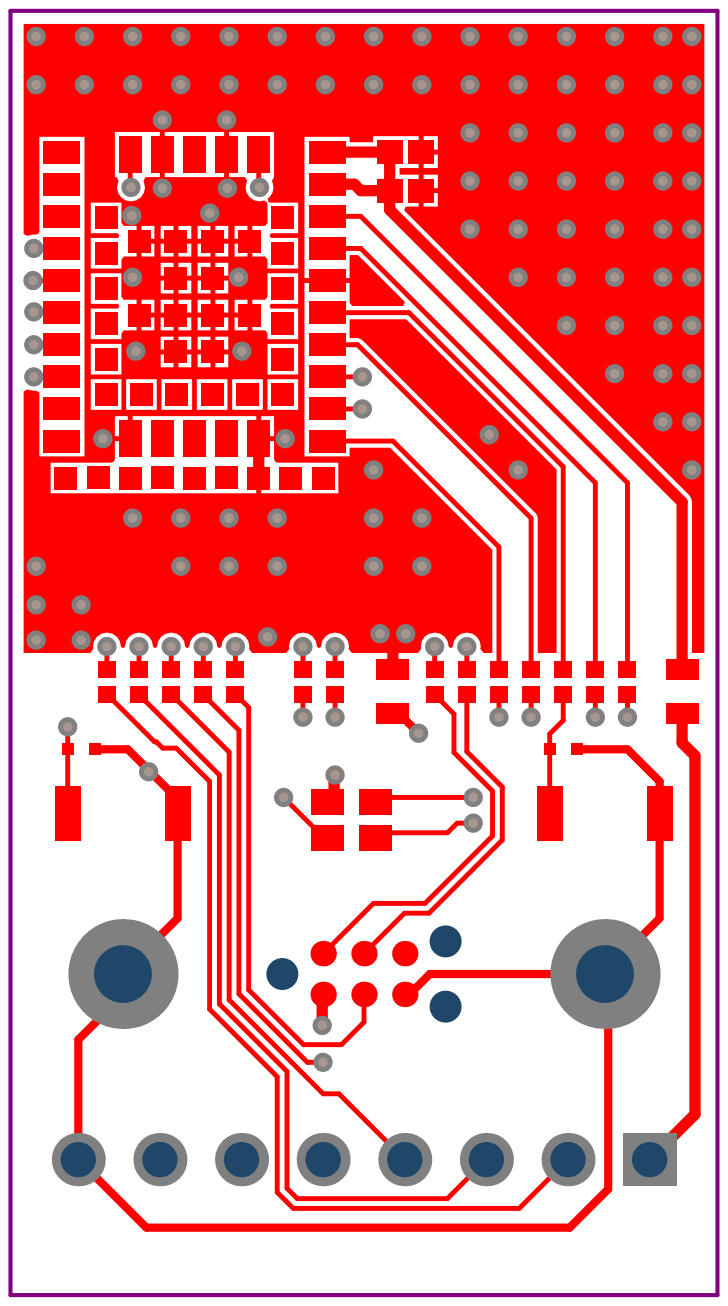
[picture p154: page 4]

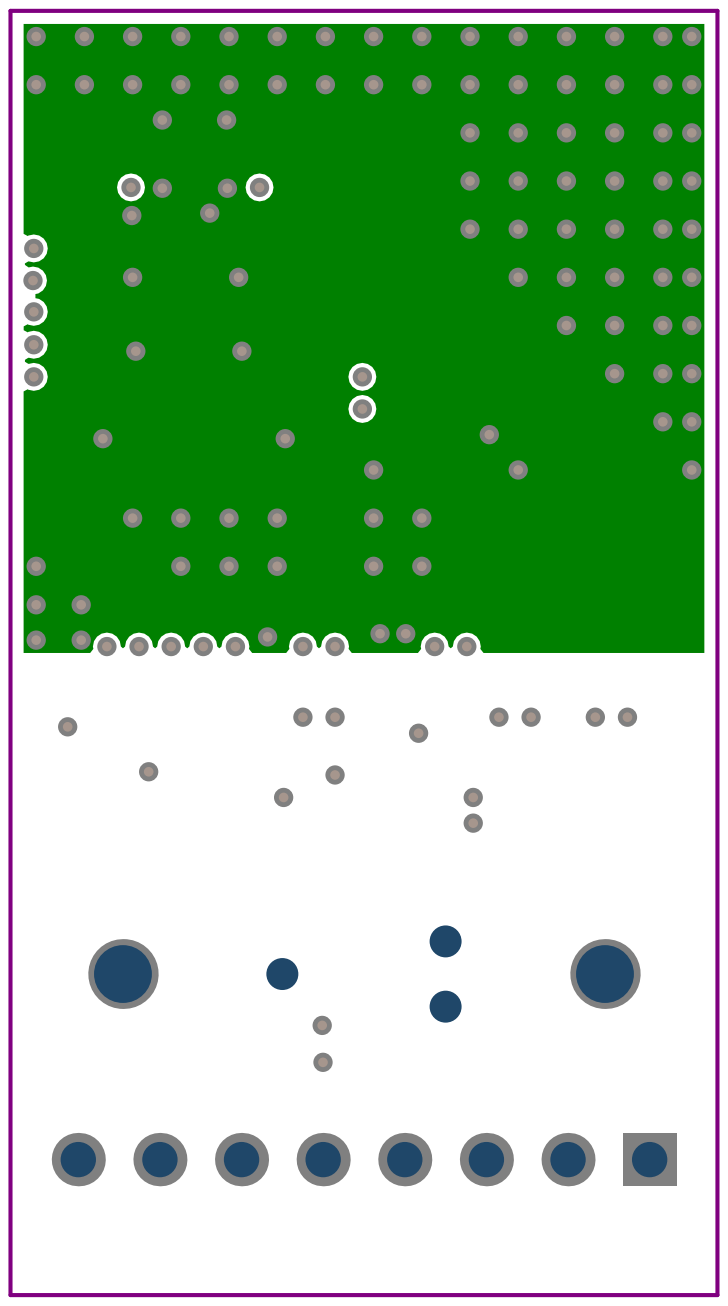
[picture p155: page 5]

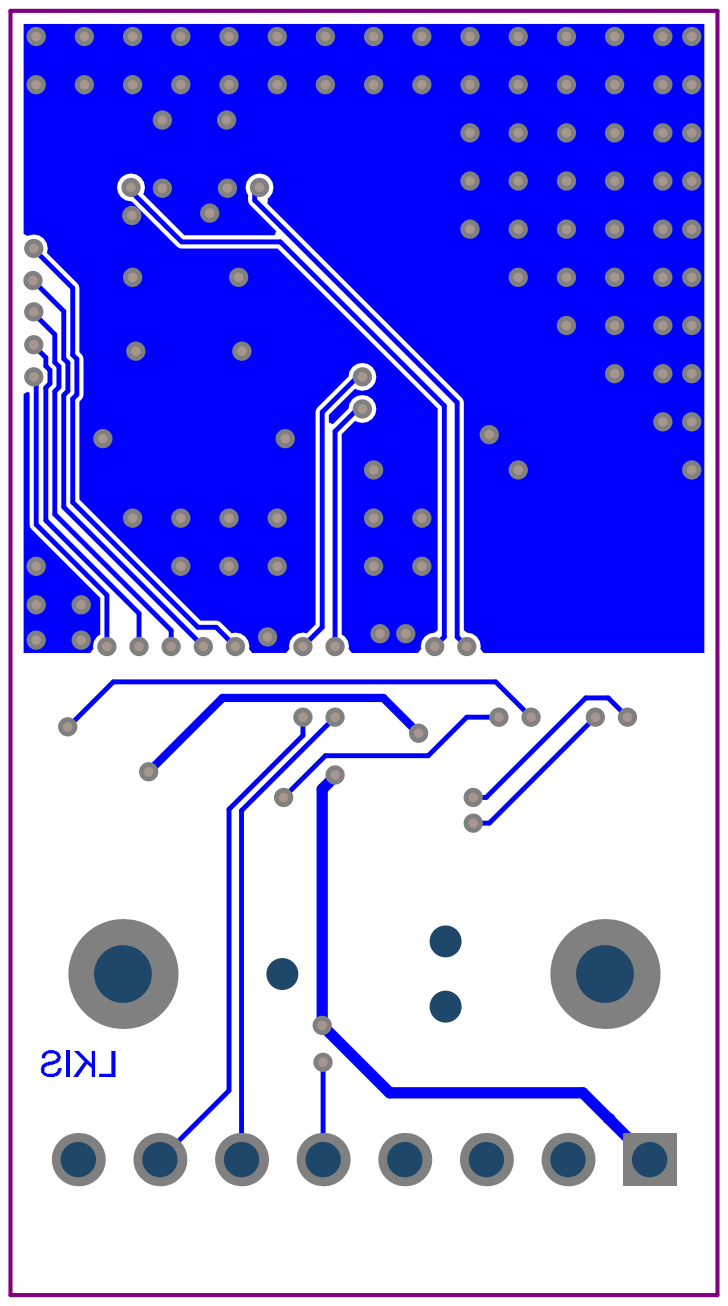
[picture p156: page 7]

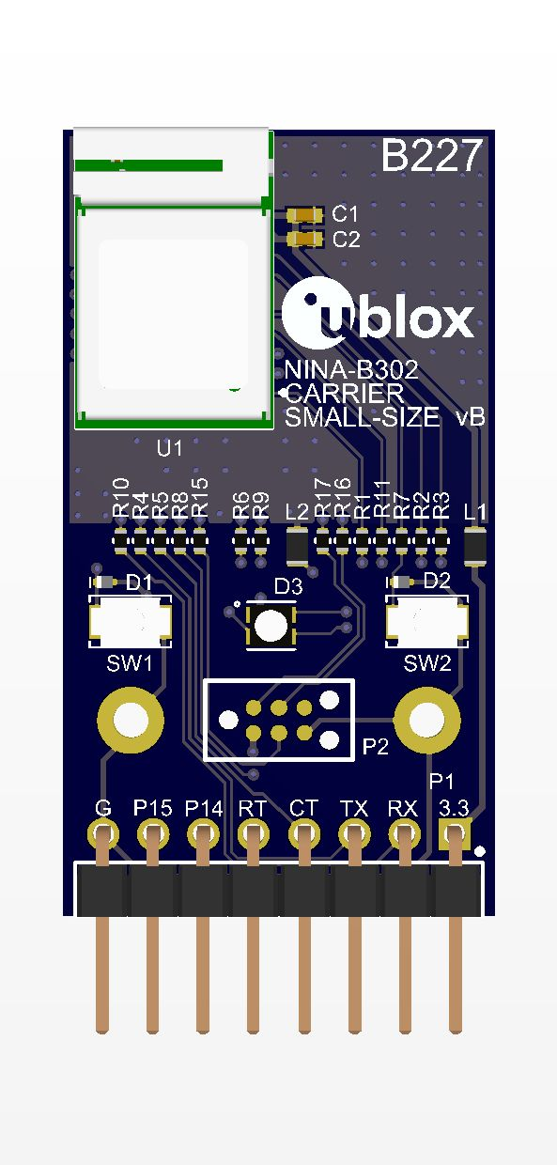
[picture p157: page 8]

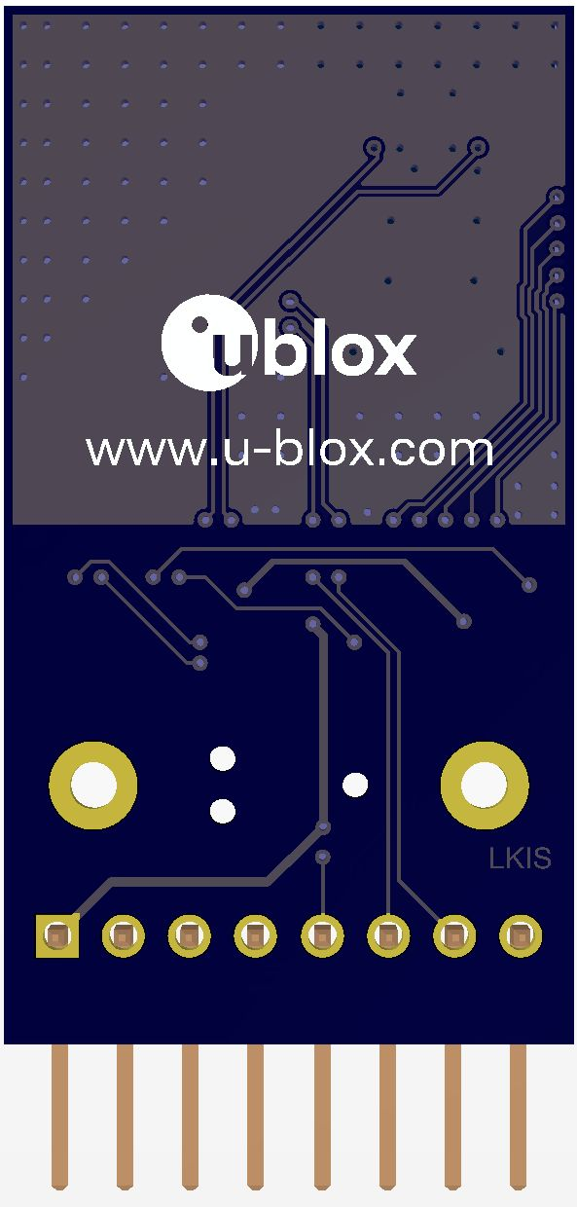
[picture p158: page 9]

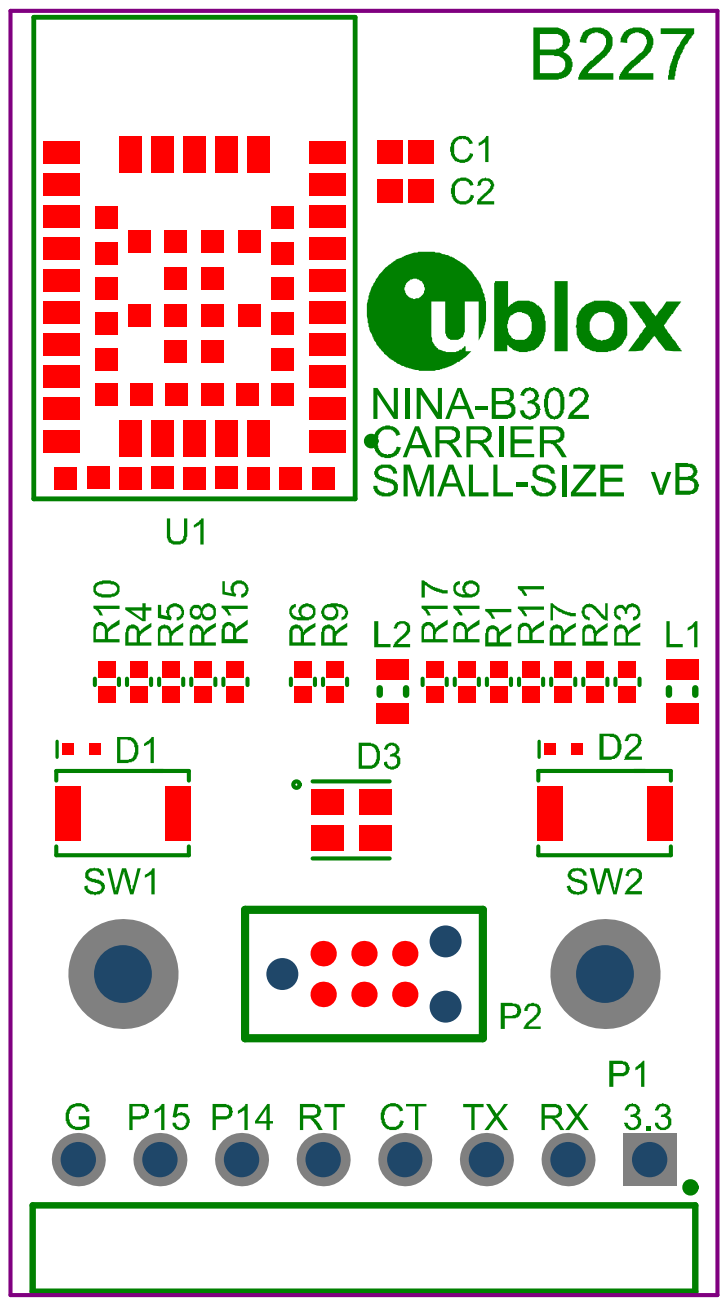
[picture p159: page 11]
