u-blox/blueprints_sho_altium/Designs/B230_NINA-B406_carrier_mid/Documentation/B230 B.PDF

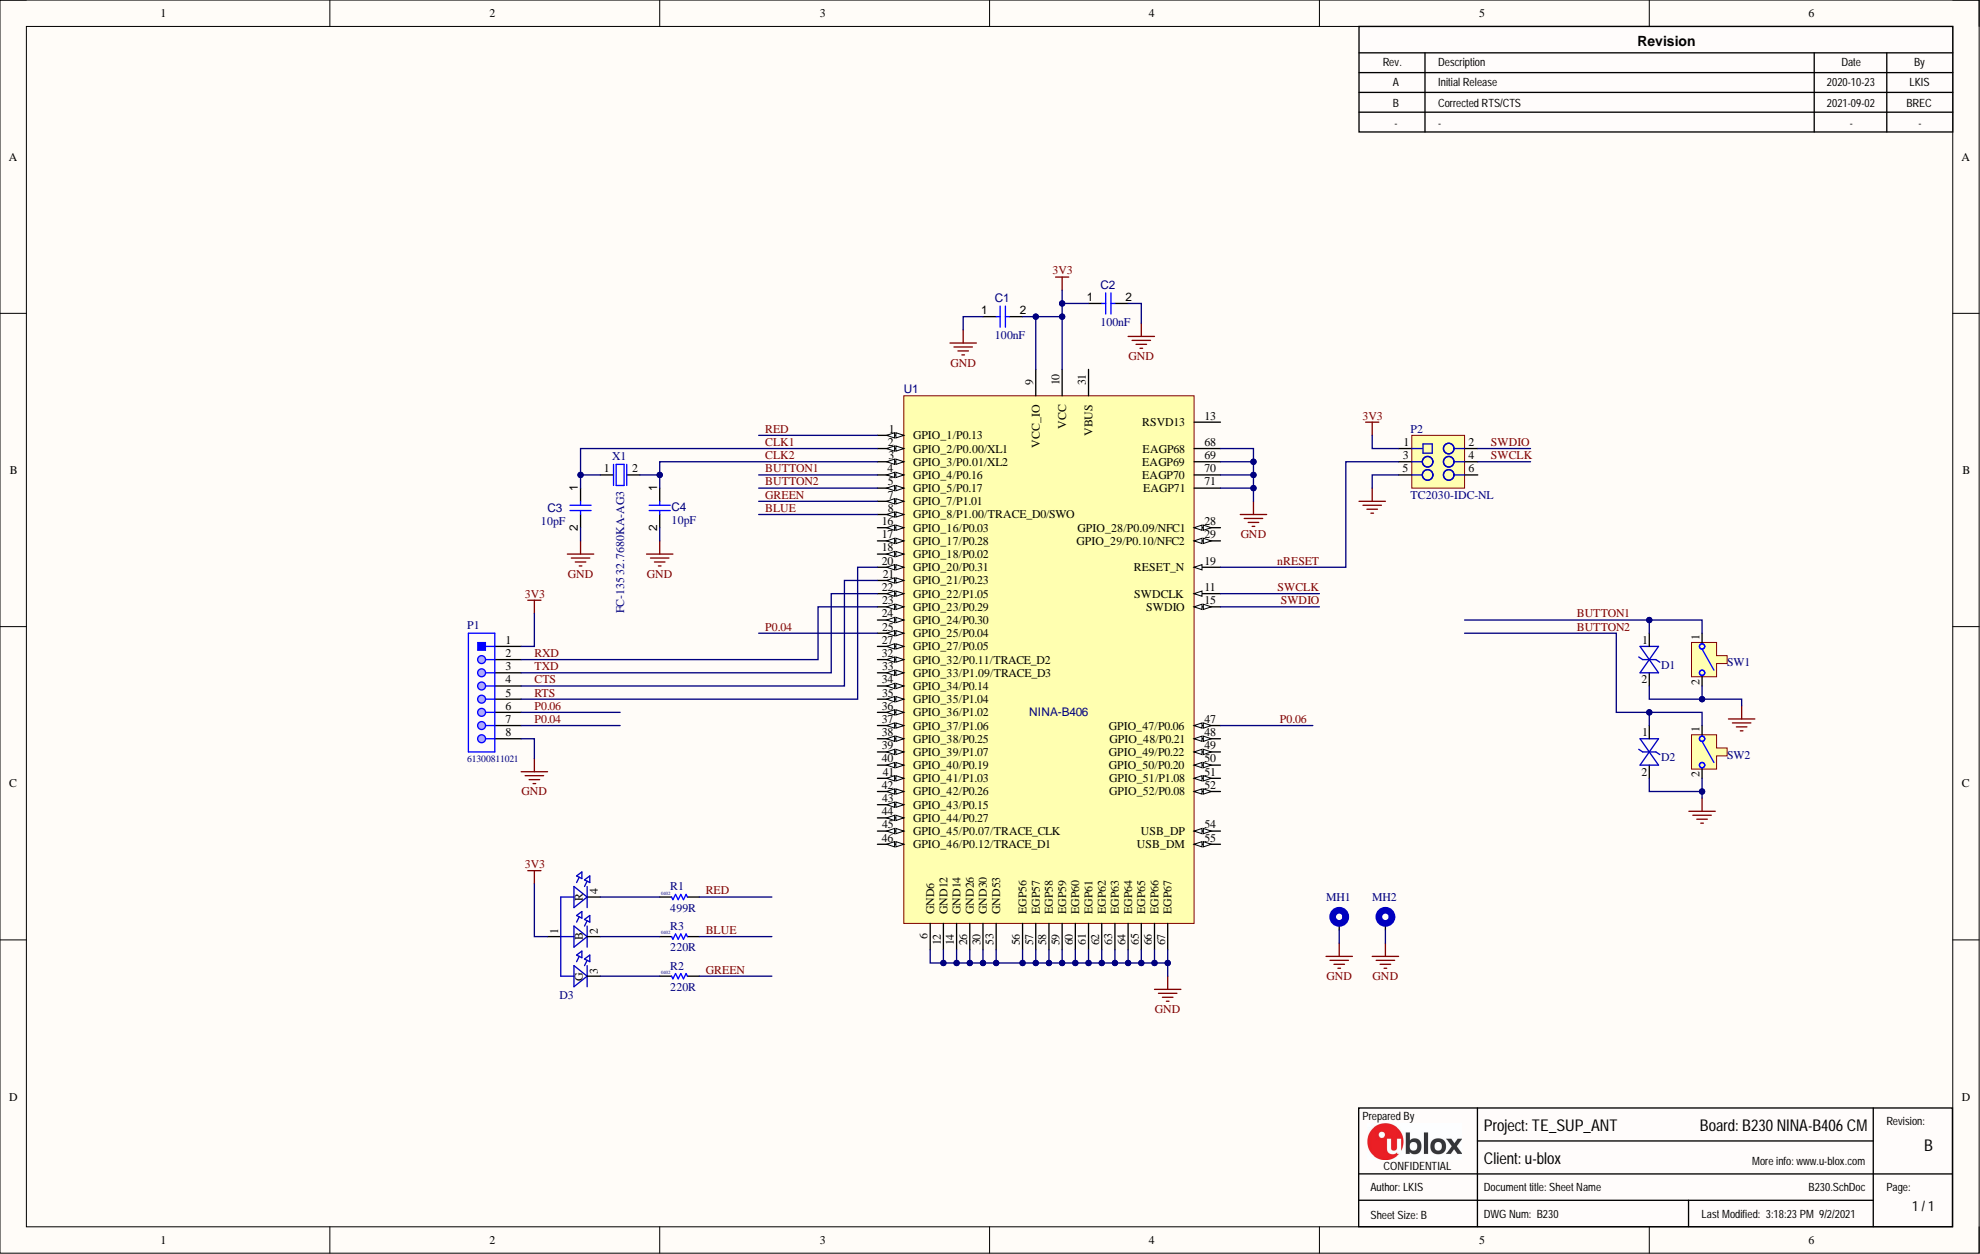
[picture p168: page 1]

Rev. | Description | Date | By
A | Initial Release | 2020-10-23 | LKIS

B | Corrected RTS/CTS | 2021-09-02 | BREC

BU T T O N 1 | 4 | 7 0 | | D nRE S E T | 5

T X D | 3 3
CT S | 3 4
RT S | 3 5

More info: www.u-blox.com

Author: LKIS | Document title: Sheet Name B230.SchDoc | Page: 1 / 1

Sheet Si ze: B | DWG Num: B230 | Last Modified: 3:18:23 PM 9/2/2021

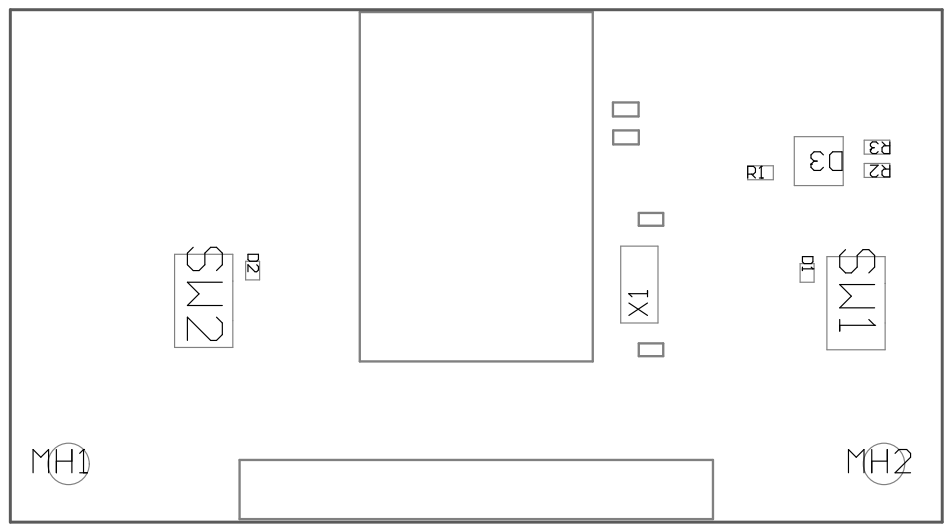
[picture p169: page 2]

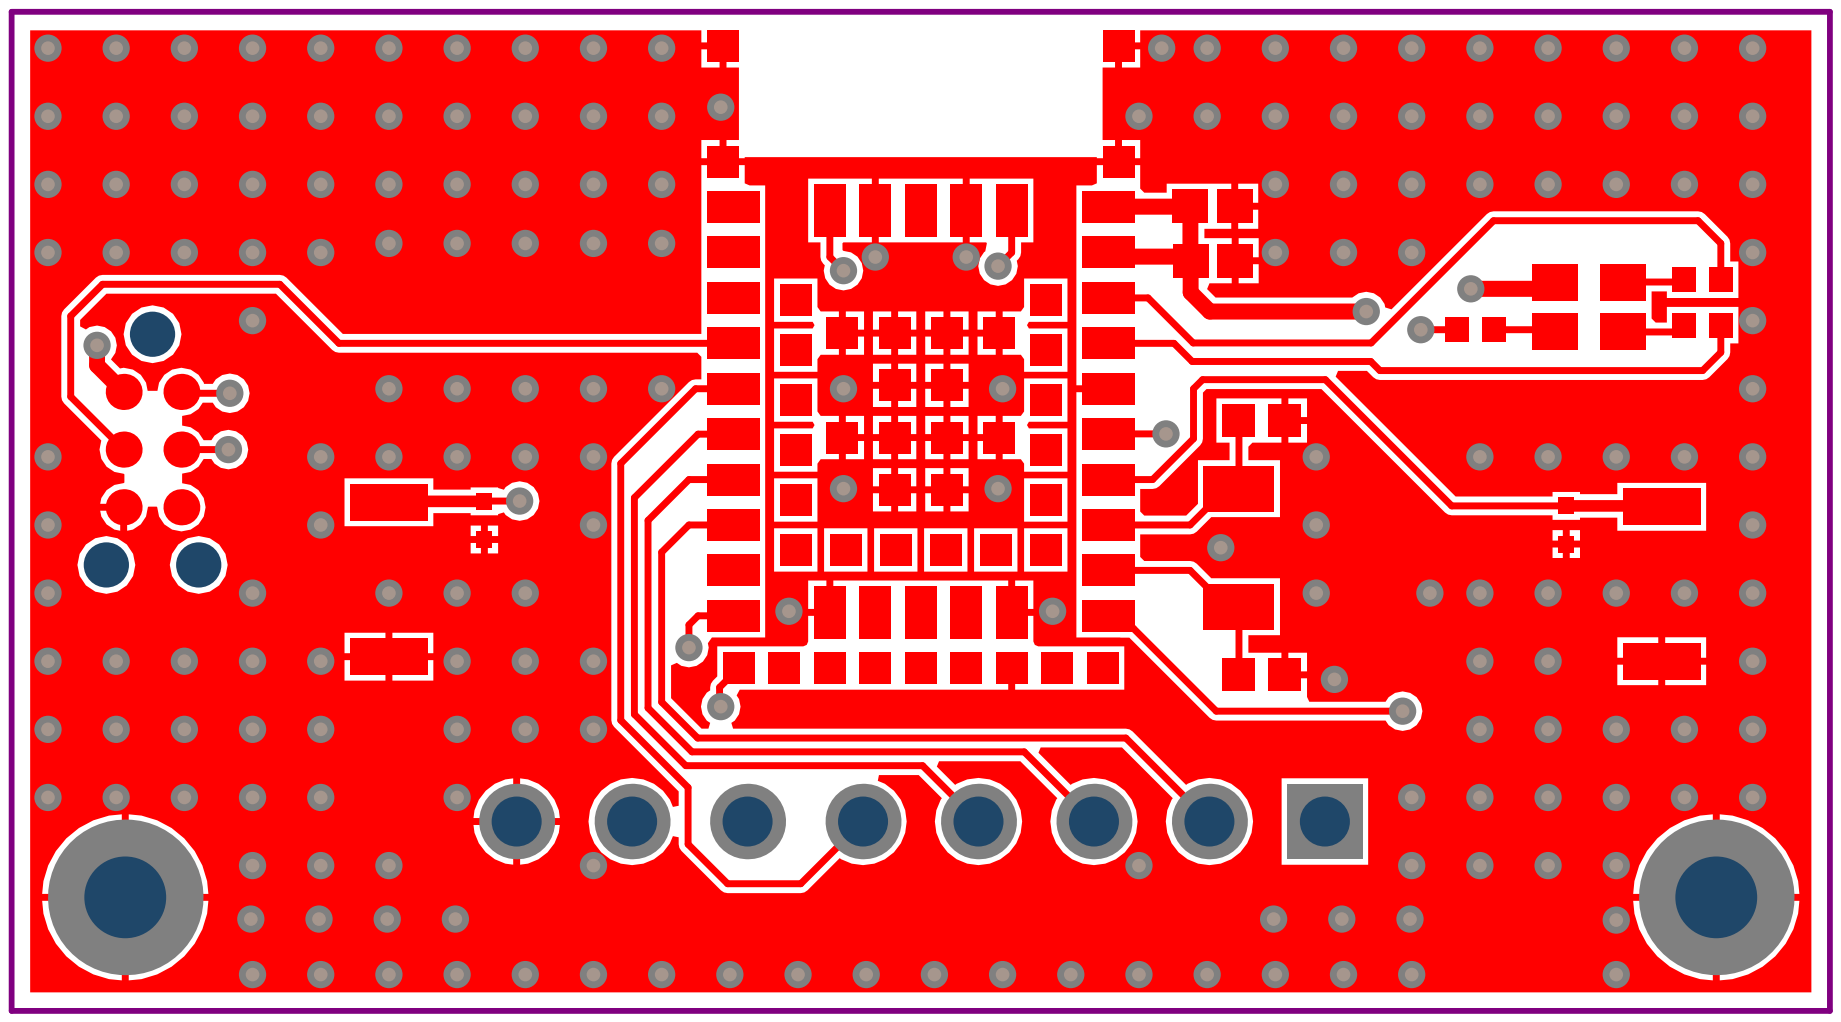
[picture p170: page 4]

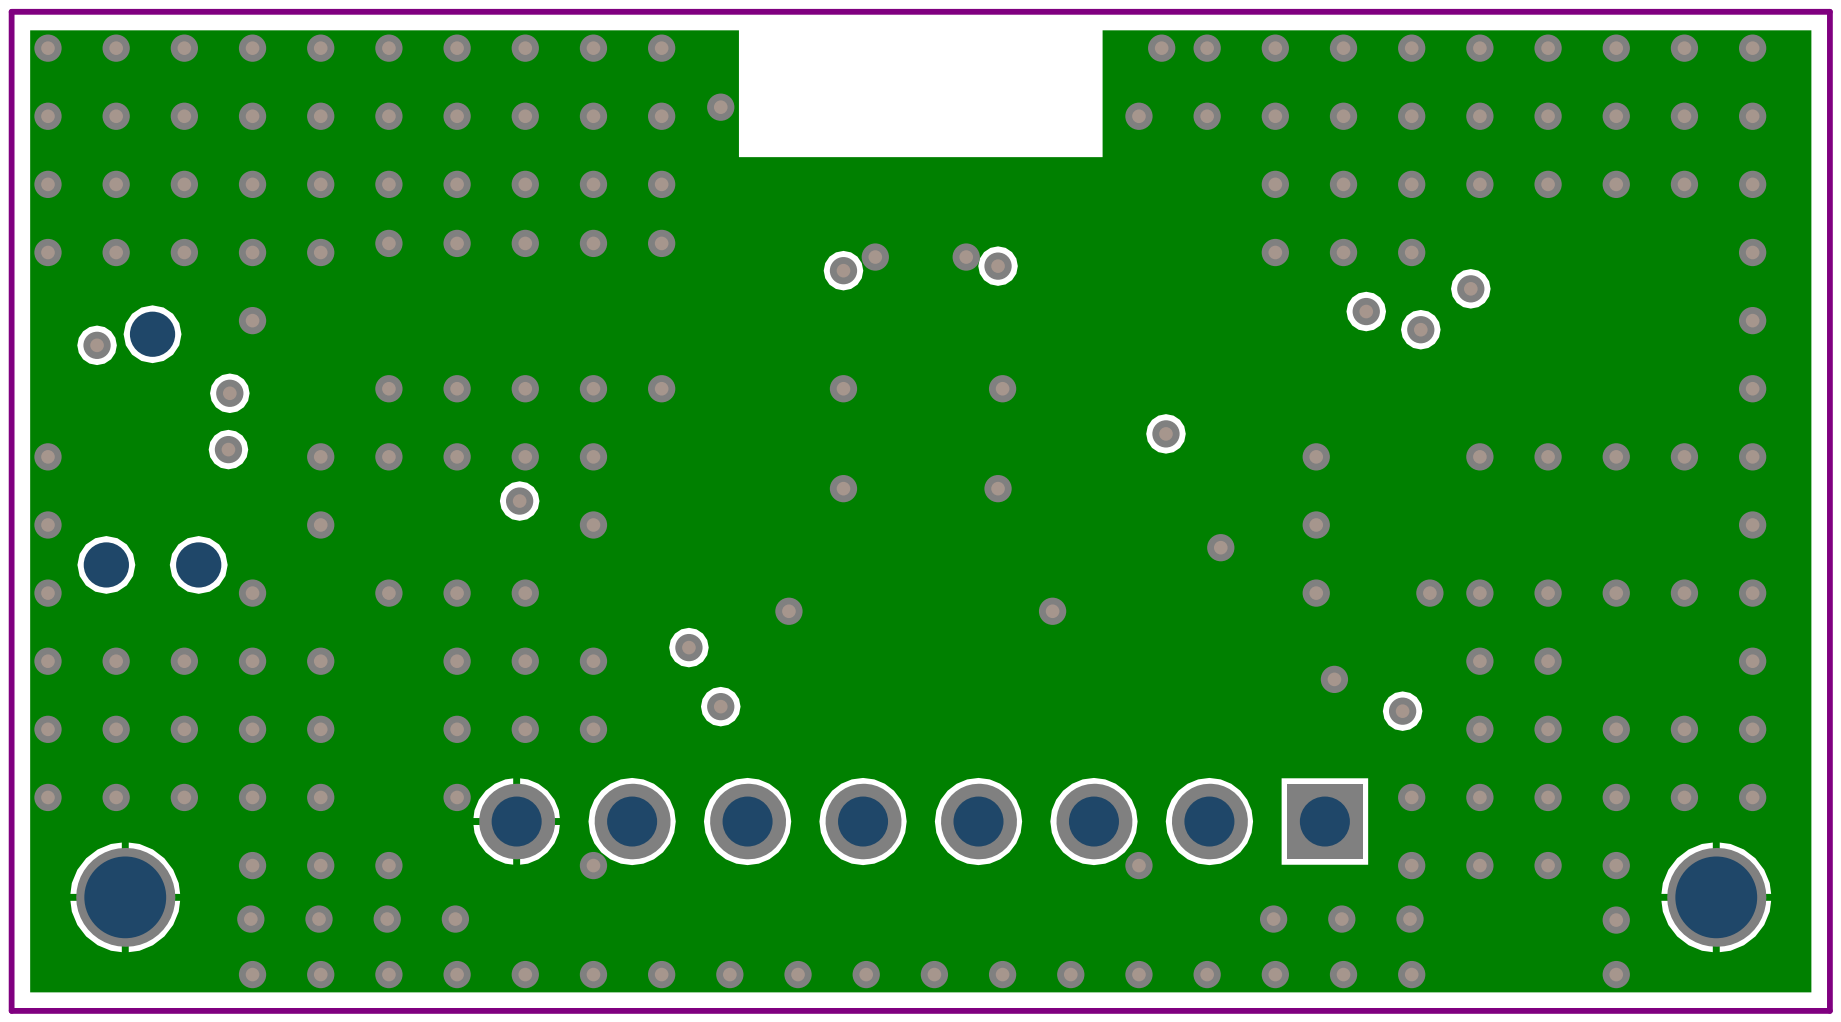
[picture p171: page 5]

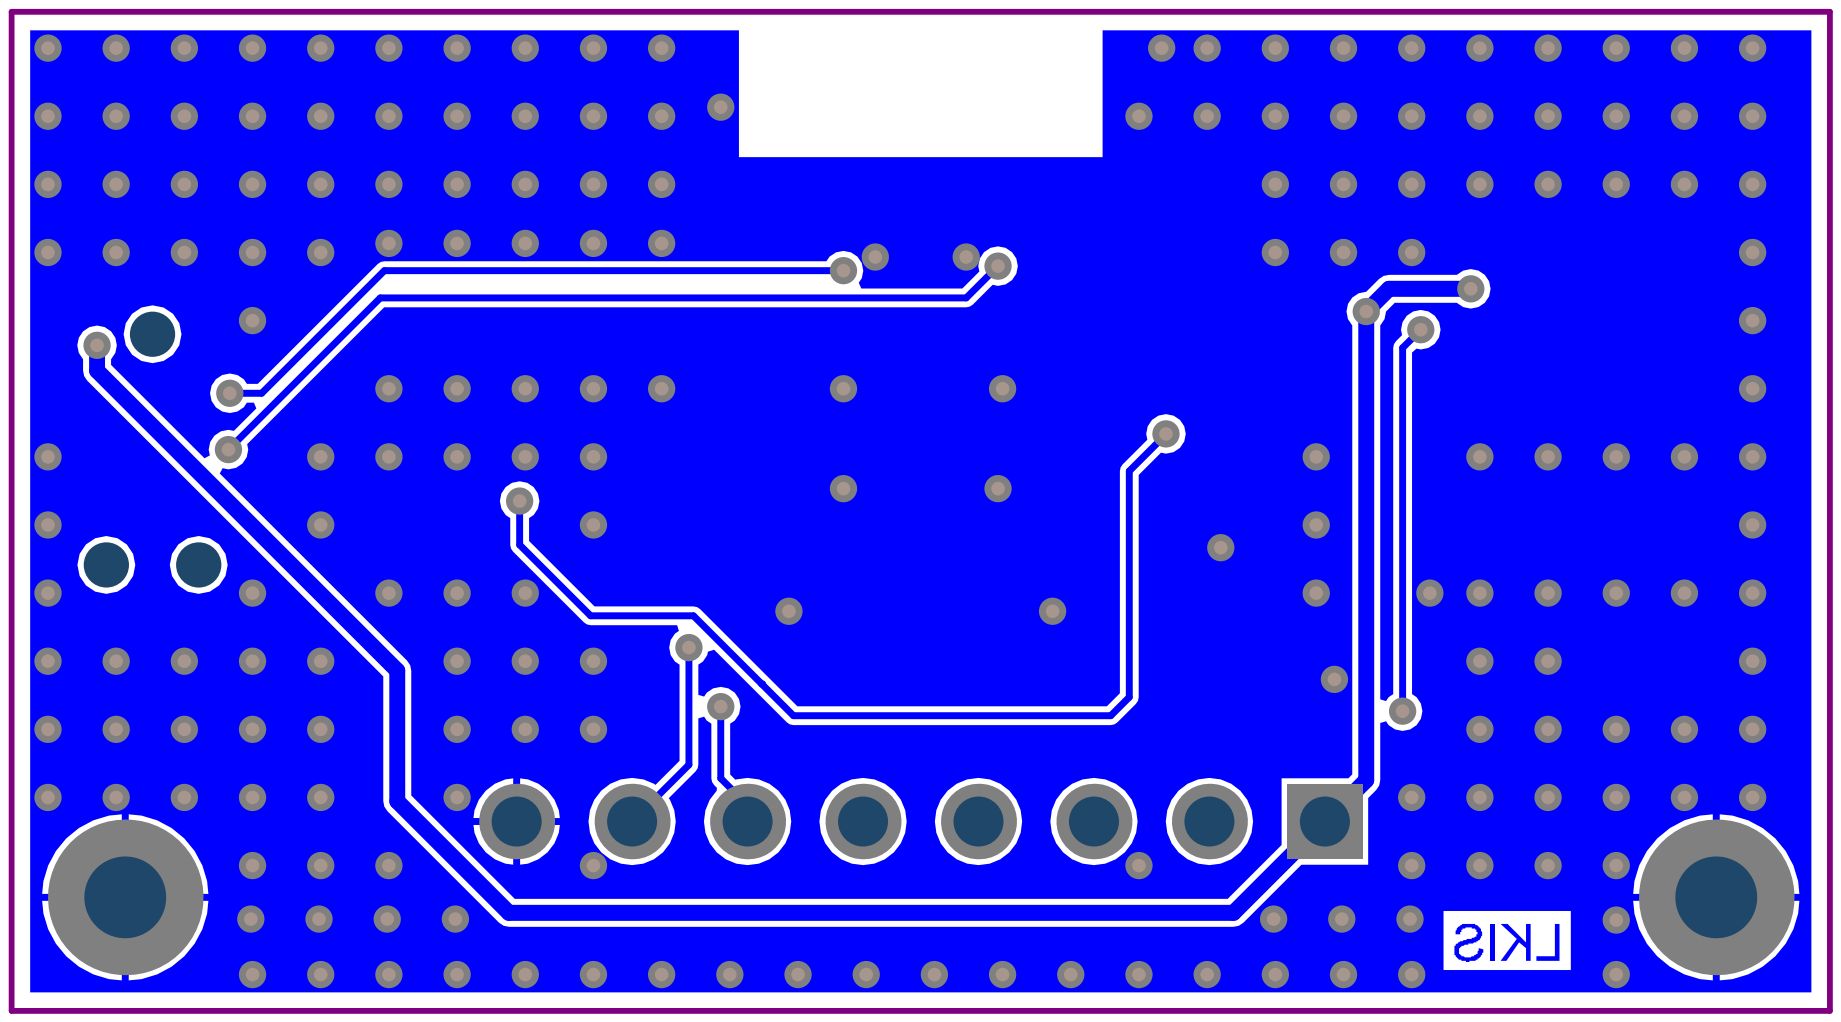
[picture p172: page 7]

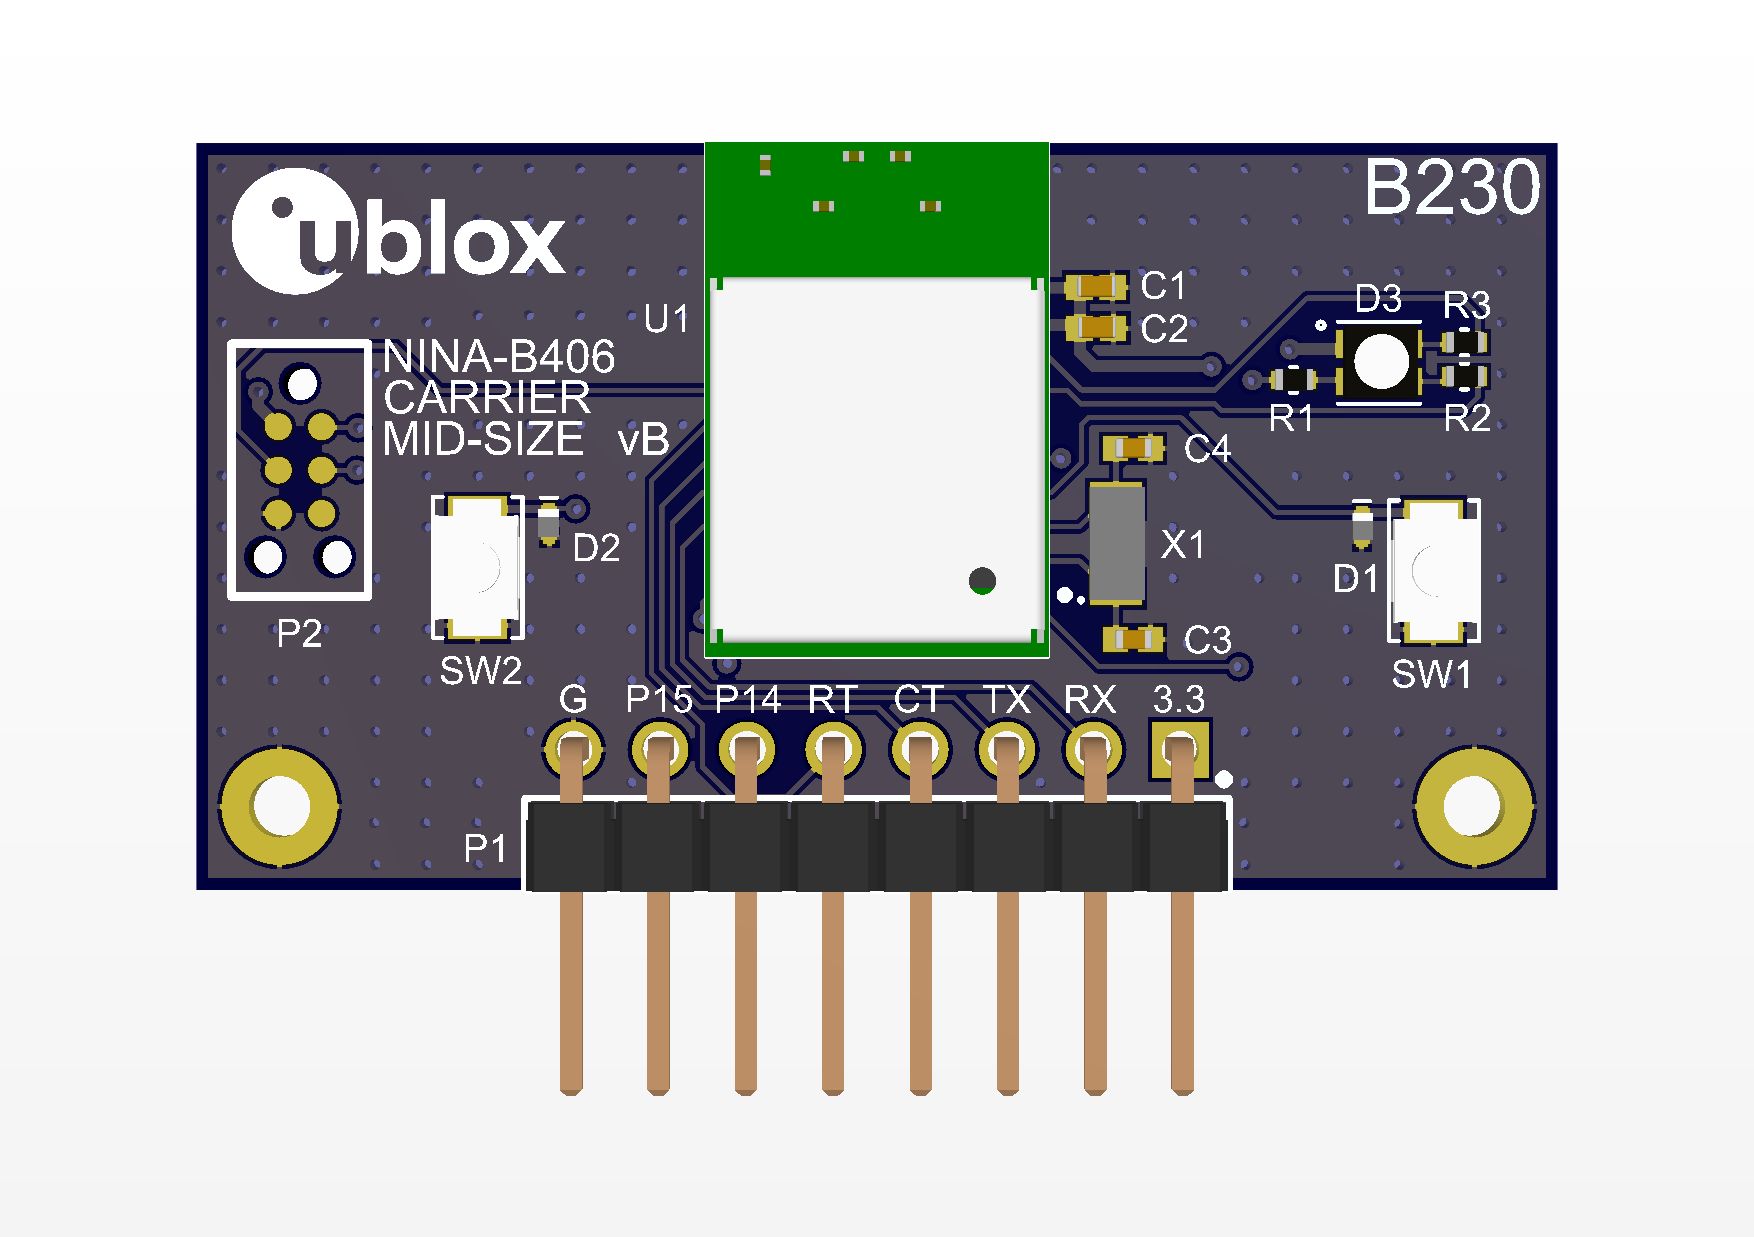
[picture p173: page 8]

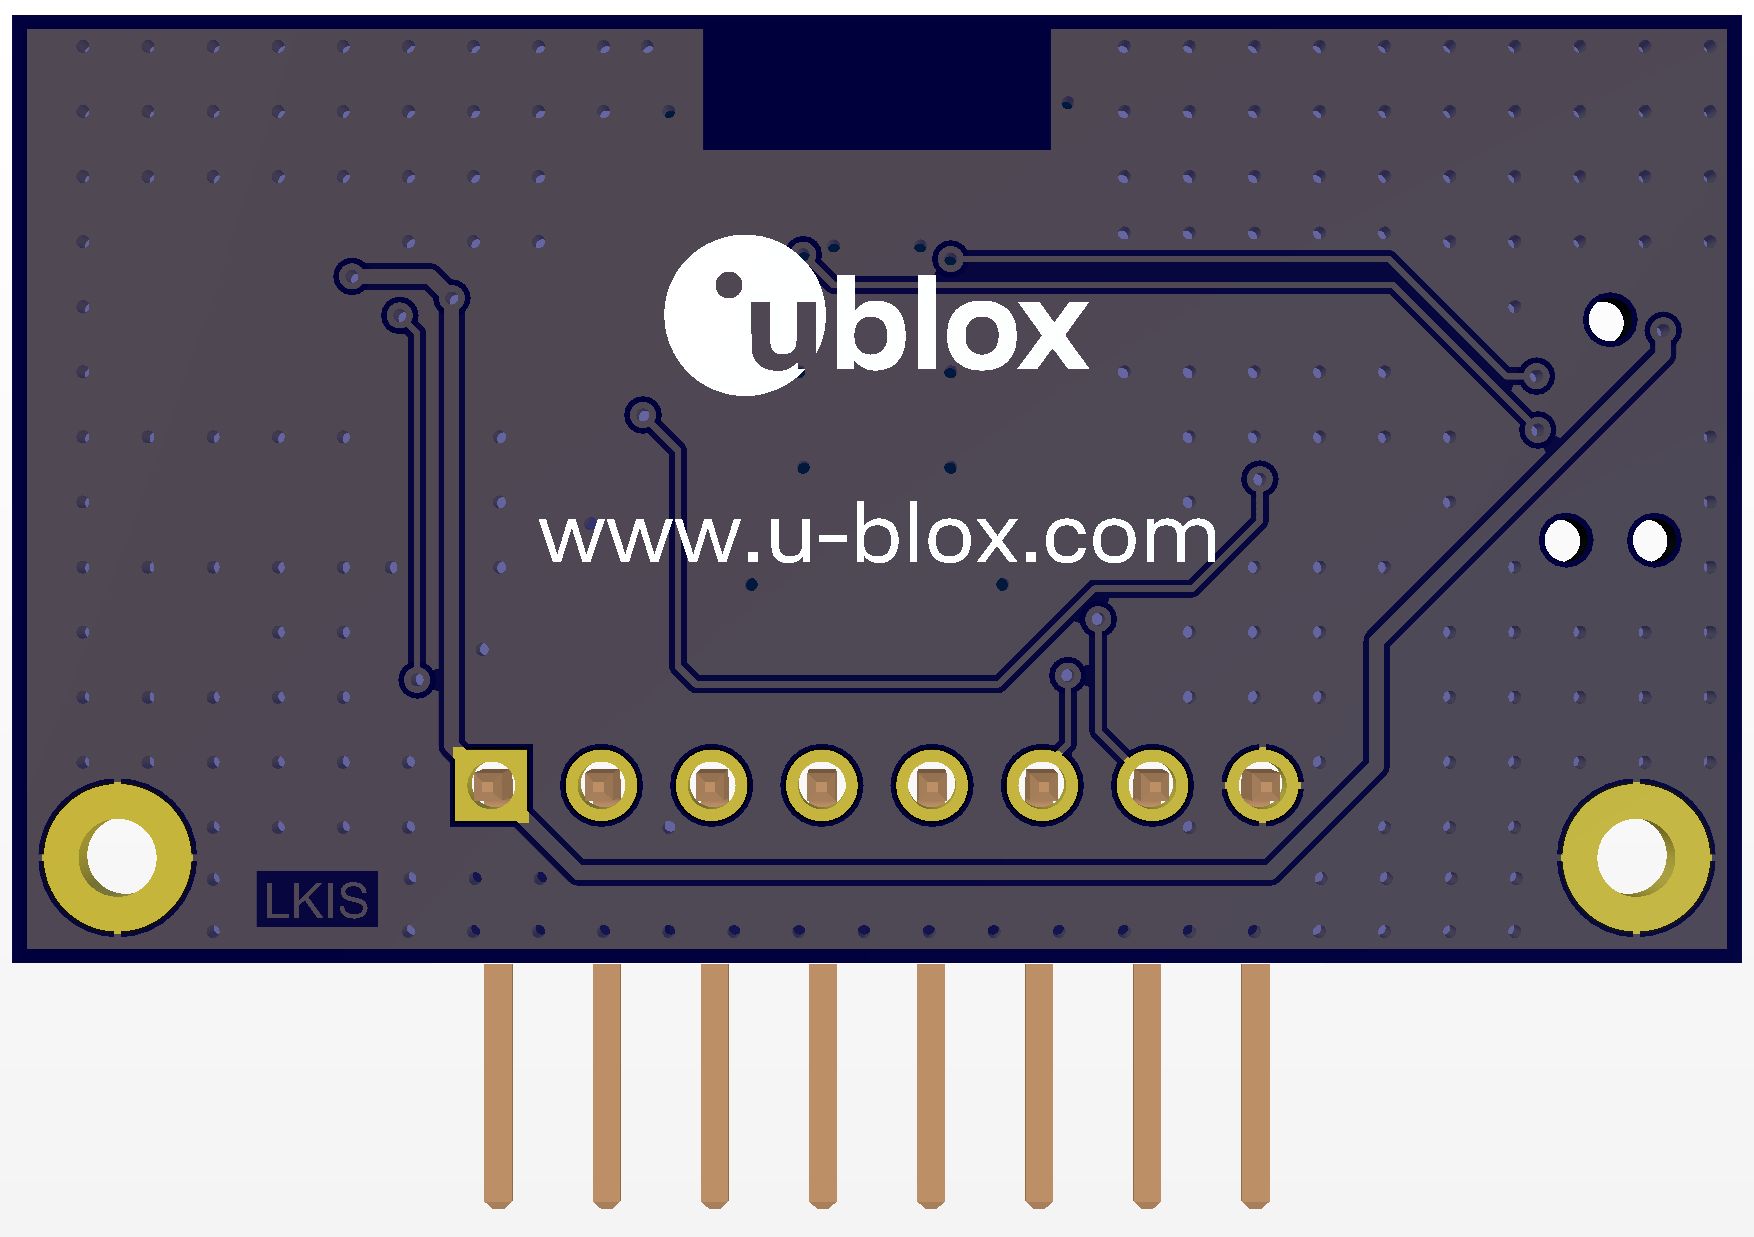
[picture p174: page 9]

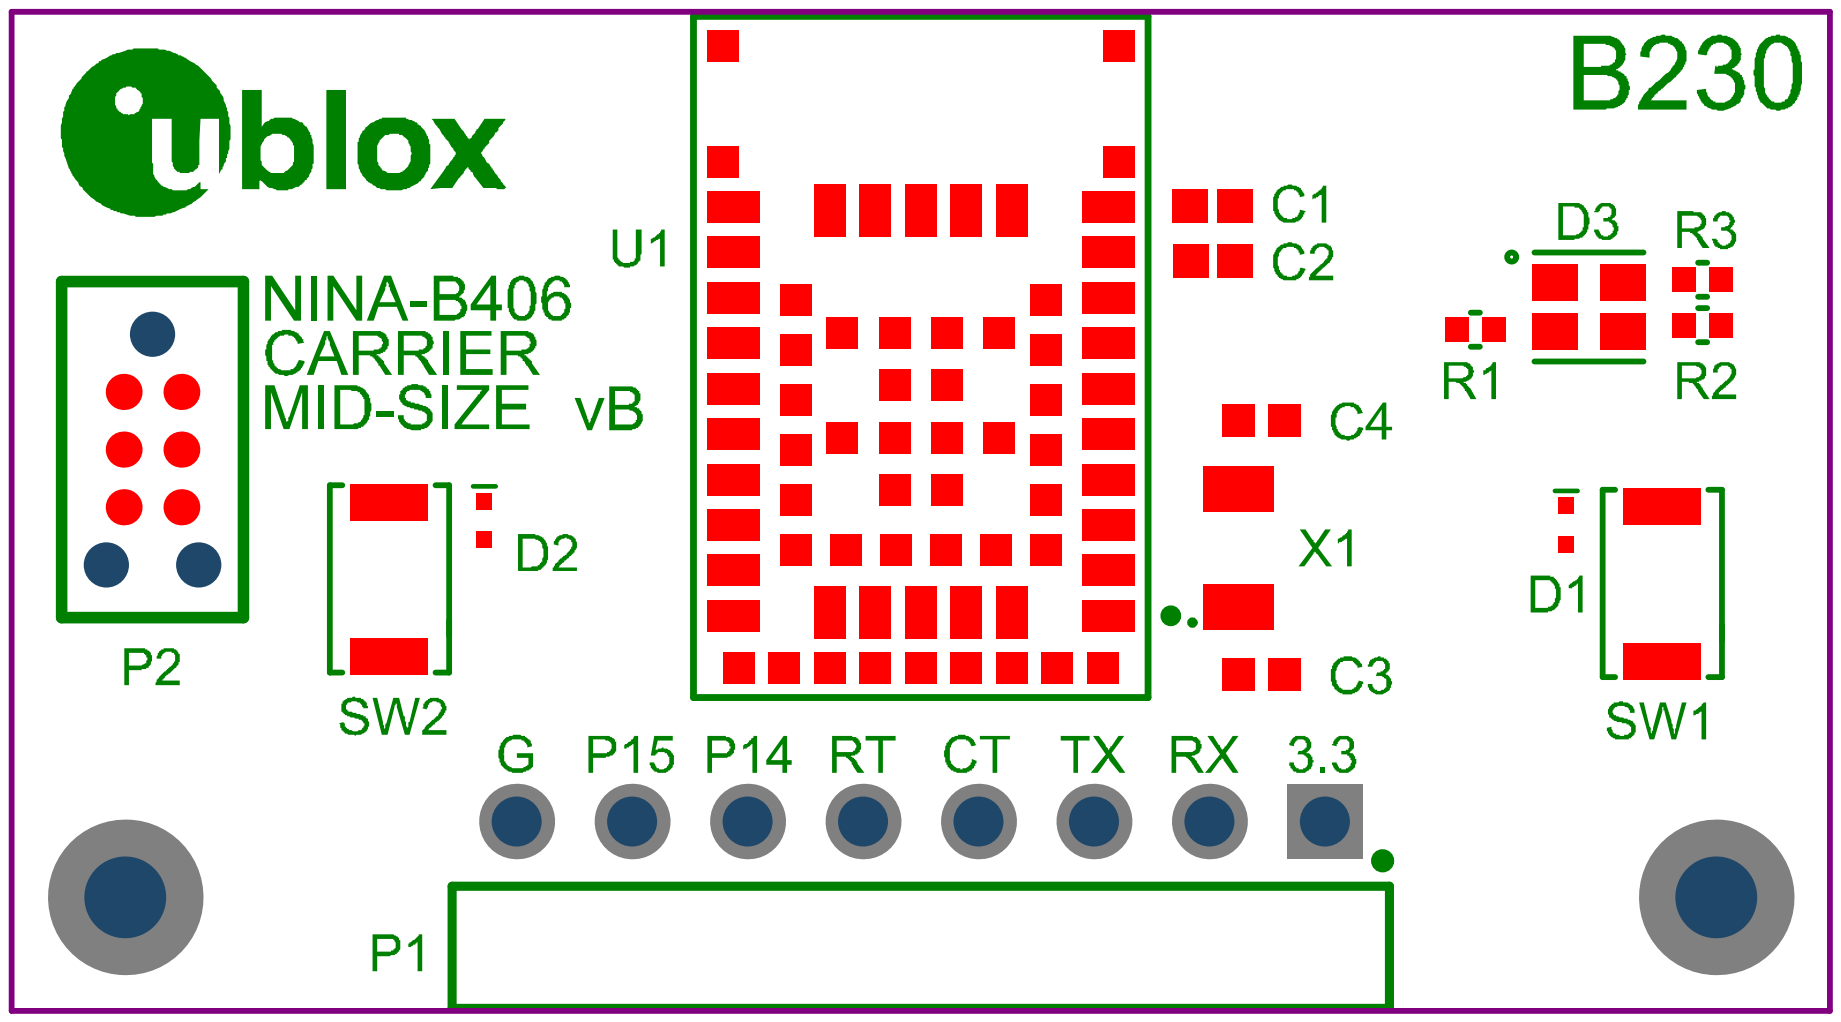
[picture p175: page 11]
