u-blox/blueprints_sho_altium/Designs/B233_NORA-B106_carrier_small/Documentation/B233 A.PDF

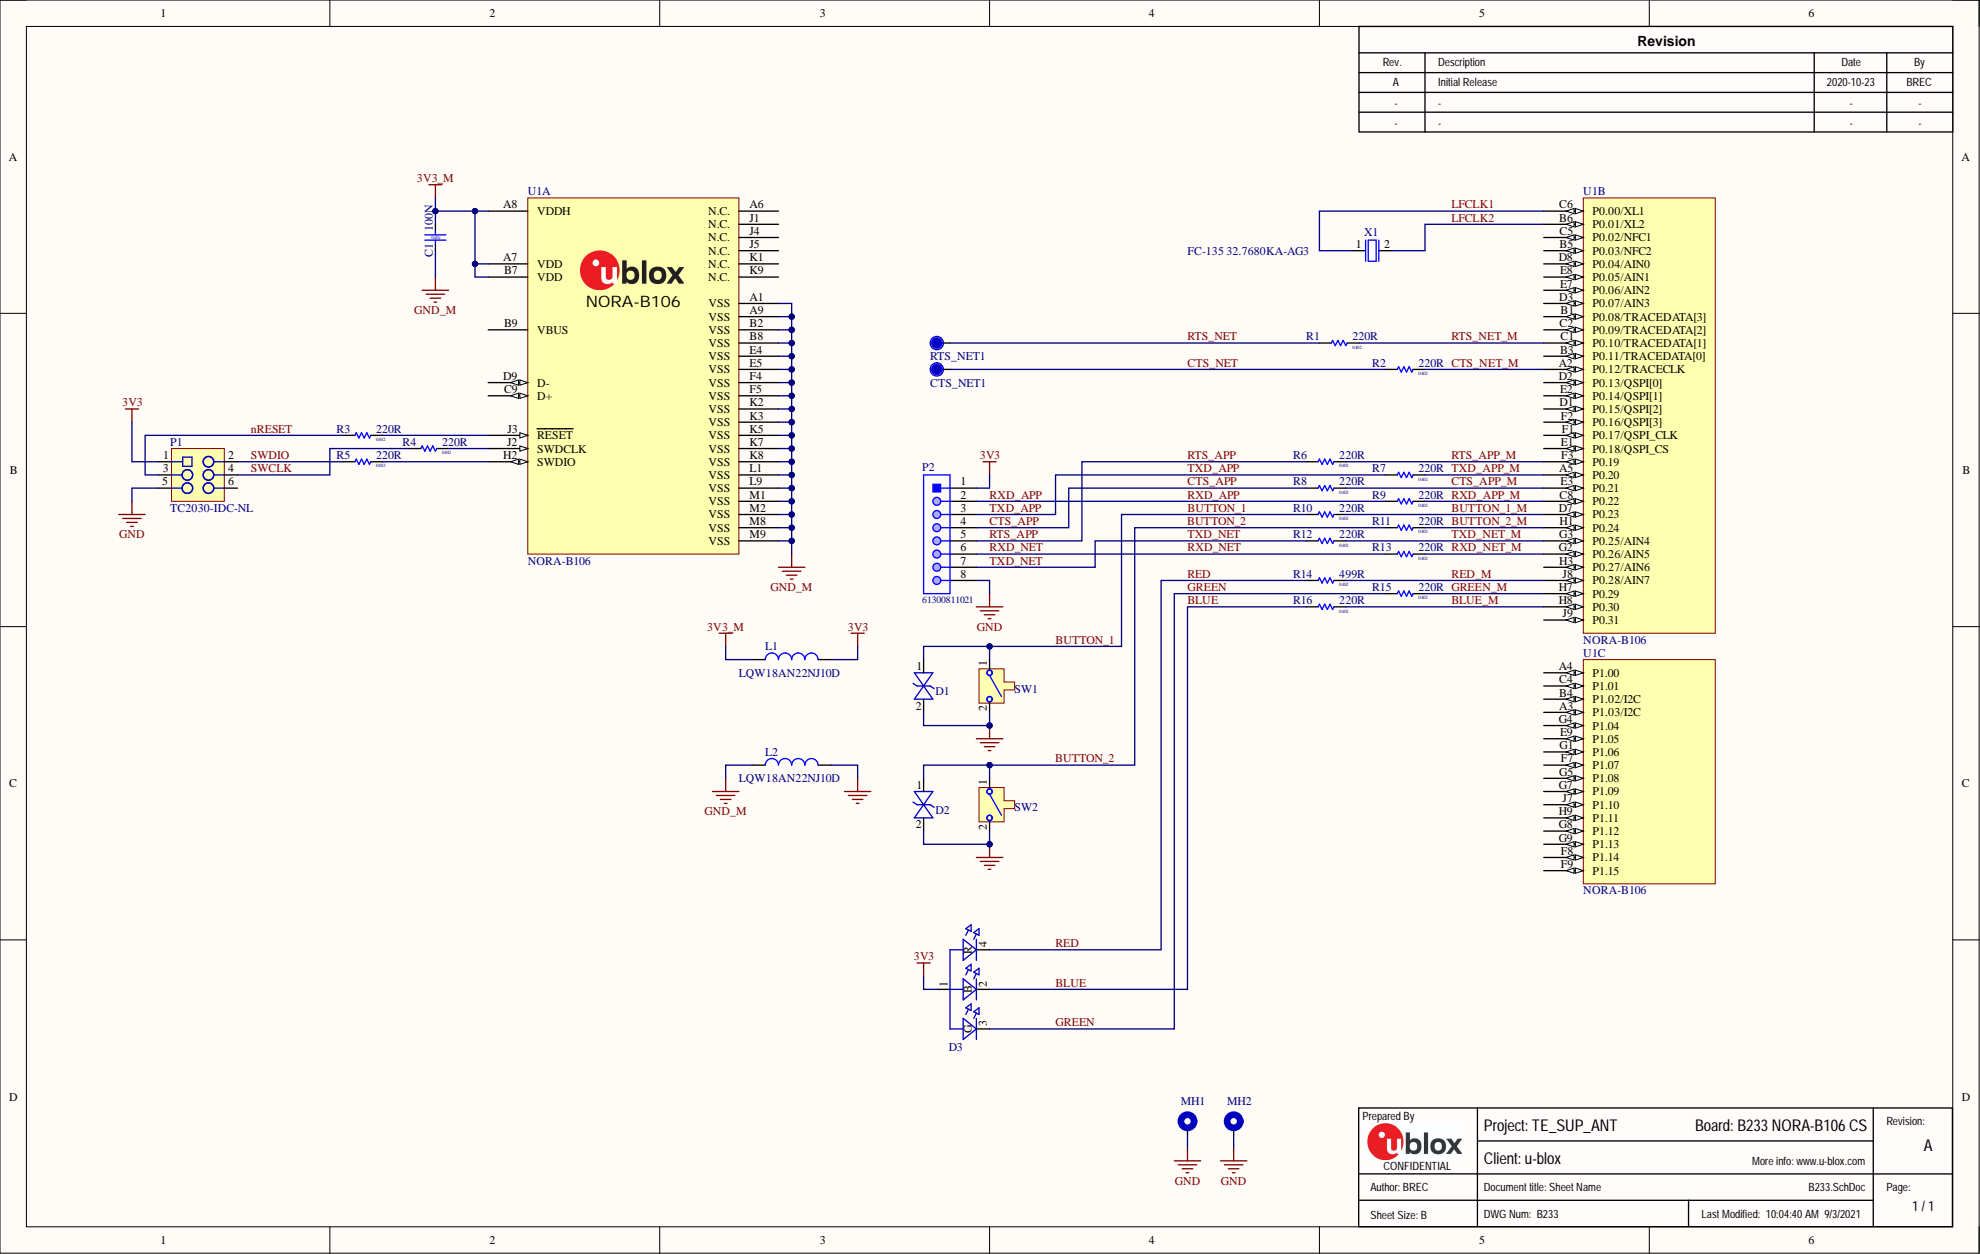
[picture p176: page 1]

Rev. | Description | Date | By
A | Initial Release | 2020-10-23 | BREC

GREEN BLUE R16

BUTTON_1

More info: www.u-blox.com

Author: BREC | Document title: Sheet Name B233.SchDoc | Page: 1 / 1

Sheet Size: B | DWG Num: B233 | Last Modified: 10:04:40 AM 9/3/2021

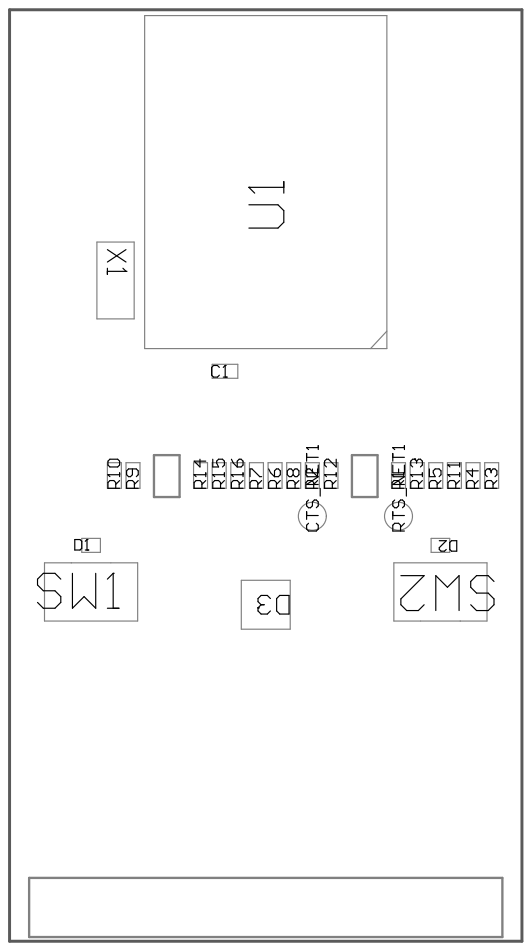
[picture p177: page 2]

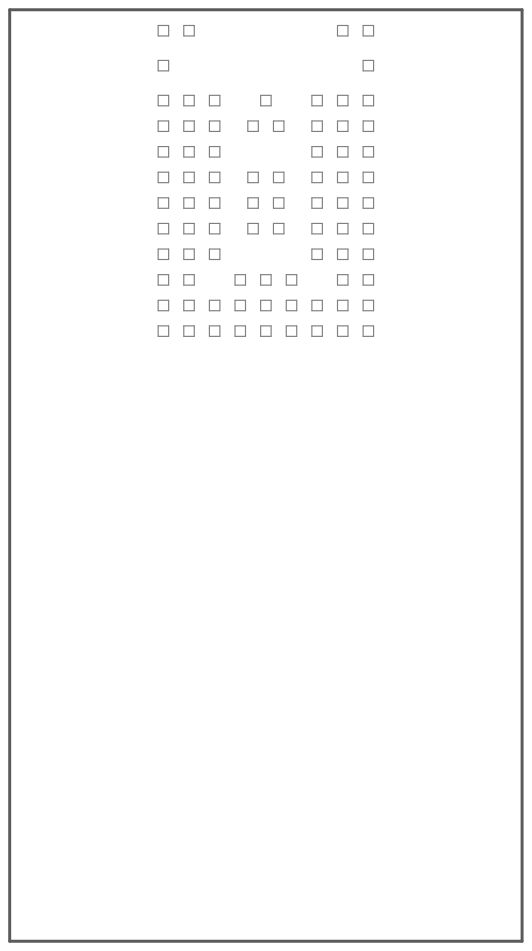
[picture p178: page 3]

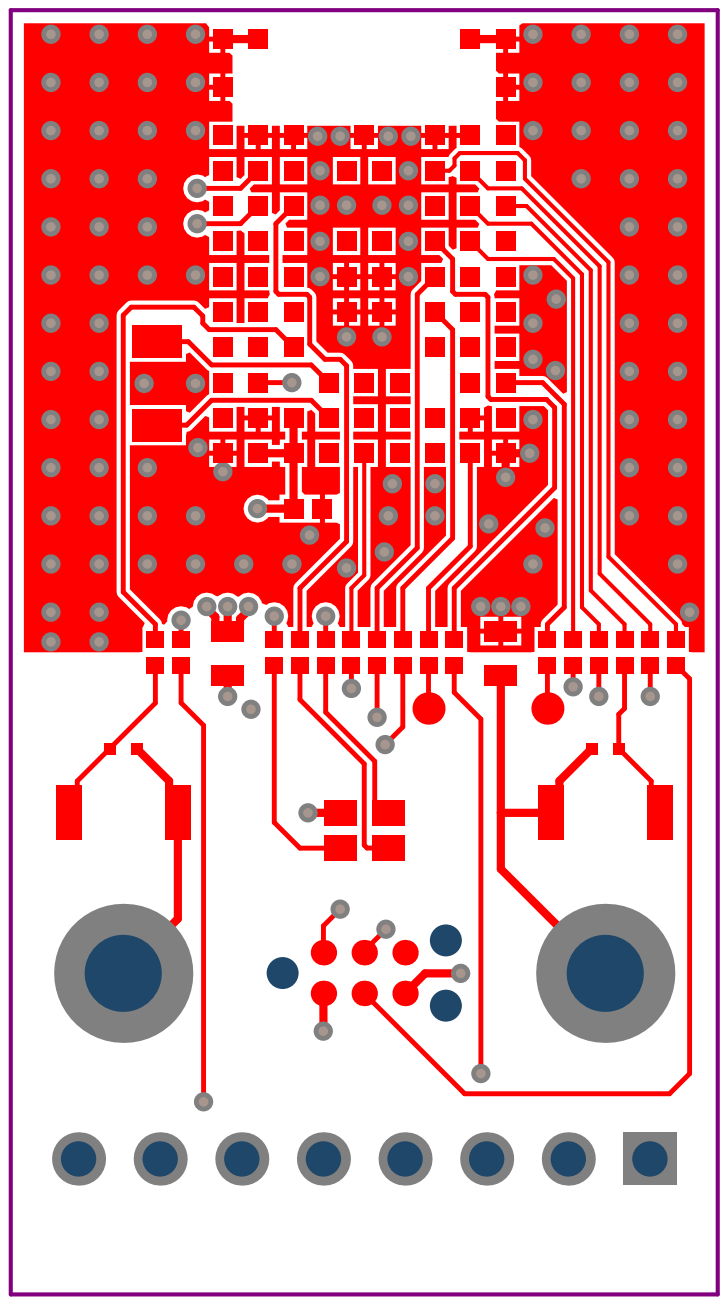
[picture p179: page 4]

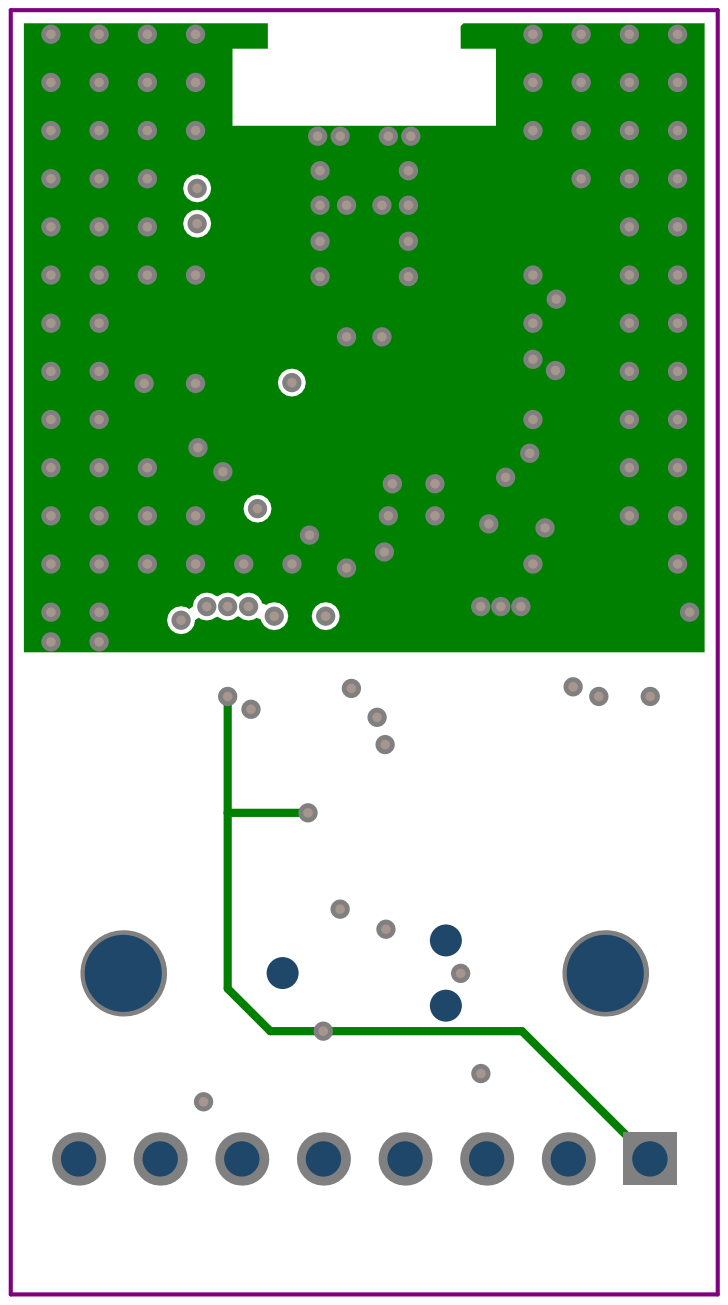
[picture p180: page 5]

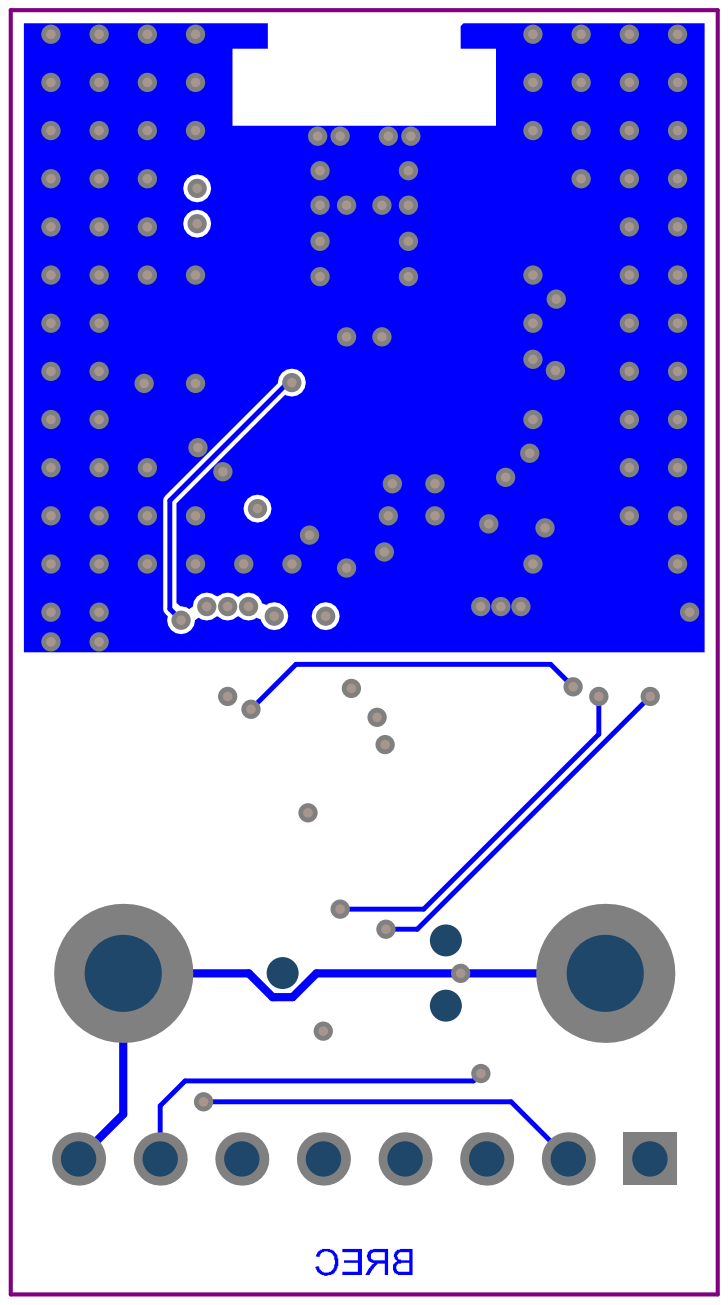
[picture p181: page 7]

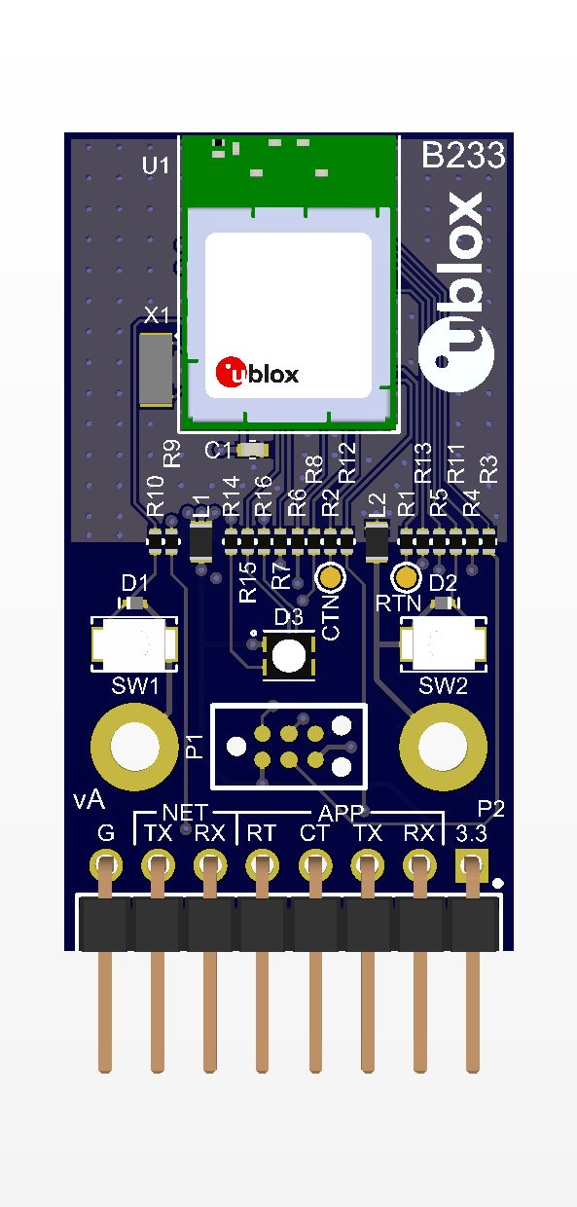
[picture p182: page 8]

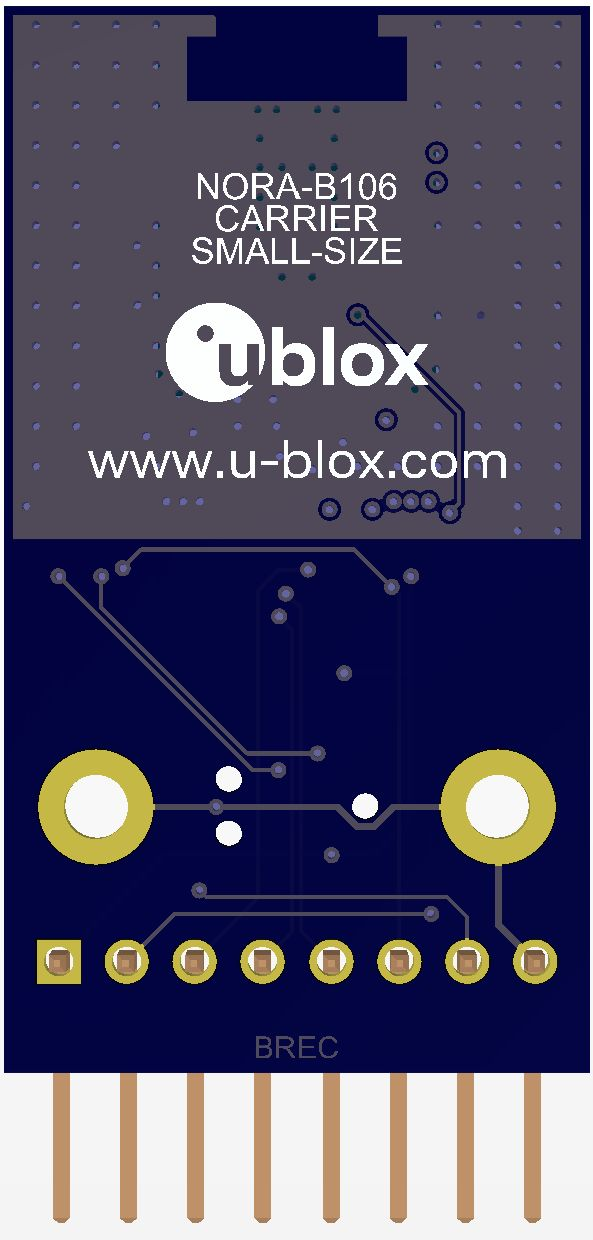
[picture p183: page 9]

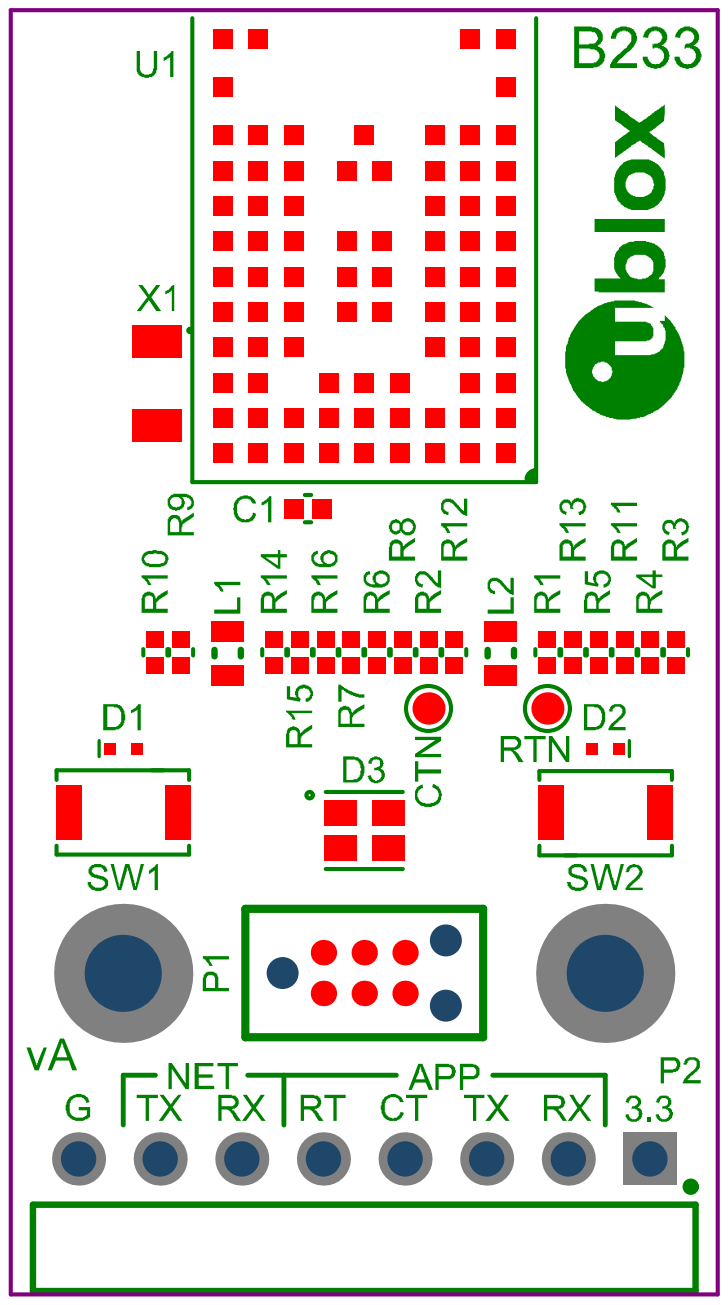
[picture p184: page 11]

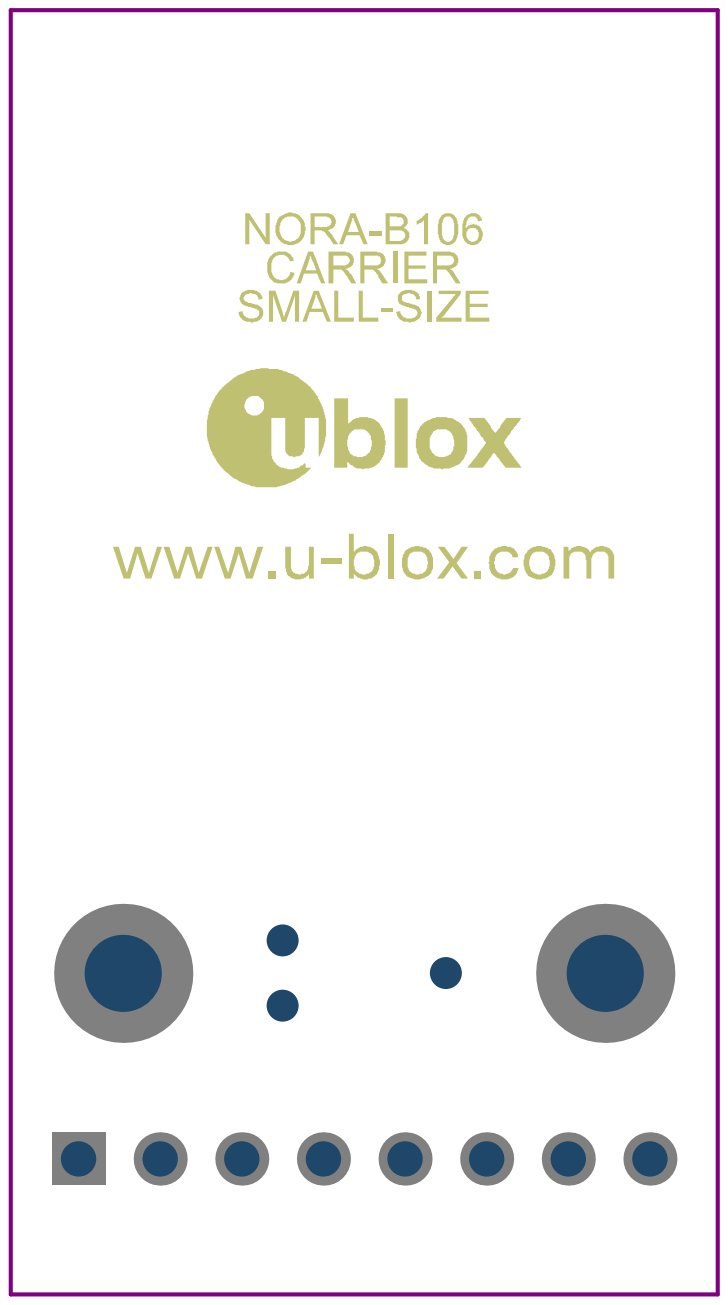
[picture p185: page 12]
